sporniket/kicad-conversions--atari-ste-motherboard--c300780-001/gallery/06--pcb-raytrace-south-east.png

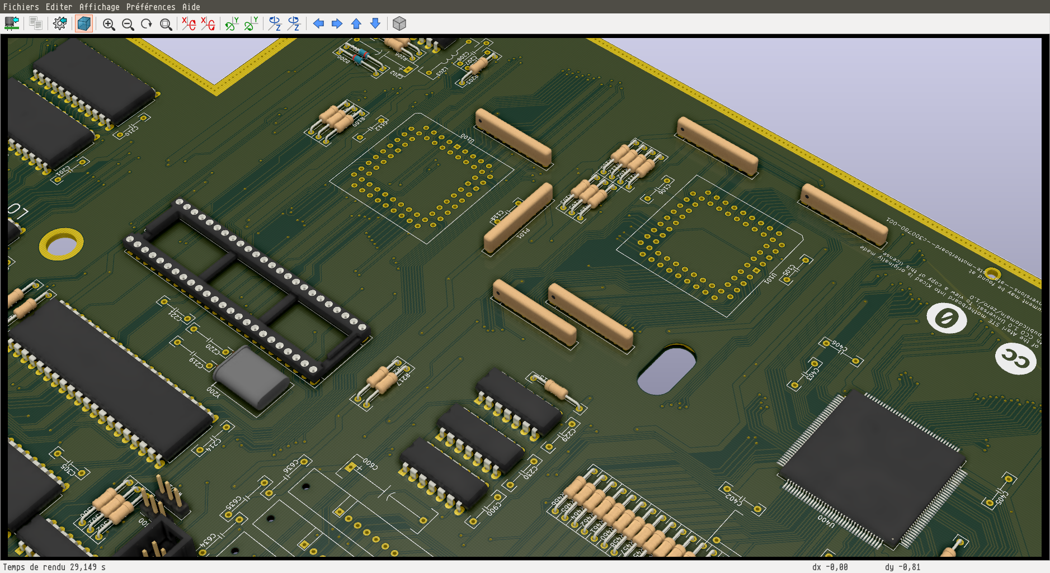
gallery/06--pcb-raytrace-south-east.png
