sporniket/kicad-conversions--atari-ste-motherboard--c300780-001/subsheet_100.kicad_sch

## KiCad design subsheet_100.kicad_sch (2025-09-03)

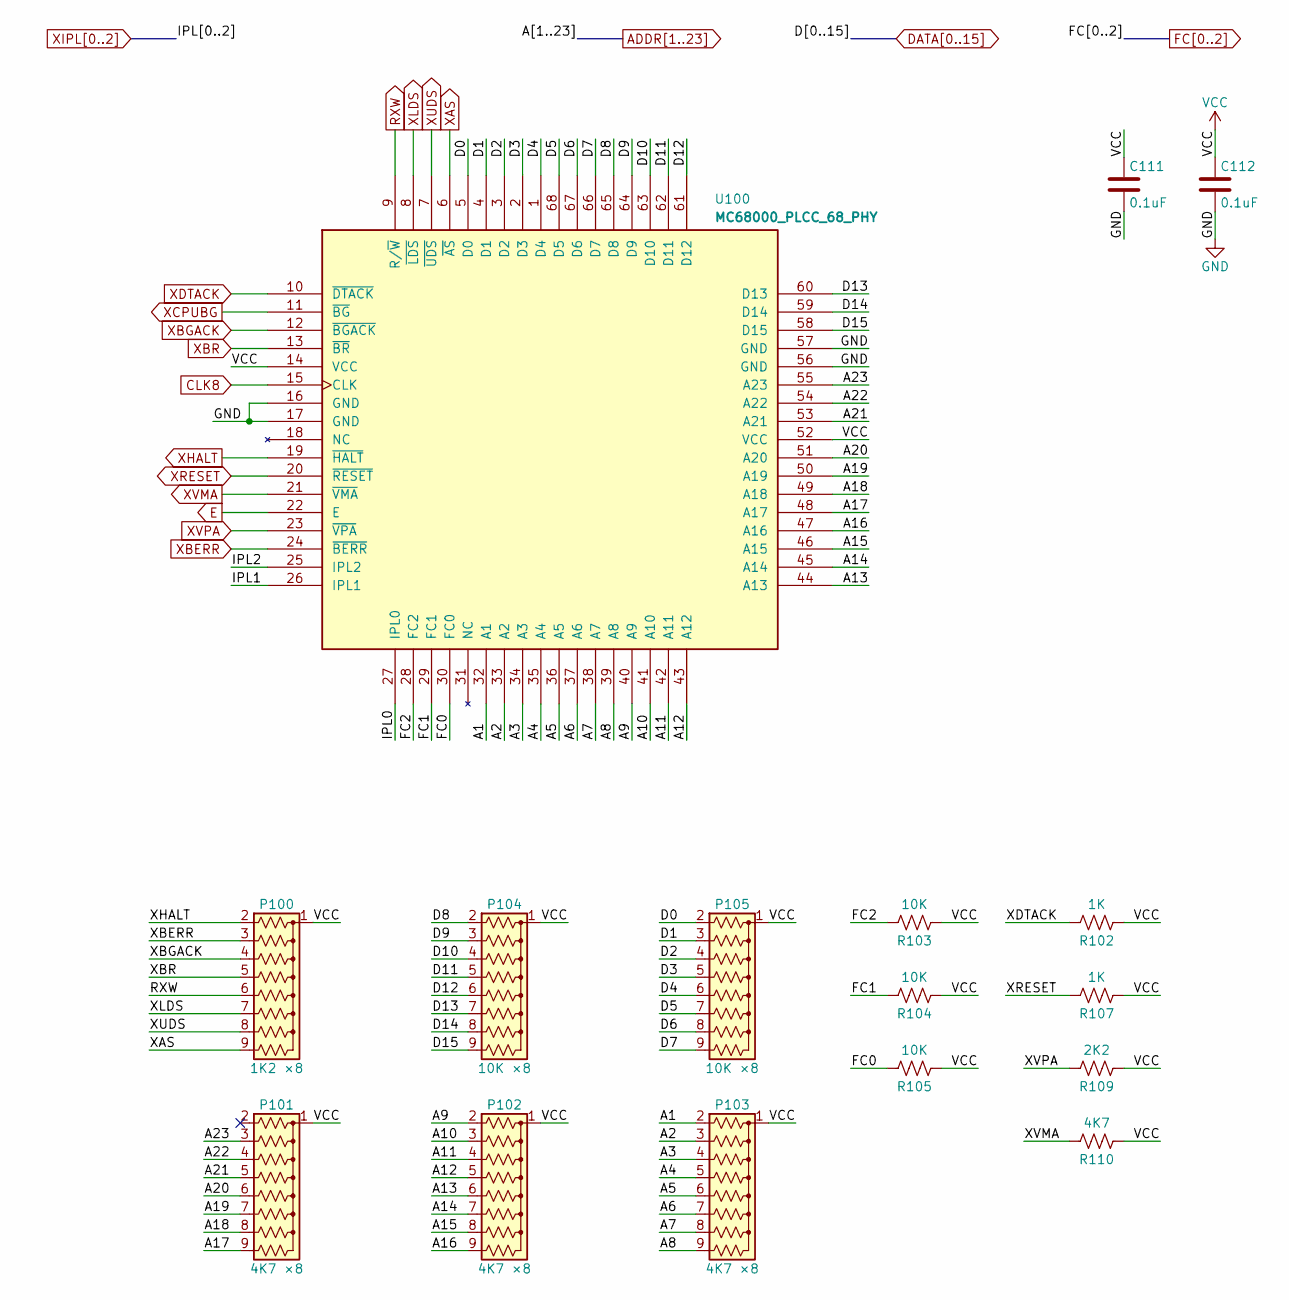
[picture p8: schematic subsheet_100.kicad_sch]

Parts:
C111, C112: 0.1uF; Passive_THT_capacitor_mlcc_W2.54mm_L7.62mm
P100: 1K2 ×8; R_Array_SIP9
P101, P102, P103: 4K7 ×8; R_Array_SIP9
P104, P105: 10K ×8; R_Array_SIP9
R102, R107: 1K; Passive_THT_resistor_W2.54mm_L12.70mm
R103, R104, R105: 10K; Passive_THT_resistor_W2.54mm_L12.70mm
R109: 2K2; Passive_THT_resistor_W2.54mm_L12.70mm
R110: 4K7; Passive_THT_resistor_W2.54mm_L12.70mm
U100: MC68000_PLCC_68_PHY; PLCC-68_THT-Socket

Connections:
A1: P103.2 (R1), U100.32 (A1)
A2: P103.3 (R2), U100.33 (A2)
A3: P103.4 (R3), U100.34 (A3)
A4: P103.5 (R4), U100.35 (A4)
A5: P103.6 (R5), U100.36 (A5)
A6: P103.7 (R6), U100.37 (A6)
A7: P103.8 (R7), U100.38 (A7)
A8: P103.9 (R8), U100.39 (A8)
A9: P102.2 (R1), U100.40 (A9)
A10: P102.3 (R2), U100.41 (A10)
A11: P102.4 (R3), U100.42 (A11)
A12: P102.5 (R4), U100.43 (A12)
A13: P102.6 (R5), U100.44 (A13)
A14: P102.7 (R6), U100.45 (A14)
A15: P102.8 (R7), U100.46 (A15)
A16: P102.9 (R8), U100.47 (A16)
A17: P101.9 (R8), U100.48 (A17)
A18: P101.8 (R7), U100.49 (A18)
A19: P101.7 (R6), U100.50 (A19)
A20: P101.6 (R5), U100.51 (A20)
A21: P101.5 (R4), U100.53 (A21)
A22: P101.4 (R3), U100.54 (A22)
A23: P101.3 (R2), U100.55 (A23)
CLK8: U100.15 (CLK)
D0: P105.2 (R1), U100.5 (D0)
D1: P105.3 (R2), U100.4 (D1)
D2: P105.4 (R3), U100.3 (D2)
D3: P105.5 (R4), U100.2 (D3)
D4: P105.6 (R5), U100.1 (D4)
D5: P105.7 (R6), U100.68 (D5)
D6: P105.8 (R7), U100.67 (D6)
D7: P105.9 (R8), U100.66 (D7)
D8: P104.2 (R1), U100.65 (D8)
D9: P104.3 (R2), U100.64 (D9)
D10: P104.4 (R3), U100.63 (D10)
D11: P104.5 (R4), U100.62 (D11)
D12: P104.6 (R5), U100.61 (D12)
D13: P104.7 (R6), U100.60 (D13)
D14: P104.8 (R7), U100.59 (D14)
D15: P104.9 (R8), U100.58 (D15)
E: U100.22 (E)
FC0: R105.2, U100.30 (FC0)
FC1: R104.2, U100.29 (FC1)
FC2: R103.2, U100.28 (FC2)
GND: C111.2, C112.2, U100.16 (GND), U100.17 (GND), U100.56 (GND), U100.57 (GND)
IPL0: U100.27 (IPL0)
IPL1: U100.26 (IPL1)
IPL2: U100.25 (IPL2)
RXW: P100.6 (R5), U100.9 (R/~W)
VCC: C111.1, C112.1, P100.1 (common), P101.1 (common), P102.1 (common), P103.1 (common), P104.1 (common), P105.1 (common), R102.1, R103.1, R104.1, R105.1, R107.1, R109.1, R110.1, U100.14 (VCC), U100.52 (VCC)
XAS: P100.9 (R8), U100.6 (~AS)
XBERR: P100.3 (R2), U100.24 (~BERR)
XBGACK: P100.4 (R3), U100.12 (~BGACK)
XBR: P100.5 (R4), U100.13 (~BR)
XCPUBG: U100.11 (~BG)
XDTACK: R102.2, U100.10 (~DTACK)
XHALT: P100.2 (R1), U100.19 (~HALT)
XLDS: P100.7 (R6), U100.8 (~LDS)
XRESET: R107.2, U100.20 (~RESET)
XUDS: P100.8 (R7), U100.7 (~UDS)
XVMA: R110.2, U100.21 (~VMA)
XVPA: R109.2, U100.23 (~VPA)
