sporniket/kicad-conversions--atari-ste-motherboard--c300780-001/subsheet_101.kicad_sch

## KiCad design subsheet_101.kicad_sch (2025-09-03)

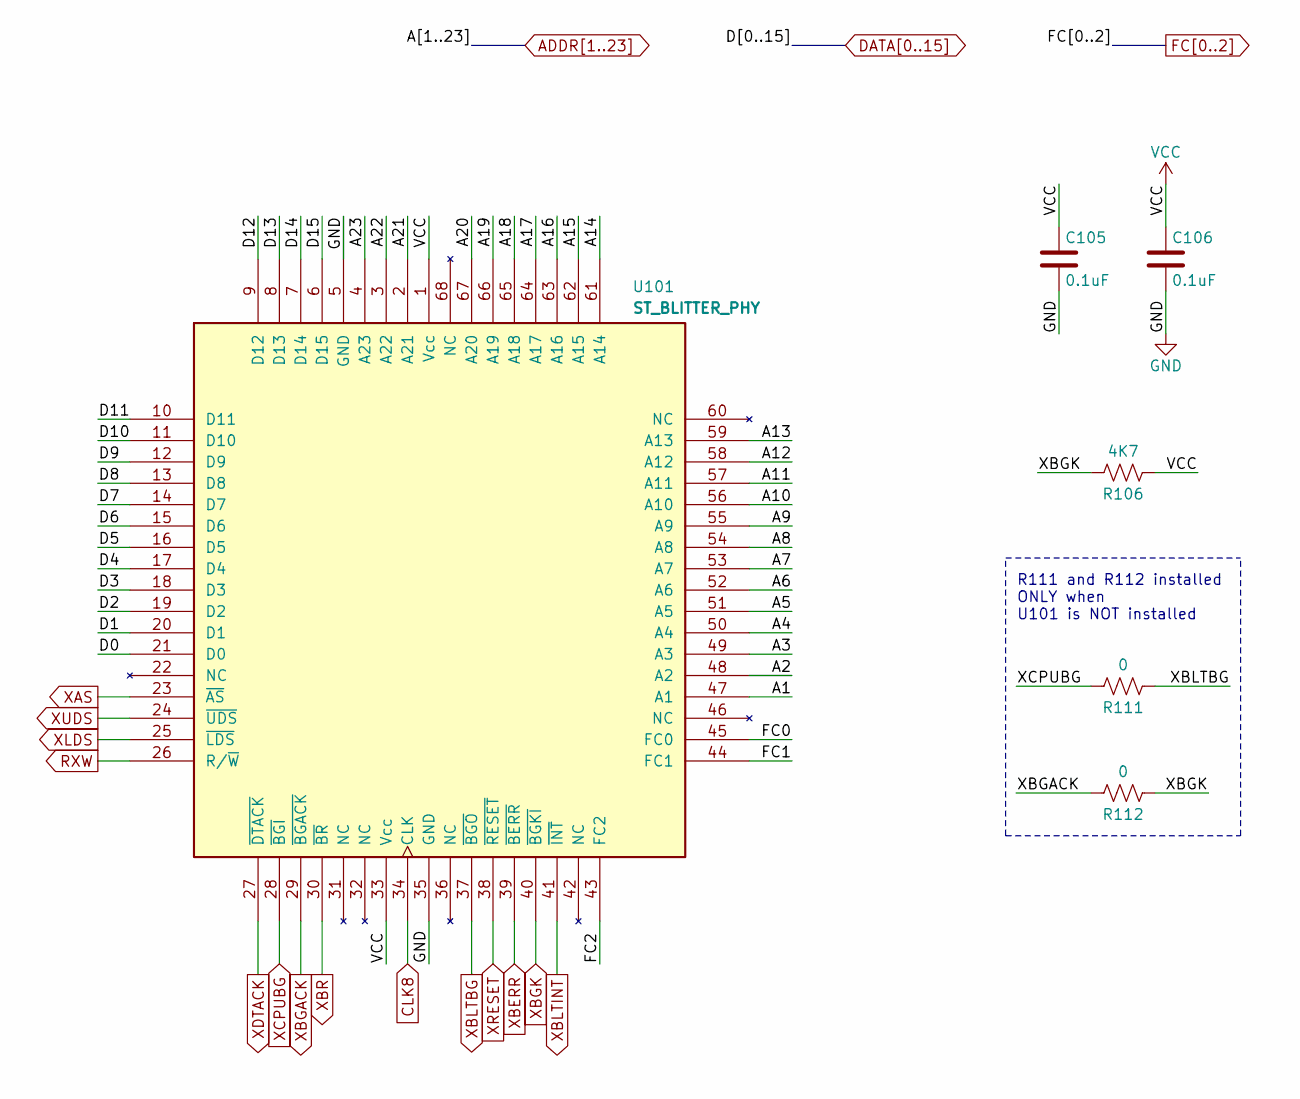
[picture p9: schematic subsheet_101.kicad_sch]

Parts:
C105, C106: 0.1uF; Passive_THT_capacitor_mlcc_W2.54mm_L7.62mm
R106: 4K7; Passive_THT_resistor_W2.54mm_L12.70mm
R111, R112: 0; Passive_THT_resistor_W2.54mm_L12.70mm
U101: ST_BLITTER_PHY; PLCC-68_THT-Socket

Connections:
A1: U101.47 (A1)
A2: U101.48 (A2)
A3: U101.49 (A3)
A4: U101.50 (A4)
A5: U101.51 (A5)
A6: U101.52 (A6)
A7: U101.53 (A7)
A8: U101.54 (A8)
A9: U101.55 (A9)
A10: U101.56 (A10)
A11: U101.57 (A11)
A12: U101.58 (A12)
A13: U101.59 (A13)
A14: U101.61 (A14)
A15: U101.62 (A15)
A16: U101.63 (A16)
A17: U101.64 (A17)
A18: U101.65 (A18)
A19: U101.66 (A19)
A20: U101.67 (A20)
A21: U101.2 (A21)
A22: U101.3 (A22)
A23: U101.4 (A23)
CLK8: U101.34 (CLK)
D0: U101.21 (D0)
D1: U101.20 (D1)
D2: U101.19 (D2)
D3: U101.18 (D3)
D4: U101.17 (D4)
D5: U101.16 (D5)
D6: U101.15 (D6)
D7: U101.14 (D7)
D8: U101.13 (D8)
D9: U101.12 (D9)
D10: U101.11 (D10)
D11: U101.10 (D11)
D12: U101.9 (D12)
D13: U101.8 (D13)
D14: U101.7 (D14)
D15: U101.6 (D15)
FC0: U101.45 (FC0)
FC1: U101.44 (FC1)
FC2: U101.43 (FC2)
GND: C105.2, C106.2, U101.5 (GND), U101.35 (GND)
RXW: U101.26 (R/~W)
VCC: C105.1, C106.1, R106.1, U101.1 (Vcc), U101.33 (Vcc)
XAS: U101.23 (~AS)
XBERR: U101.39 (~BERR)
XBGACK: R112.2, U101.29 (~BGACK)
XBGK: R106.2, R112.1, U101.40 (~BGKI)
XBLTBG: R111.1, U101.37 (~BGO)
XBLTINT: U101.41 (~INT)
XBR: U101.30 (~BR)
XCPUBG: R111.2, U101.28 (~BGI)
XDTACK: U101.27 (~DTACK)
XLDS: U101.25 (~LDS)
XRESET: U101.38 (~RESET)
XUDS: U101.24 (~UDS)

Notes on the sheet:
R111 and R112 installed ONLY when U101 is NOT installed
