sporniket/kicad-conversions--atari-ste-motherboard--c300780-001/subsheet_102.kicad_sch

## KiCad design subsheet_102.kicad_sch (2025-09-03)

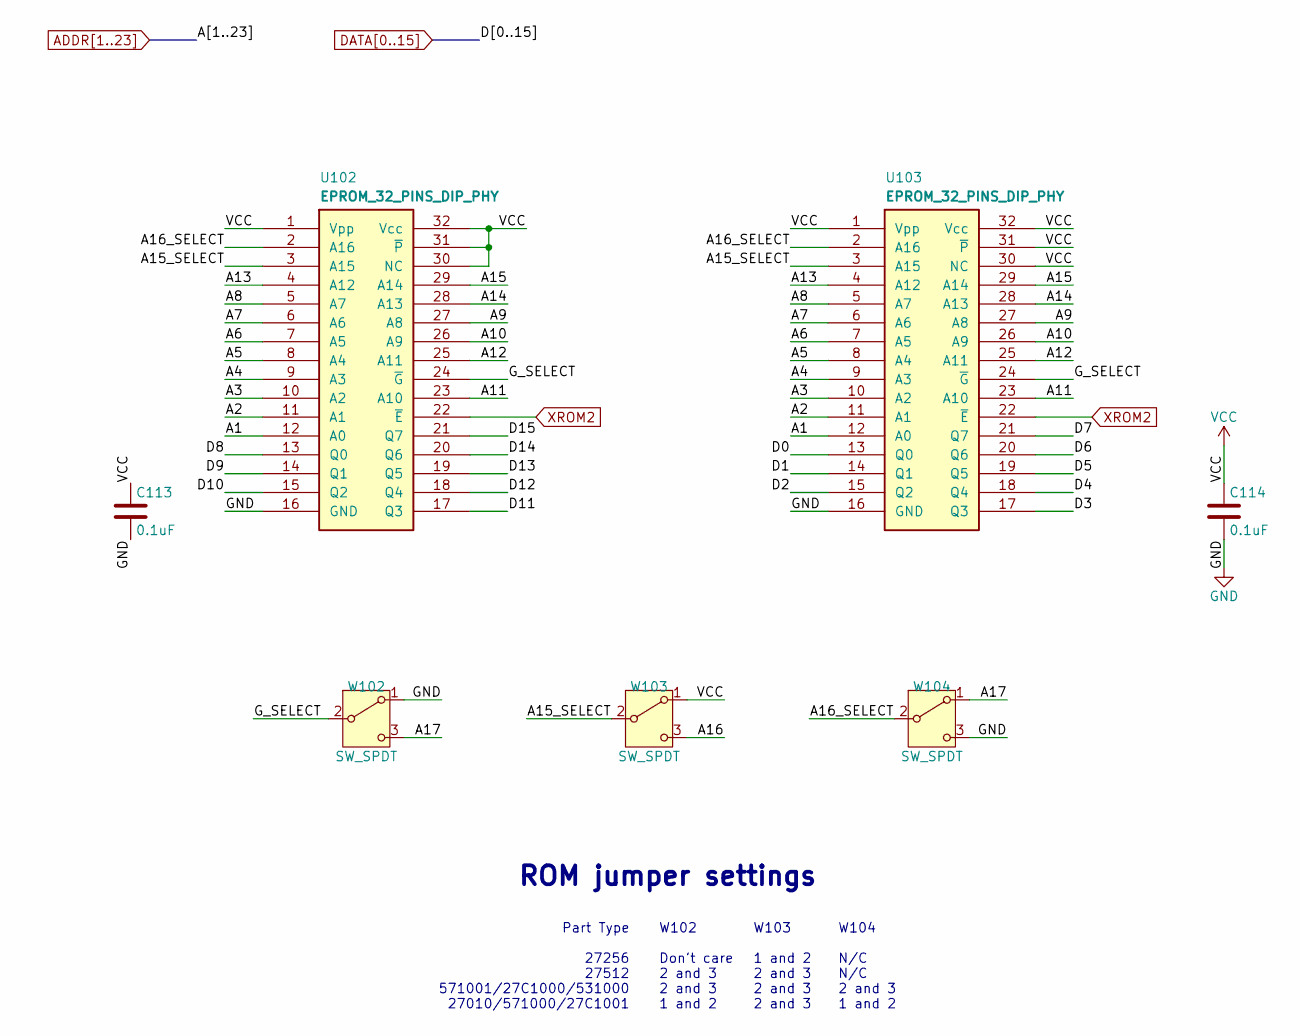
[picture p10: schematic subsheet_102.kicad_sch]

Parts:
C113, C114: 0.1uF; Passive_THT_capacitor_mlcc_W2.54mm_L7.62mm
U102, U103: EPROM_32_PINS_DIP_PHY; DIP-32_W15.24mm_LongPads
W102, W103, W104: SW_SPDT; PinHeader_1x03_P2.54mm_Vertical

Connections:
A1: U102.12 (A0), U103.12 (A0)
A2: U102.11 (A1), U103.11 (A1)
A3: U102.10 (A2), U103.10 (A2)
A4: U102.9 (A3), U103.9 (A3)
A5: U102.8 (A4), U103.8 (A4)
A6: U102.7 (A5), U103.7 (A5)
A7: U102.6 (A6), U103.6 (A6)
A8: U102.5 (A7), U103.5 (A7)
A9: U102.27 (A8), U103.27 (A8)
A10: U102.26 (A9), U103.26 (A9)
A11: U102.23 (A10), U103.23 (A10)
A12: U102.25 (A11), U103.25 (A11)
A13: U102.4 (A12), U103.4 (A12)
A14: U102.28 (A13), U103.28 (A13)
A15: U102.29 (A14), U103.29 (A14)
A15_SELECT: U102.3 (A15), U103.3 (A15), W103.2 (B)
A16: W103.3 (C)
A16_SELECT: U102.2 (A16), U103.2 (A16), W104.2 (B)
A17: W102.3 (C), W104.1 (A)
D0: U103.13 (Q0)
D1: U103.14 (Q1)
D2: U103.15 (Q2)
D3: U103.17 (Q3)
D4: U103.18 (Q4)
D5: U103.19 (Q5)
D6: U103.20 (Q6)
D7: U103.21 (Q7)
D8: U102.13 (Q0)
D9: U102.14 (Q1)
D10: U102.15 (Q2)
D11: U102.17 (Q3)
D12: U102.18 (Q4)
D13: U102.19 (Q5)
D14: U102.20 (Q6)
D15: U102.21 (Q7)
GND: C113.2, C114.2, U102.16 (GND), U103.16 (GND), W102.1 (A), W104.3 (C)
G_SELECT: U102.24 (~G), U103.24 (~G), W102.2 (B)
VCC: C113.1, C114.1, U102.1 (Vpp), U102.30 (NC), U102.31 (~P), U102.32 (Vcc), U103.1 (Vpp), U103.30 (NC), U103.31 (~P), U103.32 (Vcc), W103.1 (A)
XROM2: U102.22 (~E), U103.22 (~E)

Notes on the sheet:
W102 Don't care 2 and 3 2 and 3 1 and 2
Part Type 27256 27512 571001/27C1000/531000 27010/571000/27C1001
W104 N/C N/C 2 and 3 1 and 2
W103 1 and 2 2 and 3 2 and 3 2 and 3
ROM jumper settings
