sporniket/kicad-conversions--atari-ste-motherboard--c300780-001/subsheet_103.kicad_sch

## KiCad design subsheet_103.kicad_sch (2025-09-03)

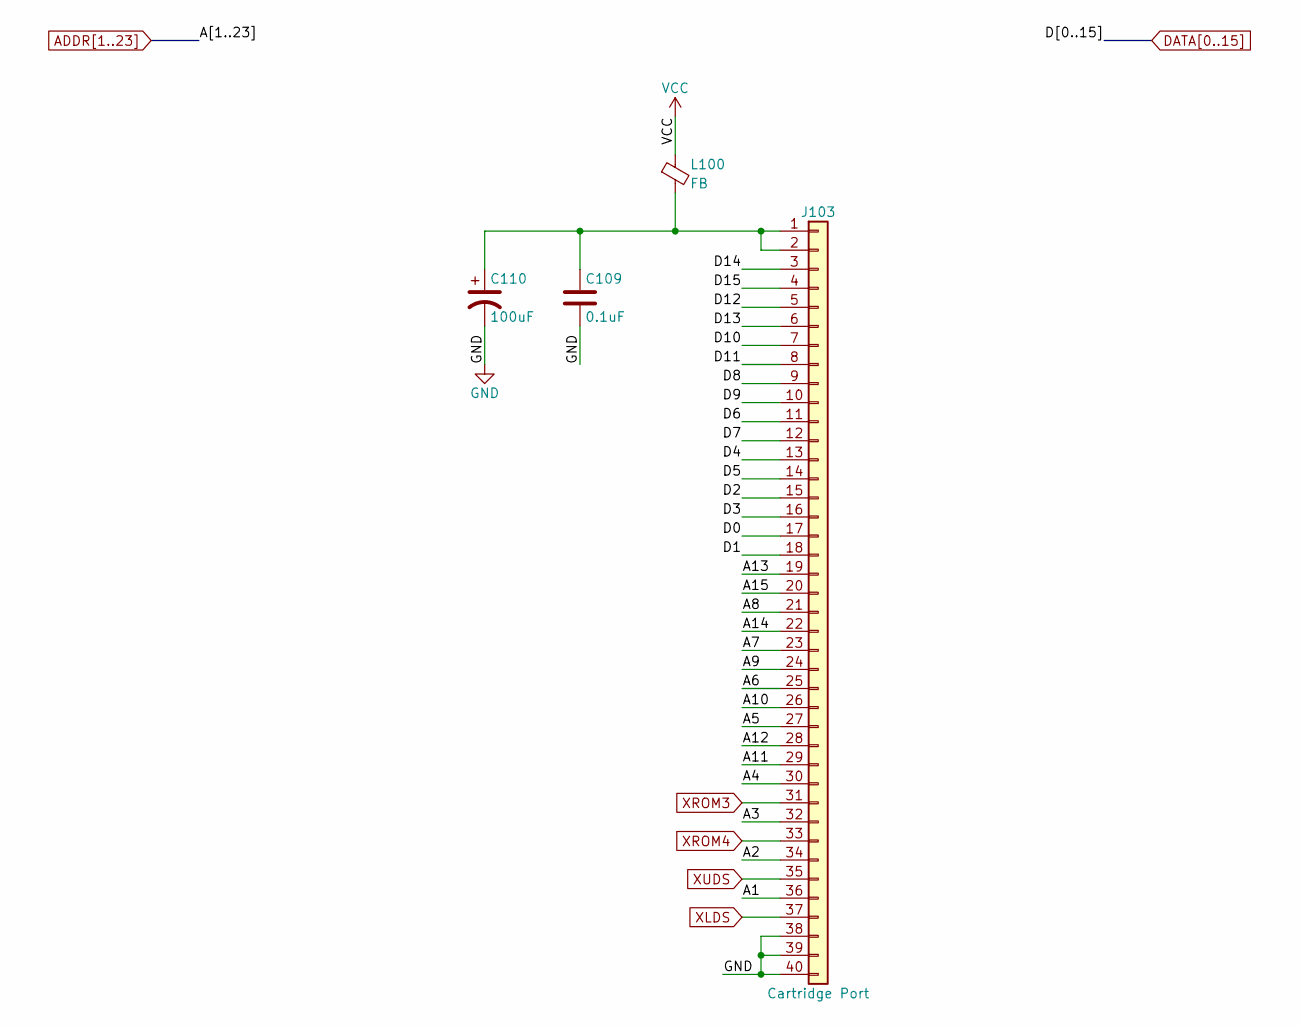
[picture p11: schematic subsheet_103.kicad_sch]

Parts:
C109: 0.1uF; Passive_THT_capacitor_mlcc_W2.54mm_L7.62mm
C110: 100uF; Passive_THT_capacitor_polarized_W6.35mm_L20.32mm
J103: Cartridge Port; socket-edge-pcb_40p_P2.01mm
L100: FB; Passive_THT_ferrite_bead_W3.81mm_L15.24mm

Connections:
A1: J103.36
A2: J103.34
A3: J103.32
A4: J103.30
A5: J103.27
A6: J103.25
A7: J103.23
A8: J103.21
A9: J103.24
A10: J103.26
A11: J103.29
A12: J103.28
A13: J103.19
A14: J103.22
A15: J103.20
D0: J103.17
D1: J103.18
D2: J103.15
D3: J103.16
D4: J103.13
D5: J103.14
D6: J103.11
D7: J103.12
D8: J103.9
D9: J103.10
D10: J103.7
D11: J103.8
D12: J103.5
D13: J103.6
D14: J103.3
D15: J103.4
GND: C109.2, C110.2, J103.38, J103.39, J103.40
unnamed: C109.1, C110.1, J103.1, J103.2, L100.2
VCC: L100.1
XLDS: J103.37
XROM3: J103.31
XROM4: J103.33
XUDS: J103.35
