sporniket/kicad-conversions--atari-ste-motherboard--c300780-001/subsheet_104.kicad_sch

## KiCad design subsheet_104.kicad_sch (2025-09-03)

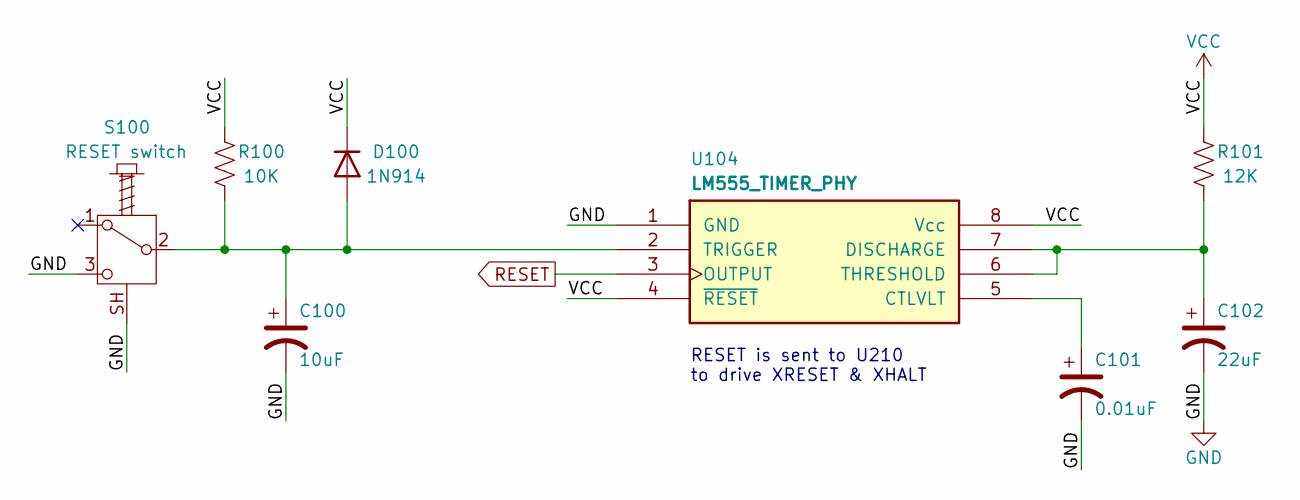
[picture p12: schematic subsheet_104.kicad_sch]

Parts:
C100: 10uF; Passive_THT_capacitor_polarized_W5.08mm_L17.78mm
C101: 0.01uF; Passive_THT_capacitor_W2.54mm_L10.16mm
C102: 22uF; Passive_THT_capacitor_polarized_W6.35mm_L20.32mm
D100: 1N914; Passive_THT_diode_W2.54mm_L12.70mm
R100: 10K; Passive_THT_resistor_W2.54mm_L12.70mm
R101: 12K; Passive_THT_resistor_W2.54mm_L12.70mm
S100: RESET switch; switch-spdt-momentary-action_Reset_pushbutton
U104: LM555_TIMER_PHY; DIP-8_W7.62mm_LongPads

Connections:
GND: C100.2, C101.2, C102.2, S100.3 (C), S100.SH (Shield), U104.1 (GND)
unnamed: C100.1, D100.2 (A), R100.2, S100.2 (B), U104.2 (TRIGGER)
unnamed: C101.1, U104.5 (CTLVLT)
unnamed: C102.1, R101.2, U104.6 (THRESHOLD), U104.7 (DISCHARGE)
RESET: U104.3 (OUTPUT)
VCC: D100.1 (K), R100.1, R101.1, U104.4 (~RESET), U104.8 (Vcc)

Notes on the sheet:
RESET is sent to U210 to drive XRESET & XHALT
