sporniket/kicad-conversions--atari-ste-motherboard--c300780-001/subsheet_105.kicad_sch

## KiCad design subsheet_105.kicad_sch (2025-09-03)

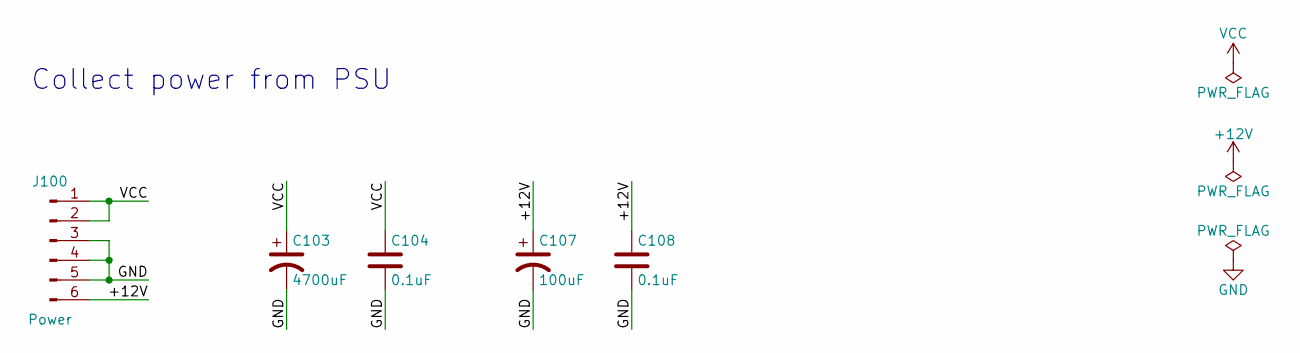
[picture p13: schematic subsheet_105.kicad_sch]

Parts:
C103: 4700uF; Passive_THT_capacitor_polarized_W16.51mm_L45.72mm
C104, C108: 0.1uF; Passive_THT_capacitor_mlcc_W2.54mm_L7.62mm
C107: 100uF; Passive_THT_capacitor_polarized_W6.35mm_L20.32mm
J100: Power; Molex_KK-254_AE-6410-06A_1x06_P2.54mm_Vertical

Connections:
+12V: C107.1, C108.1, J100.6
GND: C103.2, C104.2, C107.2, C108.2, J100.3, J100.4, J100.5
VCC: C103.1, C104.1, J100.1, J100.2

Notes on the sheet:
Collect power from PSU
