sporniket/kicad-conversions--atari-ste-motherboard--c300780-001/subsheet_106.kicad_sch

## KiCad design subsheet_106.kicad_sch (2025-09-03)

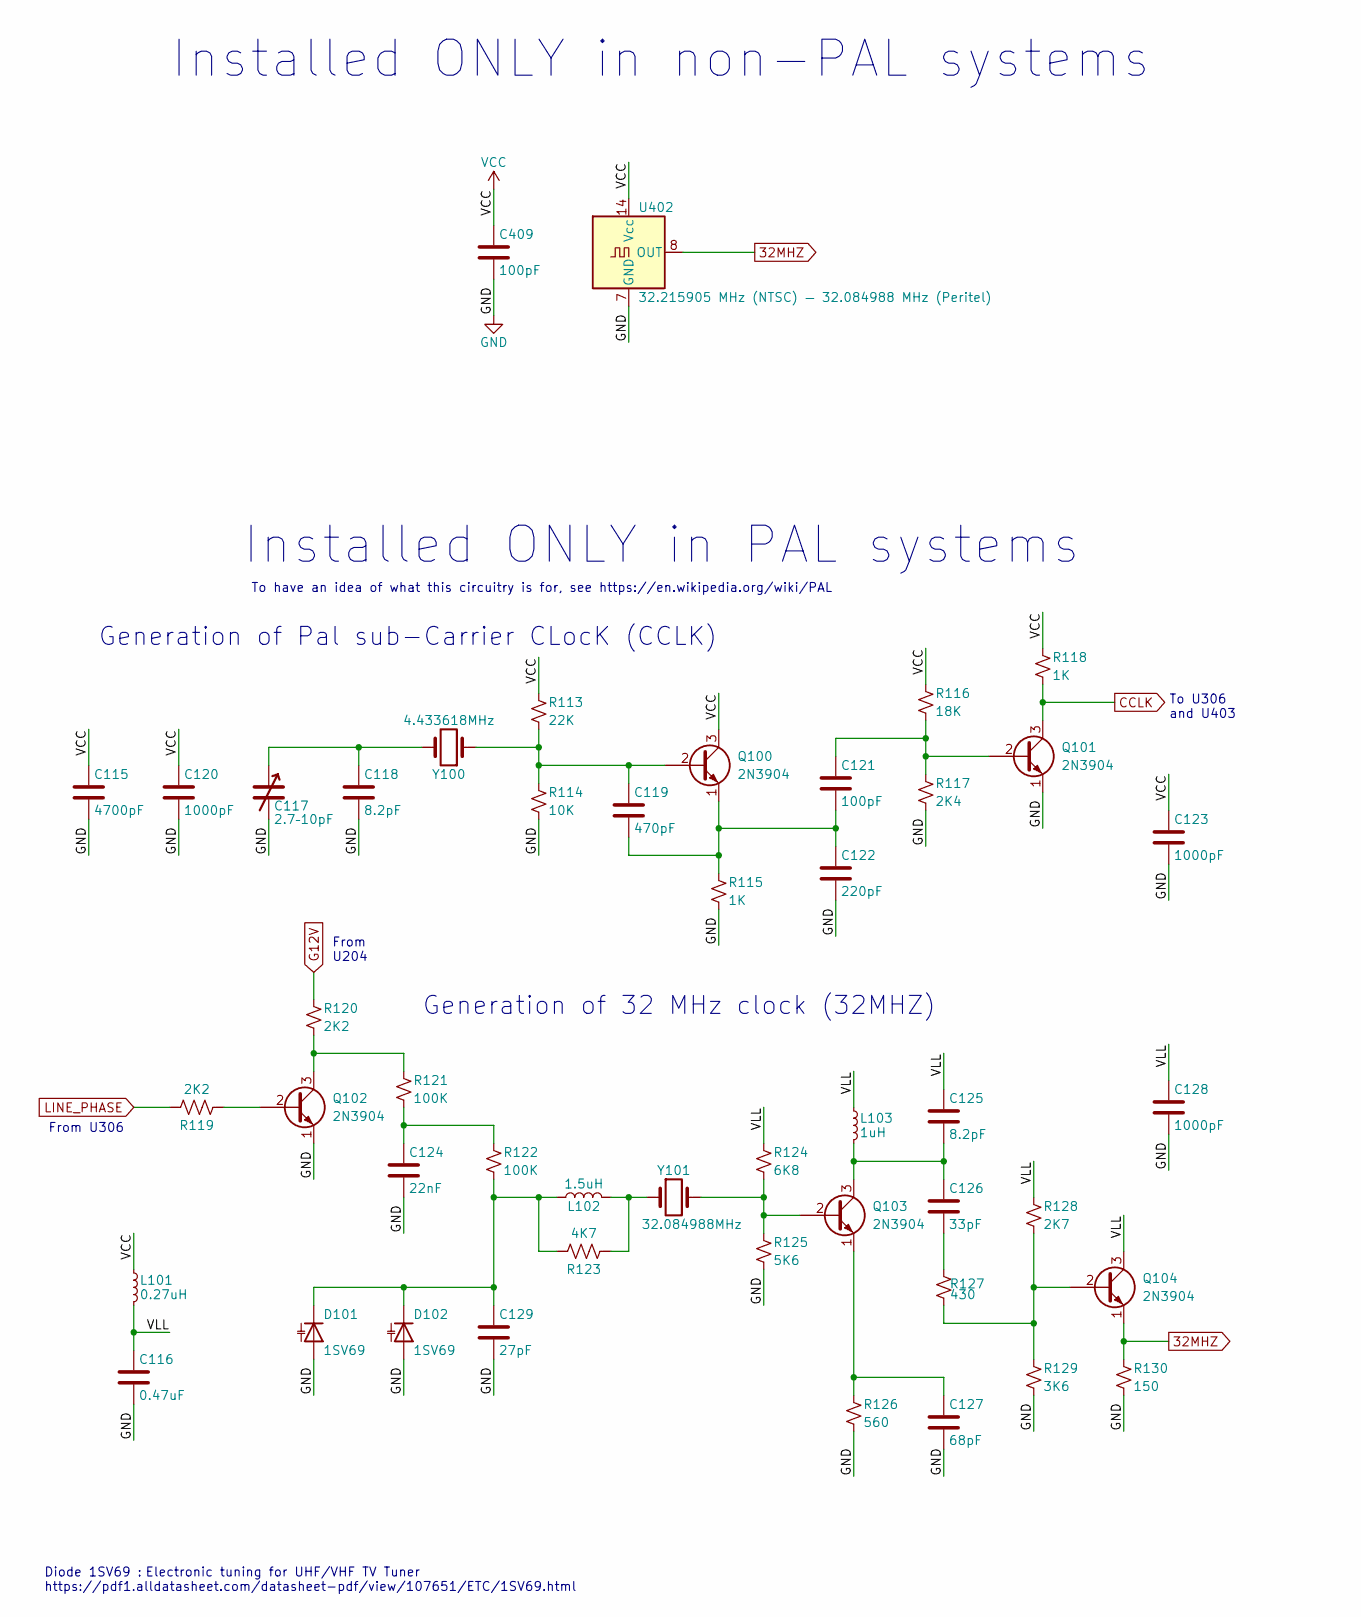
[picture p14: schematic subsheet_106.kicad_sch]

Parts:
C115: 4700pF; Passive_THT_capacitor_W2.54mm_L10.16mm
C116: 0.47uF; Passive_THT_capacitor_mlcc_W2.54mm_L10.16mm
C117: 2.7–10pF; Passive_THT_variable_capacitor_rad_D7.62mm_P5.08mm
C118: 8.2pF; Passive_THT_capacitor_W2.54mm_L12.70mm
C119: 470pF; Passive_THT_capacitor_W2.54mm_L12.70mm
C120: 1000pF; Passive_THT_capacitor_W2.54mm_L12.70mm
C121: 100pF; Passive_THT_capacitor_W2.54mm_L10.16mm
C122: 220pF; Passive_THT_capacitor_W2.54mm_L12.70mm
C123, C128: 1000pF; Passive_THT_capacitor_W2.54mm_L10.16mm
C124: 22nF; Passive_THT_capacitor_W2.54mm_L10.16mm
C125: 8.2pF; Passive_THT_capacitor_W2.54mm_L10.16mm
C126: 33pF; Passive_THT_capacitor_W2.54mm_L10.16mm
C127: 68pF; Passive_THT_capacitor_W2.54mm_L10.16mm
C129: 27pF; Passive_THT_capacitor_W2.54mm_L10.16mm
C409: 100pF; Passive_THT_capacitor_mlcc_W2.54mm_L7.62mm
D101, D102: 1SV69; Passive_THT_diode_W2.54mm_L12.70mm
L101: 0.27uH; Passive_THT_inductor_W5.08mm_L15.24mm
L102: 1.5uH; Passive_THT_inductor_W5.08mm_L15.24mm
L103: 1uH; Passive_THT_inductor_W5.08mm_L15.24mm
Q100, Q101, Q102, Q103, Q104: 2N3904; TO-92_Inline_Wide
R113: 22K; Passive_THT_resistor_W2.54mm_L12.70mm
R114: 10K; Passive_THT_resistor_W2.54mm_L12.70mm
R115, R118: 1K; Passive_THT_resistor_W2.54mm_L12.70mm
R116: 18K; Passive_THT_resistor_W2.54mm_L12.70mm
R117: 2K4; Passive_THT_resistor_W2.54mm_L12.70mm
R119, R120: 2K2; Passive_THT_resistor_W2.54mm_L12.70mm
R121, R122: 100K; Passive_THT_resistor_W2.54mm_L12.70mm
R123: 4K7; Passive_THT_resistor_W2.54mm_L12.70mm
R124: 6K8; Passive_THT_resistor_W2.54mm_L12.70mm
R125: 5K6; Passive_THT_resistor_W2.54mm_L12.70mm
R126: 560; Passive_THT_resistor_W2.54mm_L12.70mm
R127: 430; Passive_THT_resistor_W2.54mm_L12.70mm
R128: 2K7; Passive_THT_resistor_W2.54mm_L12.70mm
R129: 3K6; Passive_THT_resistor_W2.54mm_L12.70mm
R130: 150; Passive_THT_resistor_W2.54mm_L12.70mm
U402: 32.215905 MHz (NTSC) — 32.084988 MHz (Peritel); Oscillator_DIP-14
Y100: 4.433618MHz; Crystal_HC18-U_Horizontal
Y101: 32.084988MHz; Crystal_HC18-U_Horizontal

Connections:
32MHZ: Q104.1 (E), R130.1, U402.8 (OUT)
CCLK: Q101.3 (C), R118.2
G12V: R120.1
GND: C115.2, C116.2, C117.2, C118.2, C120.2, C122.2, C123.2, C124.2, C127.2, C128.2, C129.2, C409.2, D101.2 (A), D102.2 (A), Q101.1 (E), Q102.1 (E), R114.2, R115.2, R117.2, R125.2, R126.2, R129.2, R130.2, U402.7 (GND)
LINE_PHASE: R119.2
unnamed: C117.1, C118.1, Y100.2
unnamed: C119.1, Q100.2 (B), R113.2, R114.1, Y100.1
unnamed: C119.2, C121.2, C122.1, Q100.1 (E), R115.1
unnamed: C121.1, Q101.2 (B), R116.2, R117.1
unnamed: C124.1, R121.2, R122.1
unnamed: C125.2, C126.1, L103.2, Q103.3 (C)
unnamed: C126.2, R127.1
unnamed: C127.1, Q103.1 (E), R126.1
unnamed: C129.1, D101.1 (K), D102.1 (K), L102.1, R122.2, R123.2
unnamed: L102.2, R123.1, Y101.1
unnamed: Q102.2 (B), R119.1
unnamed: Q102.3 (C), R120.2, R121.1
unnamed: Q103.2 (B), R124.2, R125.1, Y101.2
unnamed: Q104.2 (B), R127.2, R128.2, R129.1
VCC: C115.1, C120.1, C123.1, C409.1, L101.1, Q100.3 (C), R113.1, R116.1, R118.1, U402.14 (Vcc)
VLL: C116.1, C125.1, C128.1, L101.2, L103.1, Q104.3 (C), R124.1, R128.1

Notes on the sheet:
Installed ONLY in non-PAL systems
From U204
Diode 1SV69 : Electronic tuning for UHF/VHF TV Tuner https://pdf1.alldatasheet.com/datasheet-pdf/view/107651/ETC/1SV69.html
Generation of Pal sub-Carrier CLocK (CCLK)
Generation of 32 MHz clock (32MHZ)
From U306
To U306 and U403
Installed ONLY in PAL systems
To have an idea of what this circuitry is for, see https://en.wikipedia.org/wiki/PAL
