sporniket/kicad-conversions--atari-ste-motherboard--c300780-001/subsheet_200.kicad_sch

## KiCad design subsheet_200.kicad_sch (2025-09-03)

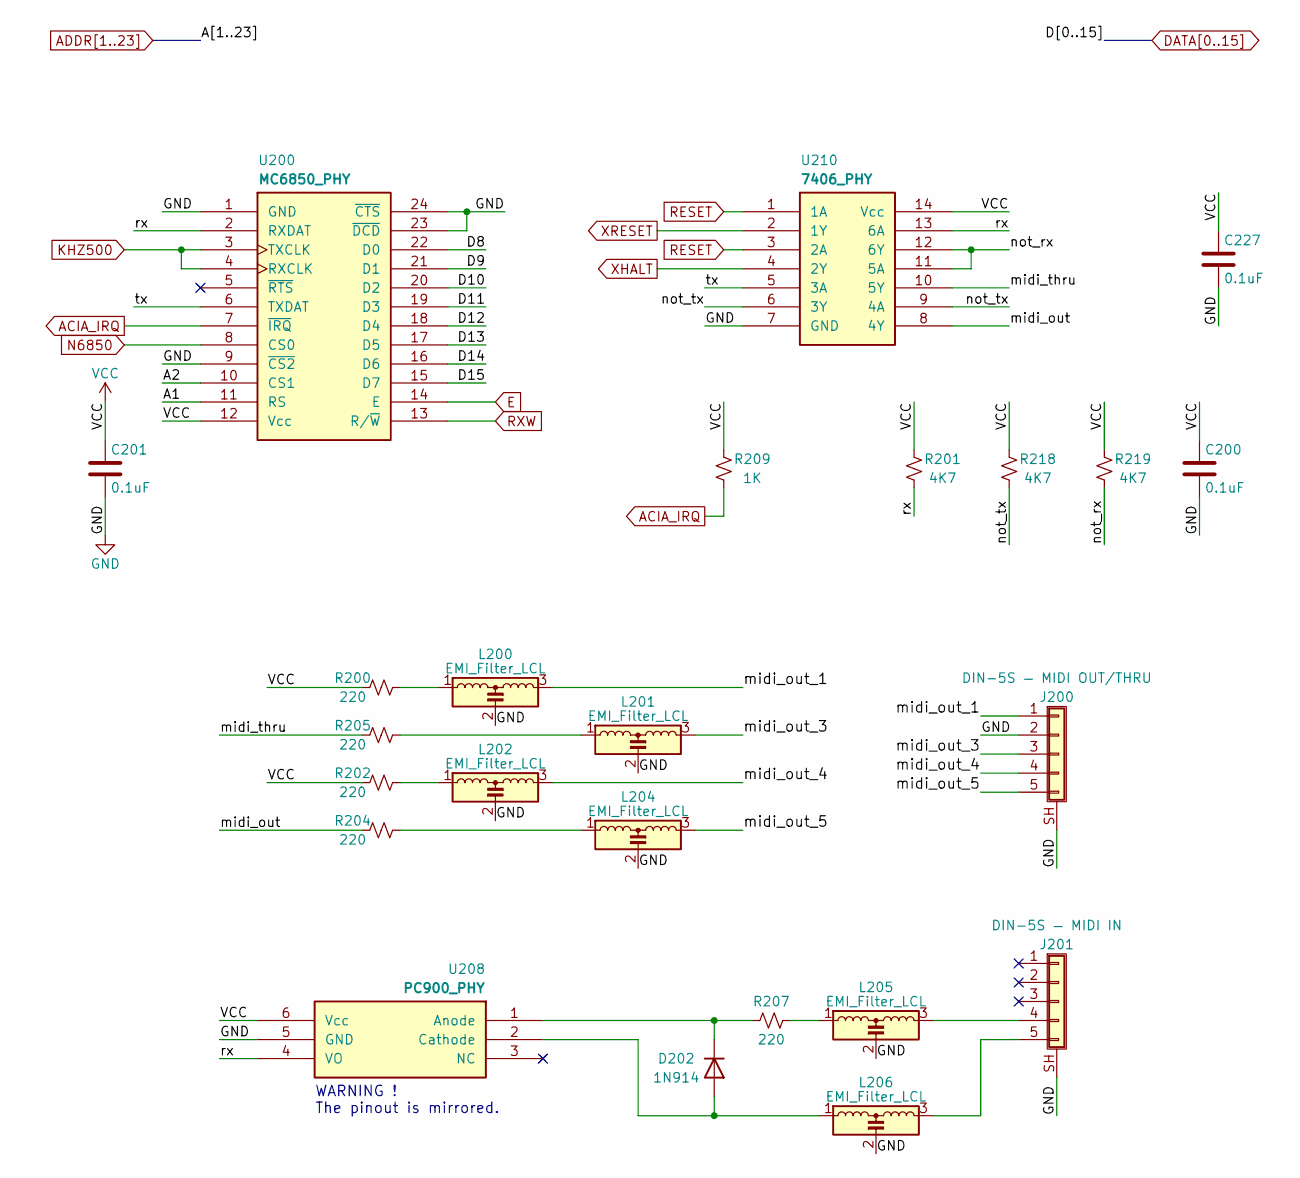
[picture p15: schematic subsheet_200.kicad_sch]

Parts:
C200, C201, C227: 0.1uF; Passive_THT_capacitor_mlcc_W2.54mm_L7.62mm
D202: 1N914; Passive_THT_diode_W2.54mm_L12.70mm
J200: DIN-5S — MIDI OUT/THRU; socket-din-5
J201: DIN-5S — MIDI IN; socket-din-5
L200, L201, L202, L204, L205, L206: EMI_Filter_LCL; Passive_THT_EMI_filter_W5.08mm_L7.62mm
R200, R202, R204, R205, R207: 220; Passive_THT_resistor_W2.54mm_L12.70mm
R201, R218, R219: 4K7; Passive_THT_resistor_W2.54mm_L12.70mm
R209: 1K; Passive_THT_resistor_W2.54mm_L12.70mm
U200: MC6850_PHY; DIP-24_W15.24mm_LongPads
U208: PC900_PHY; DIP-6_W7.62mm_LongPads
U210: 7406_PHY; DIP-14_W7.62mm_LongPads

Connections:
A1: U200.11 (RS)
A2: U200.10 (CS1)
ACIA_IRQ: R209.1, U200.7 (~IRQ)
D8: U200.22 (D0)
D9: U200.21 (D1)
D10: U200.20 (D2)
D11: U200.19 (D3)
D12: U200.18 (D4)
D13: U200.17 (D5)
D14: U200.16 (D6)
D15: U200.15 (D7)
E: U200.14 (E)
GND: C200.2, C201.2, C227.2, J200.2, J200.SH (Shield), J201.SH (Shield), L200.2, L201.2, L202.2, L204.2, L205.2, L206.2, U200.1 (GND), U200.9 (~CS2), U200.23 (~DCD), U200.24 (~CTS), U208.5 (GND), U210.7 (GND)
KHZ500: U200.3 (TXCLK), U200.4 (RXCLK)
N6850: U200.8 (CS0)
unnamed: D202.1 (K), R207.2, U208.1 (Anode)
unnamed: D202.2 (A), L206.1, U208.2 (Cathode)
unnamed: J201.4, L205.3
unnamed: J201.5, L206.3
unnamed: L200.1, R200.1
unnamed: L201.1, R205.1
unnamed: L202.1, R202.1
unnamed: L204.1, R204.1
unnamed: L205.1, R207.1
RESET: U210.1 (1A), U210.3 (2A)
RXW: U200.13 (R/~W)
VCC: C200.1, C201.1, C227.1, R200.2, R201.2, R202.2, R209.2, R218.2, R219.2, U200.12 (Vcc), U208.6 (Vcc), U210.14 (Vcc)
XHALT: U210.4 (2Y)
XRESET: U210.2 (1Y)
midi_out: R204.2, U210.8 (4Y)
midi_out_1: J200.1, L200.3
midi_out_3: J200.3, L201.3
midi_out_4: J200.4, L202.3
midi_out_5: J200.5, L204.3
midi_thru: R205.2, U210.10 (5Y)
not_rx: R219.1, U210.11 (5A), U210.12 (6Y)
not_tx: R218.1, U210.6 (3Y), U210.9 (4A)
rx: R201.1, U200.2 (RXDAT), U208.4 (VO), U210.13 (6A)
tx: U200.6 (TXDAT), U210.5 (3A)

Notes on the sheet:
WARNING ! The pinout is mirrored.
