sporniket/kicad-conversions--atari-ste-motherboard--c300780-001/subsheet_201.kicad_sch

## KiCad design subsheet_201.kicad_sch (2025-09-03)

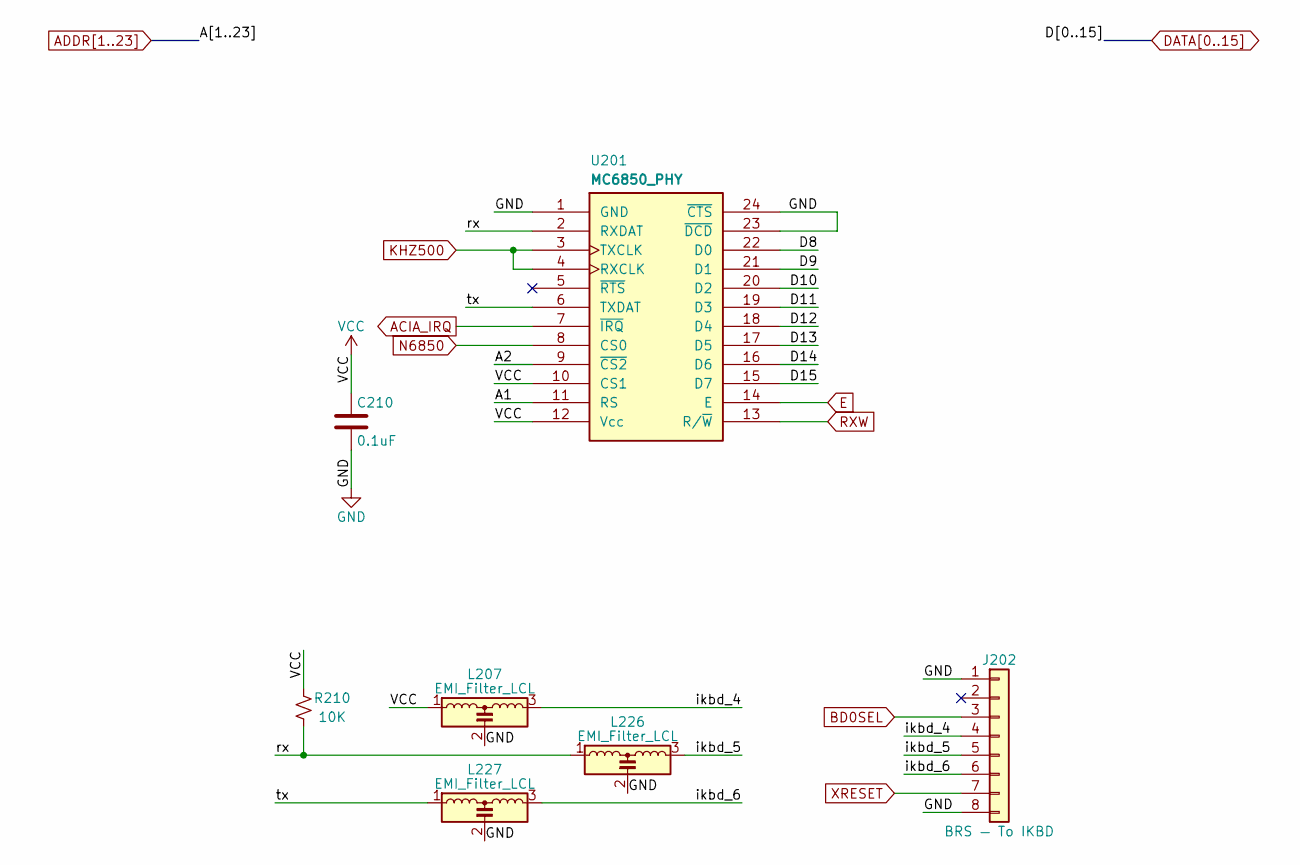
[picture p16: schematic subsheet_201.kicad_sch]

Parts:
C210: 0.1uF; Passive_THT_capacitor_mlcc_W2.54mm_L7.62mm
J202: BRS — To IKBD; PinHeader_1x08_P2.54mm_Vertical_Ikbd
L207, L226, L227: EMI_Filter_LCL; Passive_THT_EMI_filter_W5.08mm_L7.62mm
R210: 10K; Passive_THT_resistor_W2.54mm_L12.70mm
U201: MC6850_PHY; DIP-24_W15.24mm_LongPads

Connections:
A1: U201.11 (RS)
A2: U201.9 (~CS2)
ACIA_IRQ: U201.7 (~IRQ)
BD0SEL: J202.3
D8: U201.22 (D0)
D9: U201.21 (D1)
D10: U201.20 (D2)
D11: U201.19 (D3)
D12: U201.18 (D4)
D13: U201.17 (D5)
D14: U201.16 (D6)
D15: U201.15 (D7)
E: U201.14 (E)
GND: C210.2, J202.1, J202.8, L207.2, L226.2, L227.2, U201.1 (GND), U201.23 (~DCD), U201.24 (~CTS)
KHZ500: U201.3 (TXCLK), U201.4 (RXCLK)
N6850: U201.8 (CS0)
RXW: U201.13 (R/~W)
VCC: C210.1, L207.1, R210.2, U201.10 (CS1), U201.12 (Vcc)
XRESET: J202.7
ikbd_4: J202.4, L207.3
ikbd_5: J202.5, L226.3
ikbd_6: J202.6, L227.3
rx: L226.1, R210.1, U201.2 (RXDAT)
tx: L227.1, U201.6 (TXDAT)
