sporniket/kicad-conversions--atari-ste-motherboard--c300780-001/subsheet_202.kicad_sch

## KiCad design subsheet_202.kicad_sch (2025-09-03)

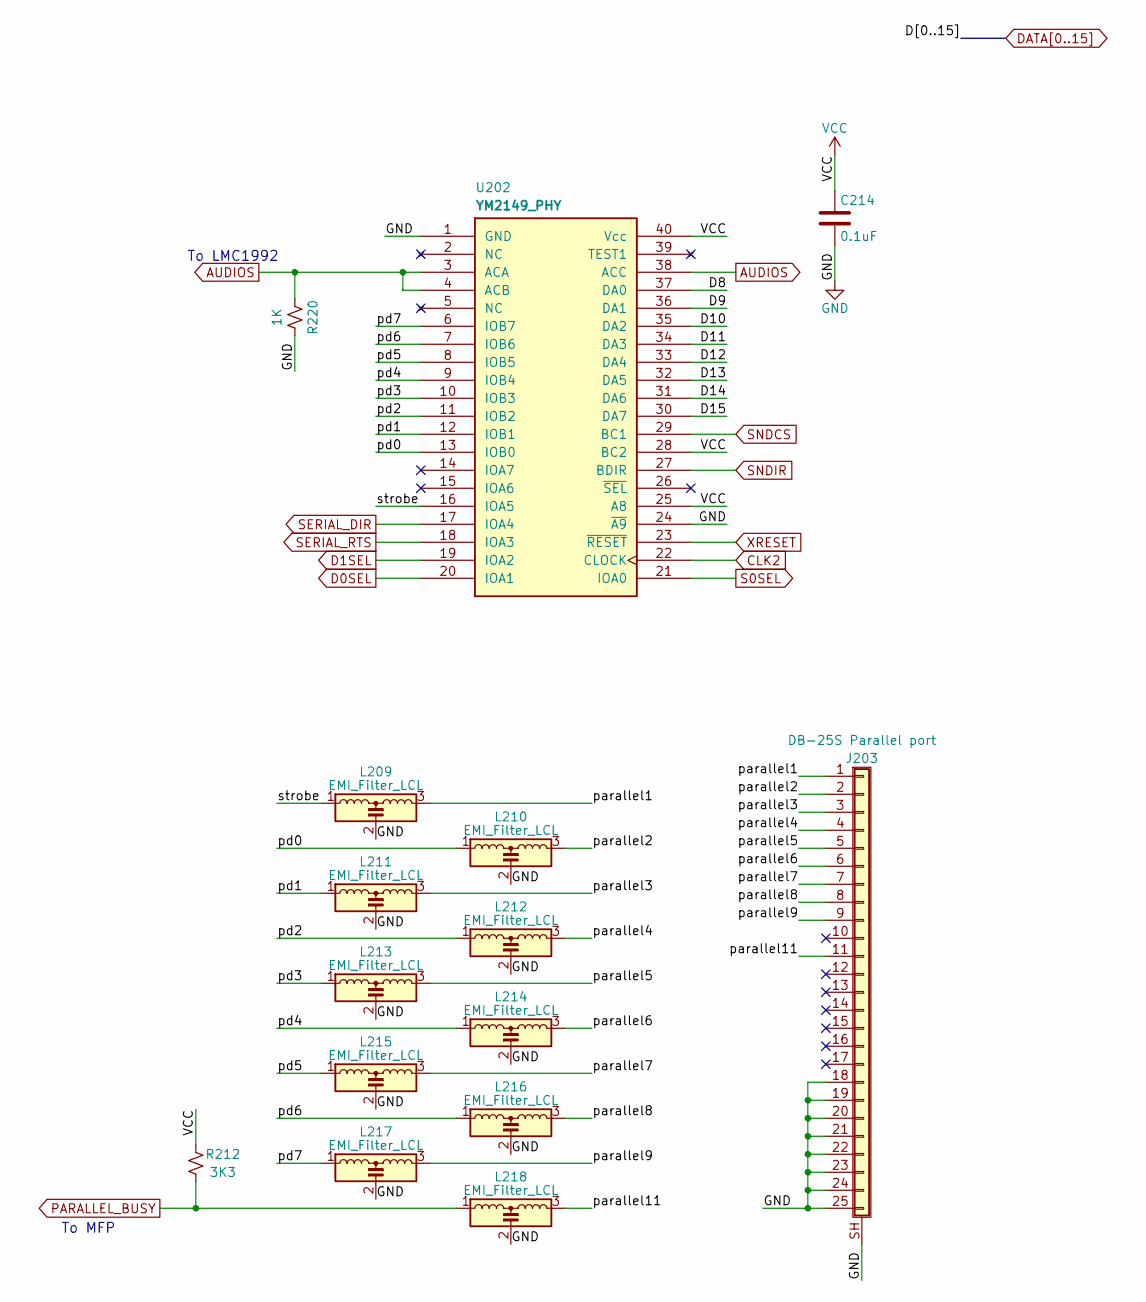
[picture p17: schematic subsheet_202.kicad_sch]

Parts:
C214: 0.1uF; Passive_THT_capacitor_mlcc_W2.54mm_L7.62mm
J203: DB-25S Parallel port; DSUB-25_Female_Horizontal_P2.77x2.84mm_EdgePinOffset7.70mm_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
L209, L210, L211, L212, L213, L214, L215, L216, L217, L218: EMI_Filter_LCL; Passive_THT_EMI_filter_W5.08mm_L7.62mm
R212: 3K3; Passive_THT_resistor_W2.54mm_L12.70mm
R220: 1K; Passive_THT_resistor_W2.54mm_L12.70mm
U202: YM2149_PHY; DIP-40_W15.24mm_LongPads

Connections:
AUDIOS: R220.2, U202.3 (ACA), U202.4 (ACB), U202.38 (ACC)
CLK2: U202.22 (CLOCK)
D0SEL: U202.20 (IOA1)
D1SEL: U202.19 (IOA2)
D8: U202.37 (DA0)
D9: U202.36 (DA1)
D10: U202.35 (DA2)
D11: U202.34 (DA3)
D12: U202.33 (DA4)
D13: U202.32 (DA5)
D14: U202.31 (DA6)
D15: U202.30 (DA7)
GND: C214.2, J203.18, J203.19, J203.20, J203.21, J203.22, J203.23, J203.24, J203.25, J203.SH (Shield), L209.2, L210.2, L211.2, L212.2, L213.2, L214.2, L215.2, L216.2, L217.2, L218.2, R220.1, U202.1 (GND), U202.24 (~A9)
PARALLEL_BUSY: L218.1, R212.2
S0SEL: U202.21 (IOA0)
SERIAL_DIR: U202.17 (IOA4)
SERIAL_RTS: U202.18 (IOA3)
SNDCS: U202.29 (BC1)
SNDIR: U202.27 (BDIR)
VCC: C214.1, R212.1, U202.25 (A8), U202.28 (BC2), U202.40 (Vcc)
XRESET: U202.23 (~RESET)
parallel1: J203.1, L209.3
parallel2: J203.2, L210.3
parallel3: J203.3, L211.3
parallel4: J203.4, L212.3
parallel5: J203.5, L213.3
parallel6: J203.6, L214.3
parallel7: J203.7, L215.3
parallel8: J203.8, L216.3
parallel9: J203.9, L217.3
parallel11: J203.11, L218.3
pd0: L210.1, U202.13 (IOB0)
pd1: L211.1, U202.12 (IOB1)
pd2: L212.1, U202.11 (IOB2)
pd3: L213.1, U202.10 (IOB3)
pd4: L214.1, U202.9 (IOB4)
pd5: L215.1, U202.8 (IOB5)
pd6: L216.1, U202.7 (IOB6)
pd7: L217.1, U202.6 (IOB7)
strobe: L209.1, U202.16 (IOA5)

Notes on the sheet:
To MFP
To LMC1992
