sporniket/kicad-conversions--atari-ste-motherboard--c300780-001/subsheet_203.kicad_sch

## KiCad design subsheet_203.kicad_sch (2025-09-03)

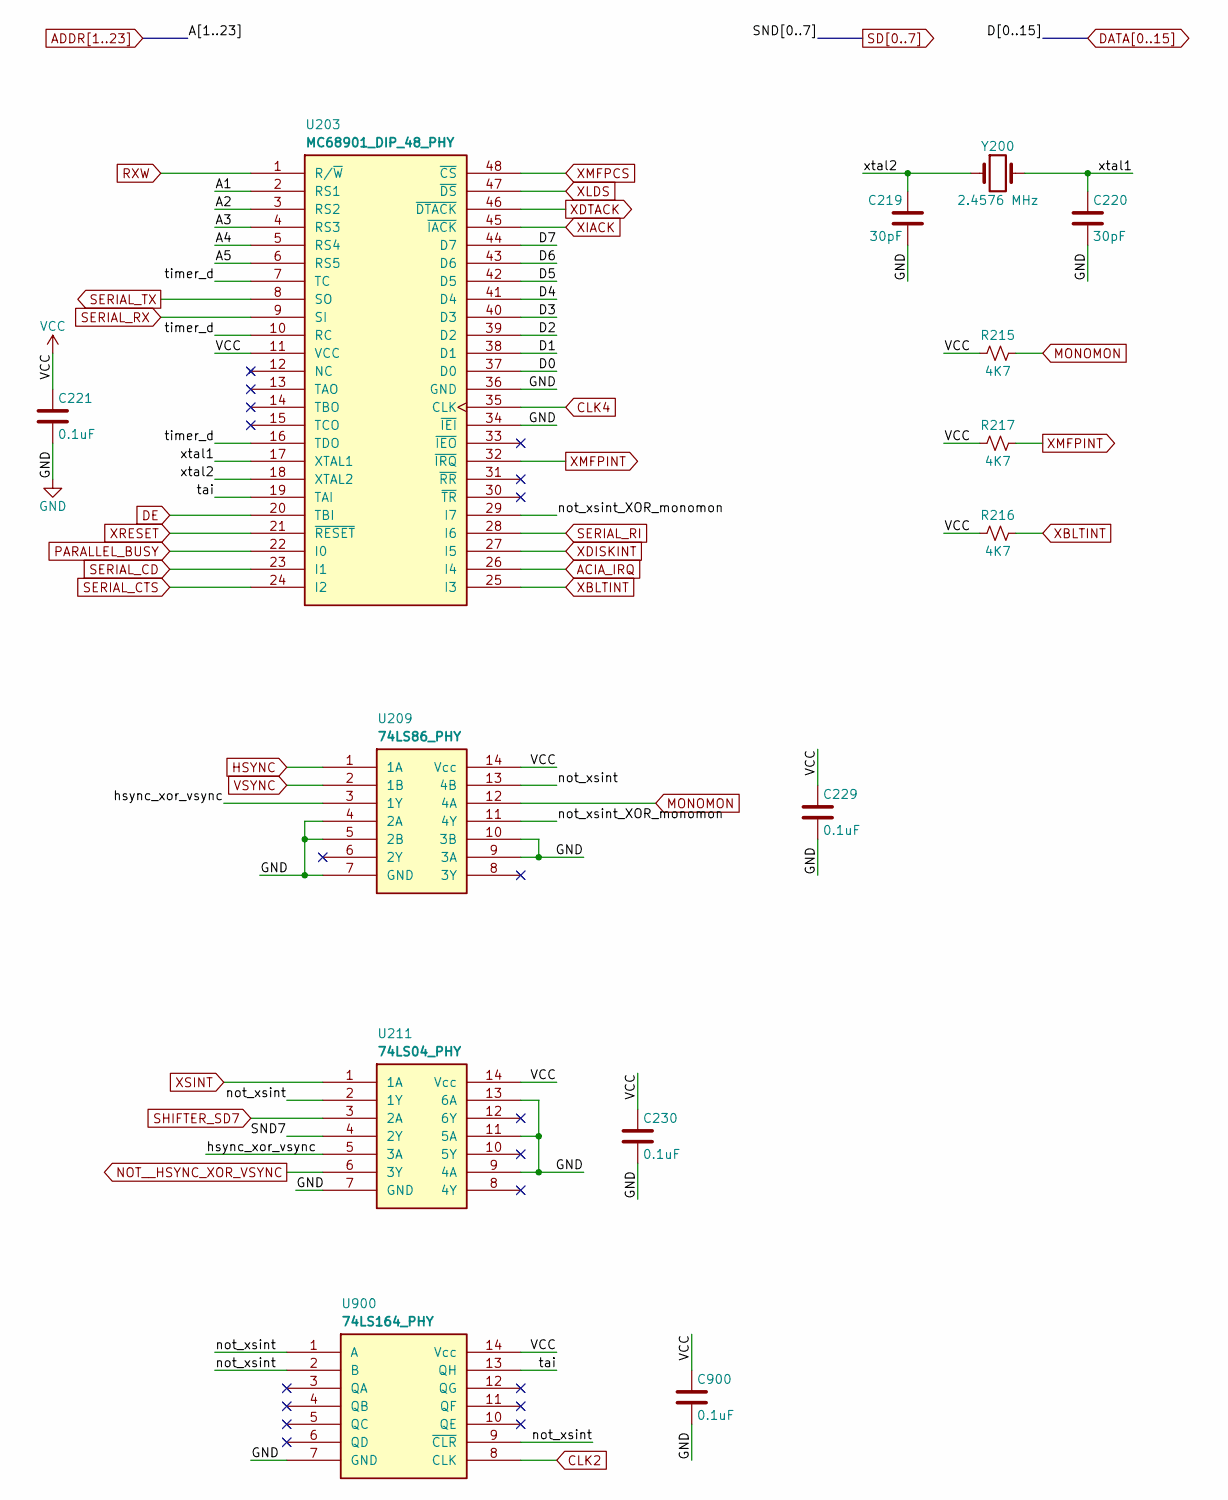
[picture p18: schematic subsheet_203.kicad_sch]

Parts:
C219, C220: 30pF; Passive_THT_capacitor_W2.54mm_L10.16mm
C221, C229, C230, C900: 0.1uF; Passive_THT_capacitor_mlcc_W2.54mm_L7.62mm
R215, R216, R217: 4K7; Passive_THT_resistor_W2.54mm_L12.70mm
U203: MC68901_DIP_48_PHY; DIP-48_W15.24mm_Socket_LongPads
U209: 74LS86_PHY; DIP-14_W7.62mm_LongPads
U211: 74LS04_PHY; DIP-14_W7.62mm_LongPads
U900: 74LS164_PHY; DIP-14_W7.62mm_LongPads
Y200: 2.4576 MHz; Crystal_HC18-U_Horizontal

Connections:
A1: U203.2 (RS1)
A2: U203.3 (RS2)
A3: U203.4 (RS3)
A4: U203.5 (RS4)
A5: U203.6 (RS5)
ACIA_IRQ: U203.26 (I4)
CLK2: U900.8 (CLK)
CLK4: U203.35 (CLK)
D0: U203.37 (D0)
D1: U203.38 (D1)
D2: U203.39 (D2)
D3: U203.40 (D3)
D4: U203.41 (D4)
D5: U203.42 (D5)
D6: U203.43 (D6)
D7: U203.44 (D7)
DE: U203.20 (TBI)
GND: C219.2, C220.2, C221.2, C229.2, C230.2, C900.2, U203.34 (~IEI), U203.36 (GND), U209.4 (2A), U209.5 (2B), U209.7 (GND), U209.9 (3A), U209.10 (3B), U211.7 (GND), U211.9 (4A), U211.11 (5A), U211.13 (6A), U900.7 (GND)
HSYNC: U209.1 (1A)
MONOMON: R215.1, U209.12 (4A)
NOT__HSYNC_XOR_VSYNC: U211.6 (3Y)
PARALLEL_BUSY: U203.22 (I0)
RXW: U203.1 (R/~W)
SERIAL_CD: U203.23 (I1)
SERIAL_CTS: U203.24 (I2)
SERIAL_RI: U203.28 (I6)
SERIAL_RX: U203.9 (SI)
SERIAL_TX: U203.8 (SO)
SHIFTER_SD7: U211.3 (2A)
SND7: U211.4 (2Y)
VCC: C221.1, C229.1, C230.1, C900.1, R215.2, R216.2, R217.2, U203.11 (VCC), U209.14 (Vcc), U211.14 (Vcc), U900.14 (Vcc)
VSYNC: U209.2 (1B)
XBLTINT: R216.1, U203.25 (I3)
XDISKINT: U203.27 (I5)
XDTACK: U203.46 (~DTACK)
XIACK: U203.45 (~IACK)
XLDS: U203.47 (~DS)
XMFPCS: U203.48 (~CS)
XMFPINT: R217.1, U203.32 (~IRQ)
XRESET: U203.21 (~RESET)
XSINT: U211.1 (1A)
hsync_xor_vsync: U209.3 (1Y), U211.5 (3A)
not_xsint: U209.13 (4B), U211.2 (1Y), U900.1 (A), U900.2 (B), U900.9 (~CLR)
not_xsint_XOR_monomon: U203.29 (I7), U209.11 (4Y)
tai: U203.19 (TAI), U900.13 (QH)
timer_d: U203.7 (TC), U203.10 (RC), U203.16 (TDO)
xtal1: C220.1, U203.17 (XTAL1), Y200.2
xtal2: C219.1, U203.18 (XTAL2), Y200.1
