sporniket/kicad-conversions--atari-ste-motherboard--c300780-001/subsheet_204.kicad_sch

## KiCad design subsheet_204.kicad_sch (2025-09-03)

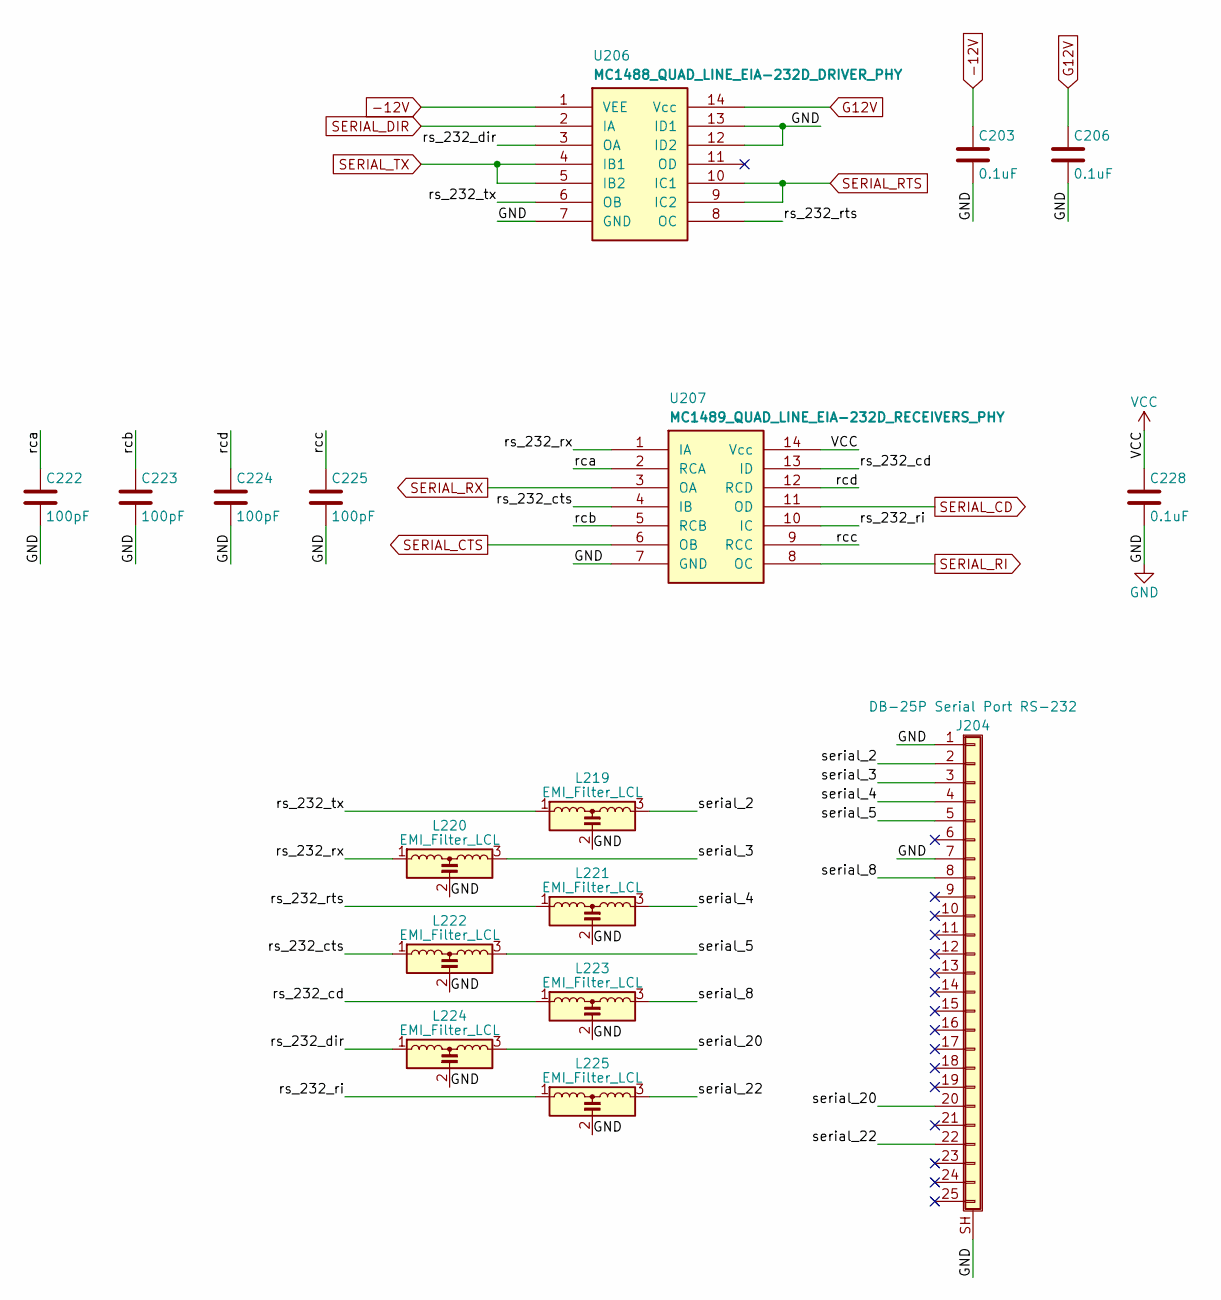
[picture p19: schematic subsheet_204.kicad_sch]

Parts:
C203, C206, C228: 0.1uF; Passive_THT_capacitor_mlcc_W2.54mm_L7.62mm
C222, C223, C224, C225: 100pF; Passive_THT_capacitor_W2.54mm_L10.16mm
J204: DB-25P Serial Port RS-232; DSUB-25_Male_Horizontal_P2.77x2.84mm_EdgePinOffset7.70mm_Ho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
L219, L220, L221, L222, L223, L224, L225: EMI_Filter_LCL; Passive_THT_EMI_filter_W5.08mm_L7.62mm
U206: MC1488_QUAD_LINE_EIA-232D_DRIVER_PHY; DIP-14_W7.62mm_LongPads
U207: MC1489_QUAD_LINE_EIA-232D_RECEIVERS_PHY; DIP-14_W7.62mm_LongPads

Connections:
-12V: C203.1, U206.1 (VEE)
G12V: C206.1, U206.14 (Vcc)
GND: C203.2, C206.2, C222.2, C223.2, C224.2, C225.2, C228.2, J204.1, J204.7, J204.SH (Shield), L219.2, L220.2, L221.2, L222.2, L223.2, L224.2, L225.2, U206.7 (GND), U206.12 (ID2), U206.13 (ID1), U207.7 (GND)
SERIAL_CD: U207.11 (OD)
SERIAL_CTS: U207.6 (OB)
SERIAL_DIR: U206.2 (IA)
SERIAL_RI: U207.8 (OC)
SERIAL_RTS: U206.9 (IC2), U206.10 (IC1)
SERIAL_RX: U207.3 (OA)
SERIAL_TX: U206.4 (IB1), U206.5 (IB2)
VCC: C228.1, U207.14 (Vcc)
rca: C222.1, U207.2 (RCA)
rcb: C223.1, U207.5 (RCB)
rcc: C225.1, U207.9 (RCC)
rcd: C224.1, U207.12 (RCD)
rs_232_cd: L223.1, U207.13 (ID)
rs_232_cts: L222.1, U207.4 (IB)
rs_232_dir: L224.1, U206.3 (OA)
rs_232_ri: L225.1, U207.10 (IC)
rs_232_rts: L221.1, U206.8 (OC)
rs_232_rx: L220.1, U207.1 (IA)
rs_232_tx: L219.1, U206.6 (OB)
serial_2: J204.2, L219.3
serial_3: J204.3, L220.3
serial_4: J204.4, L221.3
serial_5: J204.5, L222.3
serial_8: J204.8, L223.3
serial_20: J204.20, L224.3
serial_22: J204.22, L225.3
