sporniket/kicad-conversions--atari-ste-motherboard--c300780-001/subsheet_205.kicad_sch

## KiCad design subsheet_205.kicad_sch (2025-09-03)

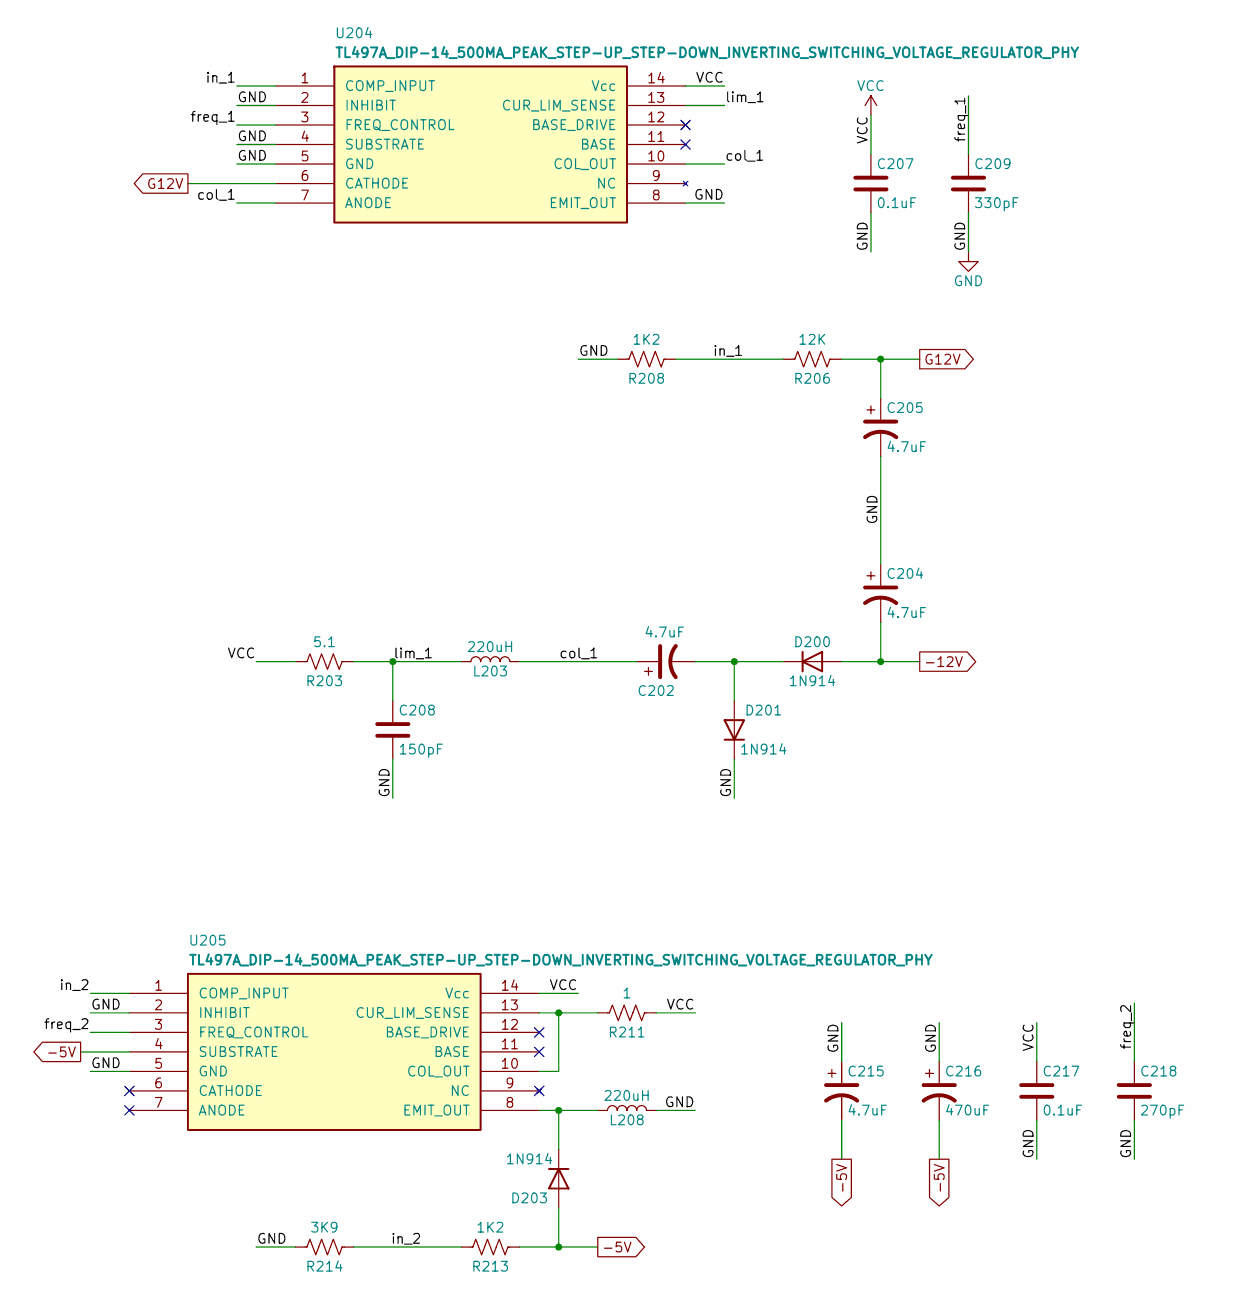
[picture p20: schematic subsheet_205.kicad_sch]

Parts:
C202, C204, C205, C215: 4.7uF; Passive_THT_capacitor_polarized_W5.08mm_L17.78mm
C207, C217: 0.1uF; Passive_THT_capacitor_mlcc_W2.54mm_L7.62mm
C208: 150pF; Passive_THT_capacitor_W2.54mm_L10.16mm
C209: 330pF; Passive_THT_capacitor_W2.54mm_L10.16mm
C216: 470uF; Passive_THT_capacitor_polarized_W10.16mm_L27.94mm
C218: 270pF; Passive_THT_capacitor_W2.54mm_L10.16mm
D200, D201, D203: 1N914; Passive_THT_diode_W2.54mm_L12.70mm
L203, L208: 220uH; Passive_THT_inductor_W5.08mm_L15.24mm
R203: 5.1; Passive_THT_resistor_W2.54mm_L12.70mm
R206: 12K; Passive_THT_resistor_W2.54mm_L12.70mm
R208, R213: 1K2; Passive_THT_resistor_W2.54mm_L12.70mm
R211: 1; Passive_THT_resistor_W2.54mm_L12.70mm
R214: 3K9; Passive_THT_resistor_W2.54mm_L12.70mm
U204, U205: TL497A_DIP-14_500MA_PEAK_STEP-UP_STEP-DOWN_INVERT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; DIP-14_W7.62mm_LongPads

Connections:
-5V: C215.2, C216.2, D203.2 (A), R213.1, U205.4 (SUBSTRATE)
-12V: C204.2, D200.2 (A)
G12V: C205.1, R206.1, U204.6 (CATHODE)
GND: C204.1, C205.2, C207.2, C208.2, C209.2, C215.1, C216.1, C217.2, C218.2, D201.1 (K), L208.2, R208.2, R214.2, U204.2 (INHIBIT), U204.4 (SUBSTRATE), U204.5 (GND), U204.8 (EMIT_OUT), U205.2 (INHIBIT), U205.5 (GND)
unnamed: C202.2, D200.1 (K), D201.2 (A)
unnamed: D203.1 (K), L208.1, U205.8 (EMIT_OUT)
unnamed: R211.2, U205.10 (COL_OUT), U205.13 (CUR_LIM_SENSE)
VCC: C207.1, C217.1, R203.2, R211.1, U204.14 (Vcc), U205.14 (Vcc)
col_1: C202.1, L203.2, U204.7 (ANODE), U204.10 (COL_OUT)
freq_1: C209.1, U204.3 (FREQ_CONTROL)
freq_2: C218.1, U205.3 (FREQ_CONTROL)
in_1: R206.2, R208.1, U204.1 (COMP_INPUT)
in_2: R213.2, R214.1, U205.1 (COMP_INPUT)
lim_1: C208.1, L203.1, R203.1, U204.13 (CUR_LIM_SENSE)
