sporniket/kicad-conversions--atari-ste-motherboard--c300780-001/subsheet_300.kicad_sch

## KiCad design subsheet_300.kicad_sch (2025-09-03)

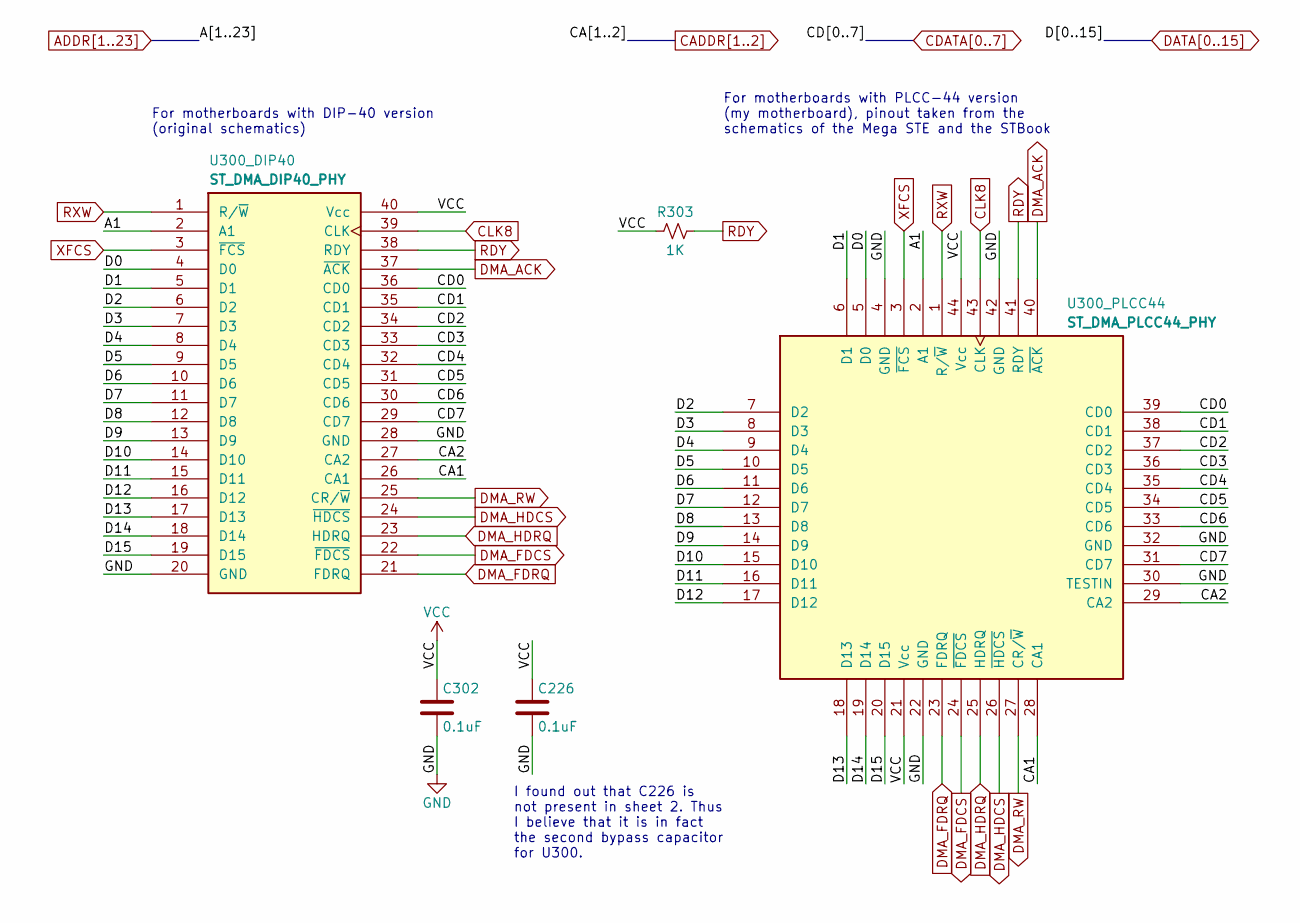
[picture p21: schematic subsheet_300.kicad_sch]

Parts:
C226, C302: 0.1uF; Passive_THT_capacitor_mlcc_W2.54mm_L7.62mm
R303: 1K; Passive_THT_resistor_W2.54mm_L12.70mm
U300_DIP40: ST_DMA_DIP40_PHY; DIP-40_W15.24mm_LongPads
U300_PLCC44: ST_DMA_PLCC44_PHY; PLCC-44_THT-Socket

Connections:
A1: U300_DIP40.2 (A1), U300_PLCC44.2 (A1)
CA1: U300_DIP40.26 (CA1), U300_PLCC44.28 (CA1)
CA2: U300_DIP40.27 (CA2), U300_PLCC44.29 (CA2)
CD0: U300_DIP40.36 (CD0), U300_PLCC44.39 (CD0)
CD1: U300_DIP40.35 (CD1), U300_PLCC44.38 (CD1)
CD2: U300_DIP40.34 (CD2), U300_PLCC44.37 (CD2)
CD3: U300_DIP40.33 (CD3), U300_PLCC44.36 (CD3)
CD4: U300_DIP40.32 (CD4), U300_PLCC44.35 (CD4)
CD5: U300_DIP40.31 (CD5), U300_PLCC44.34 (CD5)
CD6: U300_DIP40.30 (CD6), U300_PLCC44.33 (CD6)
CD7: U300_DIP40.29 (CD7), U300_PLCC44.31 (CD7)
CLK8: U300_DIP40.39 (CLK), U300_PLCC44.43 (CLK)
D0: U300_DIP40.4 (D0), U300_PLCC44.5 (D0)
D1: U300_DIP40.5 (D1), U300_PLCC44.6 (D1)
D2: U300_DIP40.6 (D2), U300_PLCC44.7 (D2)
D3: U300_DIP40.7 (D3), U300_PLCC44.8 (D3)
D4: U300_DIP40.8 (D4), U300_PLCC44.9 (D4)
D5: U300_DIP40.9 (D5), U300_PLCC44.10 (D5)
D6: U300_DIP40.10 (D6), U300_PLCC44.11 (D6)
D7: U300_DIP40.11 (D7), U300_PLCC44.12 (D7)
D8: U300_DIP40.12 (D8), U300_PLCC44.13 (D8)
D9: U300_DIP40.13 (D9), U300_PLCC44.14 (D9)
D10: U300_DIP40.14 (D10), U300_PLCC44.15 (D10)
D11: U300_DIP40.15 (D11), U300_PLCC44.16 (D11)
D12: U300_DIP40.16 (D12), U300_PLCC44.17 (D12)
D13: U300_DIP40.17 (D13), U300_PLCC44.18 (D13)
D14: U300_DIP40.18 (D14), U300_PLCC44.19 (D14)
D15: U300_DIP40.19 (D15), U300_PLCC44.20 (D15)
DMA_ACK: U300_DIP40.37 (~ACK), U300_PLCC44.40 (~ACK)
DMA_FDCS: U300_DIP40.22 (~FDCS), U300_PLCC44.24 (~FDCS)
DMA_FDRQ: U300_DIP40.21 (FDRQ), U300_PLCC44.23 (FDRQ)
DMA_HDCS: U300_DIP40.24 (~HDCS), U300_PLCC44.26 (~HDCS)
DMA_HDRQ: U300_DIP40.23 (HDRQ), U300_PLCC44.25 (HDRQ)
DMA_RW: U300_DIP40.25 (CR/~W), U300_PLCC44.27 (CR/~W)
GND: C226.2, C302.2, U300_DIP40.20 (GND), U300_DIP40.28 (GND), U300_PLCC44.4 (GND), U300_PLCC44.22 (GND), U300_PLCC44.30 (TESTIN), U300_PLCC44.32 (GND), U300_PLCC44.42 (GND)
RDY: R303.1, U300_DIP40.38 (RDY), U300_PLCC44.41 (RDY)
RXW: U300_DIP40.1 (R/~W), U300_PLCC44.1 (R/~W)
VCC: C226.1, C302.1, R303.2, U300_DIP40.40 (Vcc), U300_PLCC44.21 (Vcc), U300_PLCC44.44 (Vcc)
XFCS: U300_DIP40.3 (~FCS), U300_PLCC44.3 (~FCS)

Notes on the sheet:
For motherboards with DIP-40 version (original schematics)
I found out that C226 is not present in sheet 2. Thus I believe that it is in fact the second bypass capacitor for U300.
For motherboards with PLCC-44 version (my motherboard), pinout taken from the schematics of the Mega STE and the STBook
