sporniket/kicad-conversions--atari-ste-motherboard--c300780-001/subsheet_301.kicad_sch

## KiCad design subsheet_301.kicad_sch (2025-09-03)

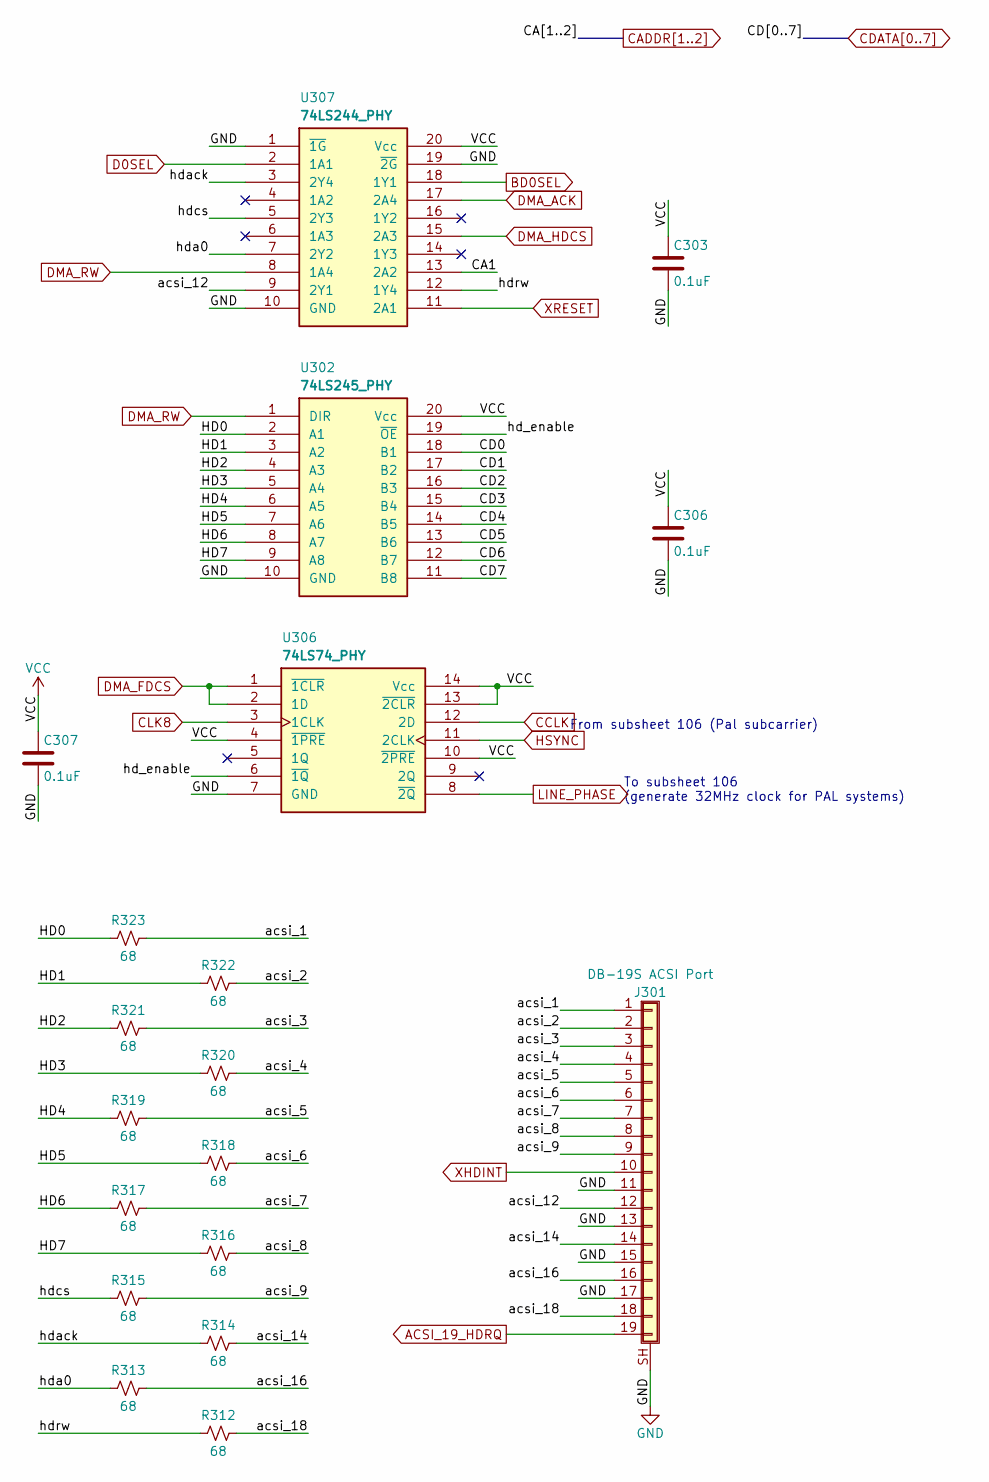
[picture p22: schematic subsheet_301.kicad_sch]

Parts:
C303, C306, C307: 0.1uF; Passive_THT_capacitor_mlcc_W2.54mm_L7.62mm
J301: DB-19S ACSI Port; DSUB-19_Female_Horizontal_P2.77x2.84mm_EdgePinOffset7.70mm_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
R312, R313, R314, R315, R316, R317, R318, R319, R320, R321, R322, R323: 68; Passive_THT_resistor_W2.54mm_L12.70mm
U302: 74LS245_PHY; DIP-20_W7.62mm_LongPads
U306: 74LS74_PHY; DIP-14_W7.62mm_LongPads
U307: 74LS244_PHY; DIP-20_W7.62mm_LongPads

Connections:
ACSI_19_HDRQ: J301.19
BD0SEL: U307.18 (1Y1)
CA1: U307.13 (2A2)
CCLK: U306.12 (2D)
CD0: U302.18 (B1)
CD1: U302.17 (B2)
CD2: U302.16 (B3)
CD3: U302.15 (B4)
CD4: U302.14 (B5)
CD5: U302.13 (B6)
CD6: U302.12 (B7)
CD7: U302.11 (B8)
CLK8: U306.3 (1CLK)
D0SEL: U307.2 (1A1)
DMA_ACK: U307.17 (2A4)
DMA_FDCS: U306.1 (~1CLR), U306.2 (1D)
DMA_HDCS: U307.15 (2A3)
DMA_RW: U302.1 (DIR), U307.8 (1A4)
GND: C303.2, C306.2, C307.2, J301.11, J301.13, J301.15, J301.17, J301.SH (Shield), U302.10 (GND), U306.7 (GND), U307.1 (~1G), U307.10 (GND), U307.19 (~2G)
HD0: R323.2, U302.2 (A1)
HD1: R322.2, U302.3 (A2)
HD2: R321.2, U302.4 (A3)
HD3: R320.2, U302.5 (A4)
HD4: R319.2, U302.6 (A5)
HD5: R318.2, U302.7 (A6)
HD6: R317.2, U302.8 (A7)
HD7: R316.2, U302.9 (A8)
HSYNC: U306.11 (2CLK)
LINE_PHASE: U306.8 (~2Q)
VCC: C303.1, C306.1, C307.1, U302.20 (Vcc), U306.4 (~1PRE), U306.10 (~2PRE), U306.13 (~2CLR), U306.14 (Vcc), U307.20 (Vcc)
XHDINT: J301.10
XRESET: U307.11 (2A1)
acsi_1: J301.1, R323.1
acsi_2: J301.2, R322.1
acsi_3: J301.3, R321.1
acsi_4: J301.4, R320.1
acsi_5: J301.5, R319.1
acsi_6: J301.6, R318.1
acsi_7: J301.7, R317.1
acsi_8: J301.8, R316.1
acsi_9: J301.9, R315.1
acsi_12: J301.12, U307.9 (2Y1)
acsi_14: J301.14, R314.1
acsi_16: J301.16, R313.1
acsi_18: J301.18, R312.1
hd_enable: U302.19 (~OE), U306.6 (~1Q)
hda0: R313.2, U307.7 (2Y2)
hdack: R314.2, U307.3 (2Y4)
hdcs: R315.2, U307.5 (2Y3)
hdrw: R312.2, U307.12 (1Y4)

Notes on the sheet:
To subsheet 106 (generate 32MHz clock for PAL systems)
From subsheet 106 (Pal subcarrier)
