sporniket/kicad-conversions--atari-ste-motherboard--c300780-001/subsheet_302.kicad_sch

## KiCad design subsheet_302.kicad_sch (2025-09-03)

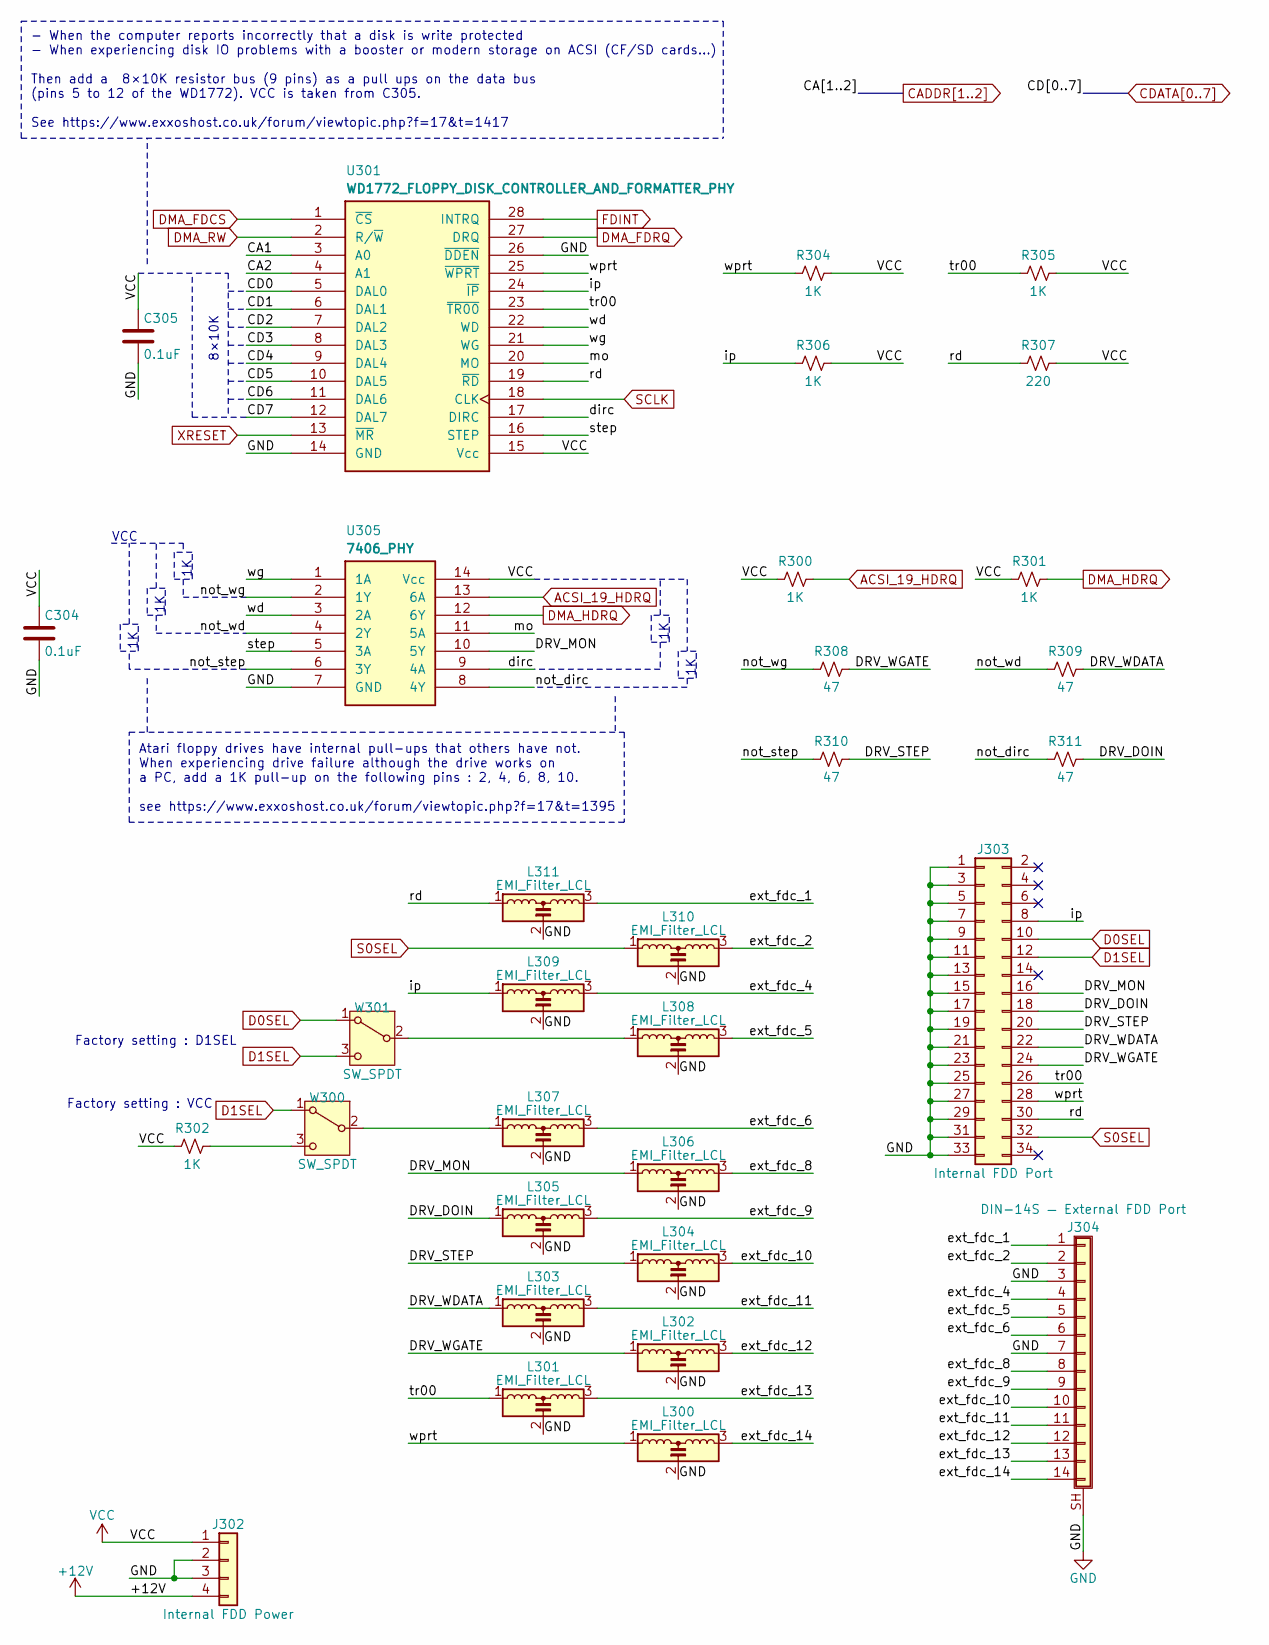
[picture p23: schematic subsheet_302.kicad_sch]

Parts:
C304, C305: 0.1uF; Passive_THT_capacitor_mlcc_W2.54mm_L7.62mm
J302: Internal FDD Power; Molex_KK-254_AE-6410-04A_1x04_P2.54mm_Vertical
J303: Internal FDD Port; IDC-Header_2x17_P2.54mm_Vertical
J304: DIN-14S — External FDD Port; socket-din-14
L300, L301, L302, L303, L304, L305, L306, L307, L308, L309, L310, L311: EMI_Filter_LCL; Passive_THT_EMI_filter_W5.08mm_L7.62mm
R300, R301, R302, R304, R305, R306: 1K; Passive_THT_resistor_W2.54mm_L12.70mm
R307: 220; Passive_THT_resistor_W2.54mm_L12.70mm
R308, R309, R310, R311: 47; Passive_THT_resistor_W2.54mm_L12.70mm
U301: WD1772_FLOPPY_DISK_CONTROLLER_AND_FORMATTER_PHY; DIP-28_W15.24mm_LongPads
U305: 7406_PHY; DIP-14_W7.62mm_LongPads
W300, W301: SW_SPDT; PinHeader_1x03_P2.54mm_Vertical

Connections:
+12V: J302.4
ACSI_19_HDRQ: R300.1, U305.13 (6A)
CA1: U301.3 (A0)
CA2: U301.4 (A1)
CD0: U301.5 (DAL0)
CD1: U301.6 (DAL1)
CD2: U301.7 (DAL2)
CD3: U301.8 (DAL3)
CD4: U301.9 (DAL4)
CD5: U301.10 (DAL5)
CD6: U301.11 (DAL6)
CD7: U301.12 (DAL7)
D0SEL: J303.10, W301.1 (A)
D1SEL: J303.12, W300.1 (A), W301.3 (C)
DMA_FDCS: U301.1 (~CS)
DMA_FDRQ: U301.27 (DRQ)
DMA_HDRQ: R301.1, U305.12 (6Y)
DMA_RW: U301.2 (R/~W)
DRV_DOIN: J303.18, L305.1, R311.1
DRV_MON: J303.16, L306.1, U305.10 (5Y)
DRV_STEP: J303.20, L304.1, R310.1
DRV_WDATA: J303.22, L303.1, R309.1
DRV_WGATE: J303.24, L302.1, R308.1
FDINT: U301.28 (INTRQ)
GND: C304.2, C305.2, J302.2, J302.3, J303.1, J303.3, J303.5, J303.7, J303.9, J303.11, J303.13, J303.15, J303.17, J303.19, J303.21, J303.23, J303.25, J303.27, J303.29, J303.31, J303.33, J304.3, J304.7, J304.SH (Shield), L300.2, L301.2, L302.2, L303.2, L304.2, L305.2, L306.2, L307.2, L308.2, L309.2, L310.2, L311.2, U301.14 (GND), U301.26 (~DDEN), U305.7 (GND)
unnamed: L307.1, W300.2 (B)
unnamed: L308.1, W301.2 (B)
unnamed: R302.1, W300.3 (C)
S0SEL: J303.32, L310.1
SCLK: U301.18 (CLK)
VCC: C304.1, C305.1, J302.1, R300.2, R301.2, R302.2, R304.1, R305.1, R306.1, R307.1, U301.15 (Vcc), U305.14 (Vcc)
XRESET: U301.13 (~MR)
dirc: U301.17 (DIRC), U305.9 (4A)
ext_fdc_1: J304.1, L311.3
ext_fdc_2: J304.2, L310.3
ext_fdc_4: J304.4, L309.3
ext_fdc_5: J304.5, L308.3
ext_fdc_6: J304.6, L307.3
ext_fdc_8: J304.8, L306.3
ext_fdc_9: J304.9, L305.3
ext_fdc_10: J304.10, L304.3
ext_fdc_11: J304.11, L303.3
ext_fdc_12: J304.12, L302.3
ext_fdc_13: J304.13, L301.3
ext_fdc_14: J304.14, L300.3
ip: J303.8, L309.1, R306.2, U301.24 (~IP)
mo: U301.20 (MO), U305.11 (5A)
not_dirc: R311.2, U305.8 (4Y)
not_step: R310.2, U305.6 (3Y)
not_wd: R309.2, U305.4 (2Y)
not_wg: R308.2, U305.2 (1Y)
rd: J303.30, L311.1, R307.2, U301.19 (~RD)
step: U301.16 (STEP), U305.5 (3A)
tr00: J303.26, L301.1, R305.2, U301.23 (~TR00)
wd: U301.22 (WD), U305.3 (2A)
wg: U301.21 (WG), U305.1 (1A)
wprt: J303.28, L300.1, R304.2, U301.25 (~WPRT)

Notes on the sheet:
VCC
Factory setting : D1SEL
- When the computer reports incorrectly that a disk is write protected - When experiencing disk IO problems with a booster or modern storage on ACSI (CF/SD cards...) Then add a 8×10K resistor bus (9 pins) as a pull ups on the data bus (pins 5 to 12 of the WD1772). VCC is taken from C305. See https: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
8×10K
Factory setting : VCC
Atari floppy drives have internal pull-ups that others have not. When experiencing drive failure although the drive works on a PC, add a 1K pull-up on the following pins : 2, 4, 6, 8, 10. see https://www.exxoshost.co.uk/forum/viewtopic.php?f=17&t=1395
