sporniket/kicad-conversions--atari-ste-motherboard--c300780-001/subsheet_303.kicad_sch

## KiCad design subsheet_303.kicad_sch (2025-09-03)

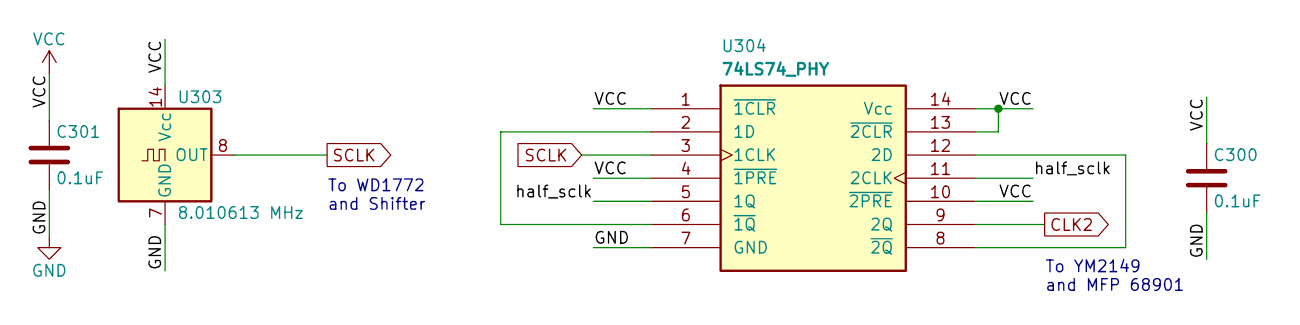
[picture p24: schematic subsheet_303.kicad_sch]

Parts:
C300, C301: 0.1uF; Passive_THT_capacitor_mlcc_W2.54mm_L7.62mm
U303: 8.010613 MHz; Oscillator_DIP-14
U304: 74LS74_PHY; DIP-14_W7.62mm_LongPads

Connections:
CLK2: U304.9 (2Q)
GND: C300.2, C301.2, U303.7 (GND), U304.7 (GND)
unnamed: U304.2 (1D), U304.6 (~1Q)
unnamed: U304.8 (~2Q), U304.12 (2D)
SCLK: U303.8 (OUT), U304.3 (1CLK)
VCC: C300.1, C301.1, U303.14 (Vcc), U304.1 (~1CLR), U304.4 (~1PRE), U304.10 (~2PRE), U304.13 (~2CLR), U304.14 (Vcc)
half_sclk: U304.5 (1Q), U304.11 (2CLK)

Notes on the sheet:
To WD1772 and Shifter
To YM2149 and MFP 68901
