sporniket/kicad-conversions--atari-ste-motherboard--c300780-001/subsheet_400.kicad_sch

## KiCad design subsheet_400.kicad_sch (2025-09-03)

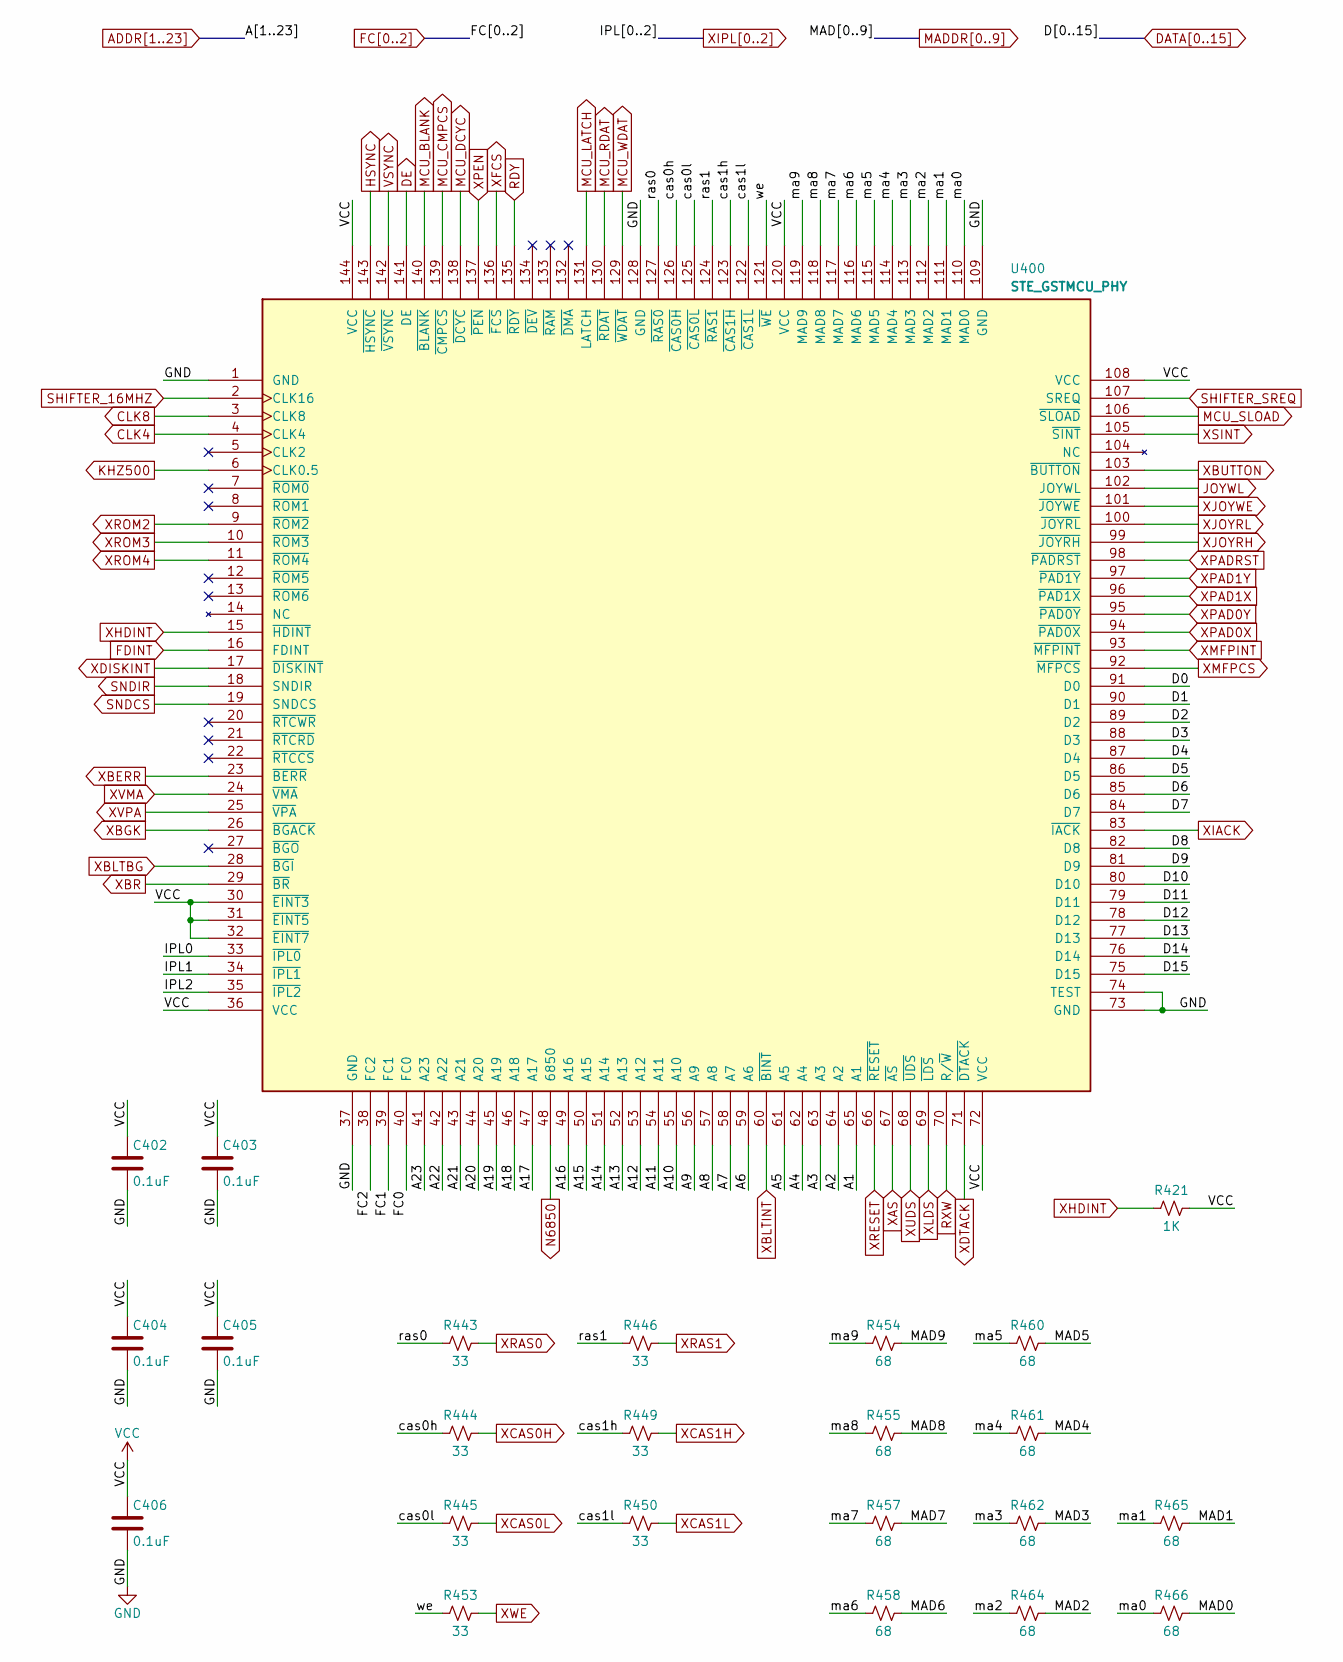
[picture p25: schematic subsheet_400.kicad_sch]

Parts:
C402, C403, C404, C405, C406: 0.1uF; Passive_THT_capacitor_mlcc_W2.54mm_L7.62mm
R421: 1K; Passive_THT_resistor_W2.54mm_L12.70mm
R443, R444, R445, R446, R449, R450, R453: 33; Passive_THT_resistor_W2.54mm_L12.70mm
R454, R455, R457, R458, R460, R461, R462, R464, R465, R466: 68; Passive_THT_resistor_W2.54mm_L12.70mm
U400: STE_GSTMCU_PHY; PQFP-144_28x28mm_P0.65mm

Connections:
A1: U400.65 (A1)
A2: U400.64 (A2)
A3: U400.63 (A3)
A4: U400.62 (A4)
A5: U400.61 (A5)
A6: U400.59 (A6)
A7: U400.58 (A7)
A8: U400.57 (A8)
A9: U400.56 (A9)
A10: U400.55 (A10)
A11: U400.54 (A11)
A12: U400.53 (A12)
A13: U400.52 (A13)
A14: U400.51 (A14)
A15: U400.50 (A15)
A16: U400.49 (A16)
A17: U400.47 (A17)
A18: U400.46 (A18)
A19: U400.45 (A19)
A20: U400.44 (A20)
A21: U400.43 (A21)
A22: U400.42 (A22)
A23: U400.41 (A23)
CLK4: U400.4 (CLK4)
CLK8: U400.3 (CLK8)
D0: U400.91 (D0)
D1: U400.90 (D1)
D2: U400.89 (D2)
D3: U400.88 (D3)
D4: U400.87 (D4)
D5: U400.86 (D5)
D6: U400.85 (D6)
D7: U400.84 (D7)
D8: U400.82 (D8)
D9: U400.81 (D9)
D10: U400.80 (D10)
D11: U400.79 (D11)
D12: U400.78 (D12)
D13: U400.77 (D13)
D14: U400.76 (D14)
D15: U400.75 (D15)
DE: U400.141 (DE)
FC0: U400.40 (FC0)
FC1: U400.39 (FC1)
FC2: U400.38 (FC2)
FDINT: U400.16 (FDINT)
GND: C402.2, C403.2, C404.2, C405.2, C406.2, U400.1 (GND), U400.37 (GND), U400.73 (GND), U400.74 (TEST), U400.109 (GND), U400.128 (GND)
HSYNC: U400.143 (~HSYNC)
IPL0: U400.33 (~IPL0)
IPL1: U400.34 (~IPL1)
IPL2: U400.35 (~IPL2)
JOYWL: U400.102 (JOYWL)
KHZ500: U400.6 (CLK0.5)
MAD0: R466.1
MAD1: R465.1
MAD2: R464.1
MAD3: R462.1
MAD4: R461.1
MAD5: R460.1
MAD6: R458.1
MAD7: R457.1
MAD8: R455.1
MAD9: R454.1
MCU_BLANK: U400.140 (~BLANK)
MCU_CMPCS: U400.139 (~CMPCS)
MCU_DCYC: U400.138 (~DCYC)
MCU_LATCH: U400.131 (LATCH)
MCU_RDAT: U400.130 (~RDAT)
MCU_SLOAD: U400.106 (~SLOAD)
MCU_WDAT: U400.129 (~WDAT)
N6850: U400.48 (6850)
RDY: U400.135 (~RDY)
RXW: U400.70 (R/~W)
SHIFTER_16MHZ: U400.2 (CLK16)
SHIFTER_SREQ: U400.107 (SREQ)
SNDCS: U400.19 (SNDCS)
SNDIR: U400.18 (SNDIR)
VCC: C402.1, C403.1, C404.1, C405.1, C406.1, R421.1, U400.30 (~EINT3), U400.31 (~EINT5), U400.32 (~EINT7), U400.36 (VCC), U400.72 (VCC), U400.108 (VCC), U400.120 (VCC), U400.144 (VCC)
VSYNC: U400.142 (~VSYNC)
XAS: U400.67 (~AS)
XBERR: U400.23 (~BERR)
XBGK: U400.26 (~BGACK)
XBLTBG: U400.28 (~BGI)
XBLTINT: U400.60 (~BINT)
XBR: U400.29 (~BR)
XBUTTON: U400.103 (~BUTTON)
XCAS0H: R444.1
XCAS0L: R445.1
XCAS1H: R449.1
XCAS1L: R450.1
XDISKINT: U400.17 (~DISKINT)
XDTACK: U400.71 (~DTACK)
XFCS: U400.136 (~FCS)
XHDINT: R421.2, U400.15 (~HDINT)
XIACK: U400.83 (~IACK)
XJOYRH: U400.99 (~JOYRH)
XJOYRL: U400.100 (~JOYRL)
XJOYWE: U400.101 (~JOYWE)
XLDS: U400.69 (~LDS)
XMFPCS: U400.92 (~MFPCS)
XMFPINT: U400.93 (~MFPINT)
XPAD0X: U400.94 (~PAD0X)
XPAD0Y: U400.95 (~PAD0Y)
XPAD1X: U400.96 (~PAD1X)
XPAD1Y: U400.97 (~PAD1Y)
XPADRST: U400.98 (~PADRST)
XPEN: U400.137 (~PEN)
XRAS0: R443.1
XRAS1: R446.1
XRESET: U400.66 (~RESET)
XROM2: U400.9 (~ROM2)
XROM3: U400.10 (~ROM3)
XROM4: U400.11 (~ROM4)
XSINT: U400.105 (~SINT)
XUDS: U400.68 (~UDS)
XVMA: U400.24 (~VMA)
XVPA: U400.25 (~VPA)
XWE: R453.1
cas0h: R444.2, U400.126 (~CAS0H)
cas0l: R445.2, U400.125 (~CAS0L)
cas1h: R449.2, U400.123 (~CAS1H)
cas1l: R450.2, U400.122 (~CAS1L)
ma0: R466.2, U400.110 (MAD0)
ma1: R465.2, U400.111 (MAD1)
ma2: R464.2, U400.112 (MAD2)
ma3: R462.2, U400.113 (MAD3)
ma4: R461.2, U400.114 (MAD4)
ma5: R460.2, U400.115 (MAD5)
ma6: R458.2, U400.116 (MAD6)
ma7: R457.2, U400.117 (MAD7)
ma8: R455.2, U400.118 (MAD8)
ma9: R454.2, U400.119 (MAD9)
ras0: R443.2, U400.127 (~RAS0)
ras1: R446.2, U400.124 (~RAS1)
we: R453.2, U400.121 (~WE)
