sporniket/kicad-conversions--atari-ste-motherboard--c300780-001/subsheet_401.kicad_sch

## KiCad design subsheet_401.kicad_sch (2025-09-03)

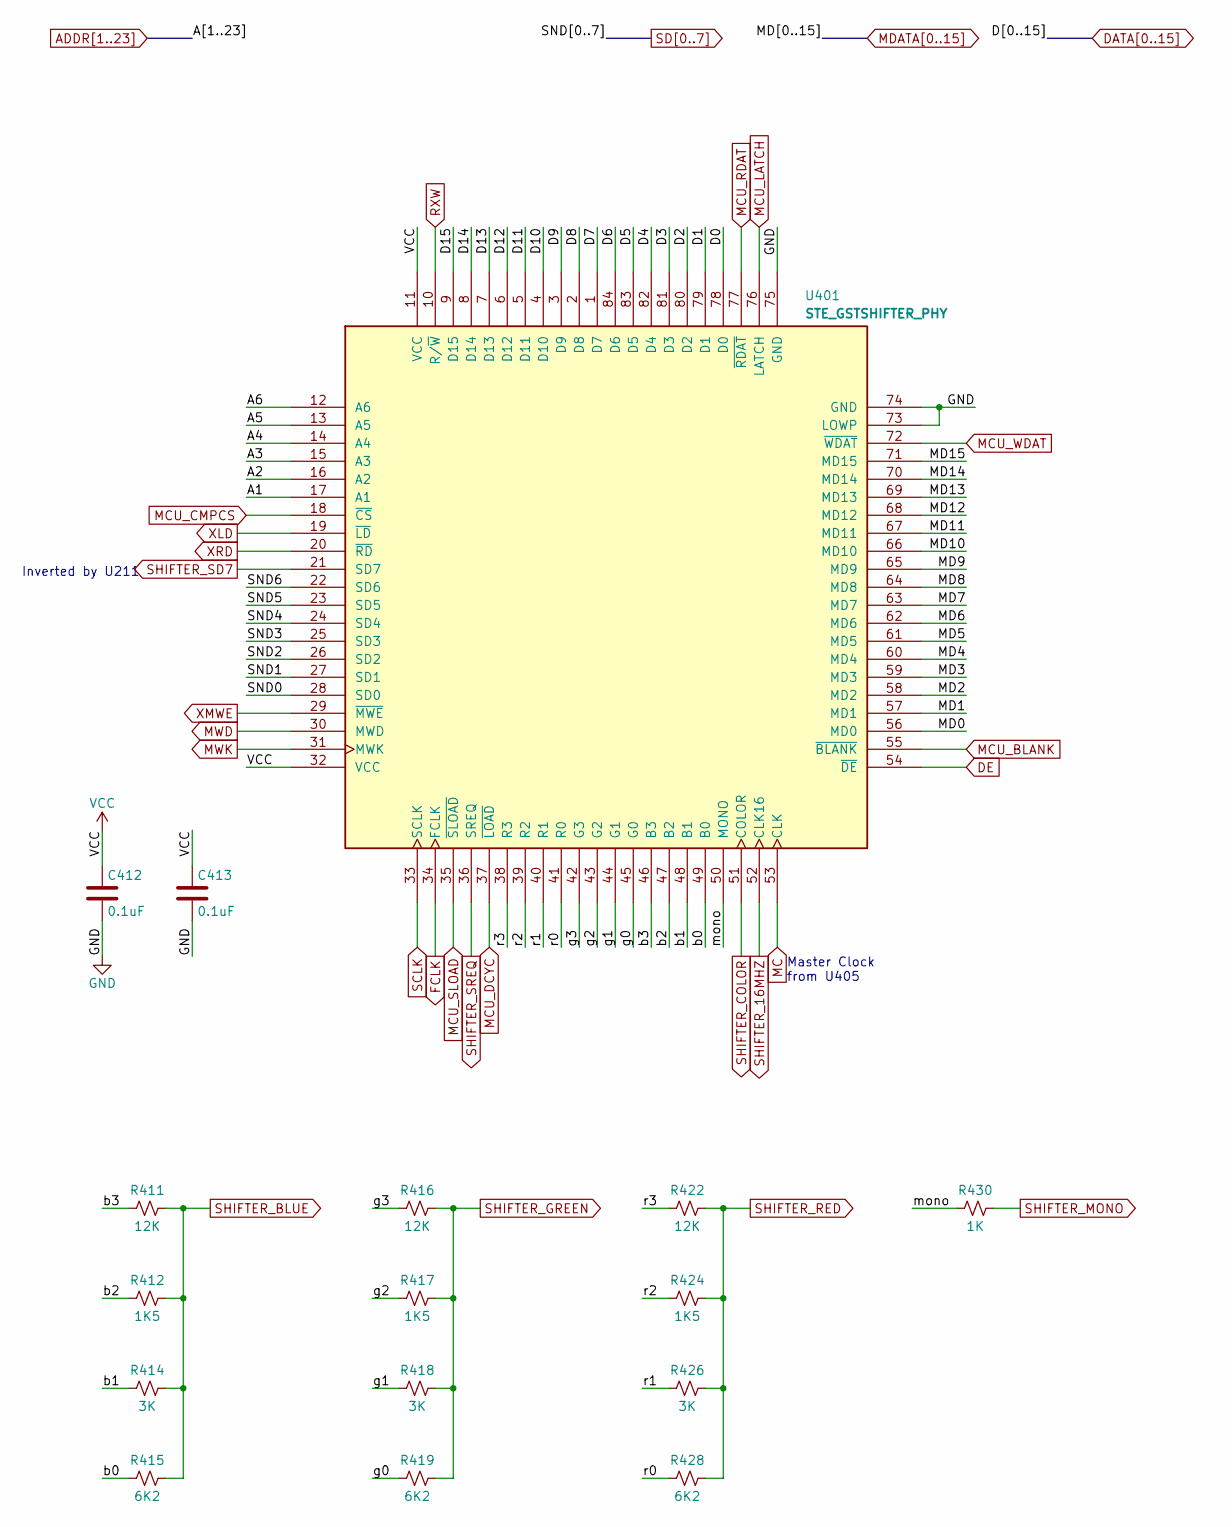
[picture p26: schematic subsheet_401.kicad_sch]

Parts:
C412, C413: 0.1uF; Passive_THT_capacitor_mlcc_W2.54mm_L7.62mm
R411, R416, R422: 12K; Passive_THT_resistor_W2.54mm_L12.70mm
R412, R417, R424: 1K5; Passive_THT_resistor_W2.54mm_L12.70mm
R414, R418, R426: 3K; Passive_THT_resistor_W2.54mm_L12.70mm
R415, R419, R428: 6K2; Passive_THT_resistor_W2.54mm_L12.70mm
R430: 1K; Passive_THT_resistor_W2.54mm_L12.70mm
U401: STE_GSTSHIFTER_PHY; PLCC-84_THT-Socket

Connections:
A1: U401.17 (A1)
A2: U401.16 (A2)
A3: U401.15 (A3)
A4: U401.14 (A4)
A5: U401.13 (A5)
A6: U401.12 (A6)
D0: U401.78 (D0)
D1: U401.79 (D1)
D2: U401.80 (D2)
D3: U401.81 (D3)
D4: U401.82 (D4)
D5: U401.83 (D5)
D6: U401.84 (D6)
D7: U401.1 (D7)
D8: U401.2 (D8)
D9: U401.3 (D9)
D10: U401.4 (D10)
D11: U401.5 (D11)
D12: U401.6 (D12)
D13: U401.7 (D13)
D14: U401.8 (D14)
D15: U401.9 (D15)
DE: U401.54 (~DE)
FCLK: U401.34 (FCLK)
GND: C412.2, C413.2, U401.73 (LOWP), U401.74 (GND), U401.75 (GND)
MC: U401.53 (CLK)
MCU_BLANK: U401.55 (~BLANK)
MCU_CMPCS: U401.18 (~CS)
MCU_DCYC: U401.37 (~LOAD)
MCU_LATCH: U401.76 (LATCH)
MCU_RDAT: U401.77 (~RDAT)
MCU_SLOAD: U401.35 (~SLOAD)
MCU_WDAT: U401.72 (~WDAT)
MD0: U401.56 (MD0)
MD1: U401.57 (MD1)
MD2: U401.58 (MD2)
MD3: U401.59 (MD3)
MD4: U401.60 (MD4)
MD5: U401.61 (MD5)
MD6: U401.62 (MD6)
MD7: U401.63 (MD7)
MD8: U401.64 (MD8)
MD9: U401.65 (MD9)
MD10: U401.66 (MD10)
MD11: U401.67 (MD11)
MD12: U401.68 (MD12)
MD13: U401.69 (MD13)
MD14: U401.70 (MD14)
MD15: U401.71 (MD15)
MWD: U401.30 (MWD)
MWK: U401.31 (MWK)
RXW: U401.10 (R/~W)
SCLK: U401.33 (SCLK)
SHIFTER_16MHZ: U401.52 (CLK16)
SHIFTER_BLUE: R411.1, R412.1, R414.1, R415.1
SHIFTER_COLOR: U401.51 (COLOR)
SHIFTER_GREEN: R416.1, R417.1, R418.1, R419.1
SHIFTER_MONO: R430.1
SHIFTER_RED: R422.1, R424.1, R426.1, R428.1
SHIFTER_SD7: U401.21 (SD7)
SHIFTER_SREQ: U401.36 (SREQ)
SND0: U401.28 (SD0)
SND1: U401.27 (SD1)
SND2: U401.26 (SD2)
SND3: U401.25 (SD3)
SND4: U401.24 (SD4)
SND5: U401.23 (SD5)
SND6: U401.22 (SD6)
VCC: C412.1, C413.1, U401.11 (VCC), U401.32 (VCC)
XLD: U401.19 (~LD)
XMWE: U401.29 (~MWE)
XRD: U401.20 (~RD)
b0: R415.2, U401.49 (B0)
b1: R414.2, U401.48 (B1)
b2: R412.2, U401.47 (B2)
b3: R411.2, U401.46 (B3)
g0: R419.2, U401.45 (G0)
g1: R418.2, U401.44 (G1)
g2: R417.2, U401.43 (G2)
g3: R416.2, U401.42 (G3)
mono: R430.2, U401.50 (MONO)
r0: R428.2, U401.41 (R0)
r1: R426.2, U401.40 (R1)
r2: R424.2, U401.39 (R2)
r3: R422.2, U401.38 (R3)

Notes on the sheet:
Master Clock from U405
Inverted by U211
