sporniket/kicad-conversions--atari-ste-motherboard--c300780-001/subsheet_402.kicad_sch

## KiCad design subsheet_402.kicad_sch (2025-09-03)

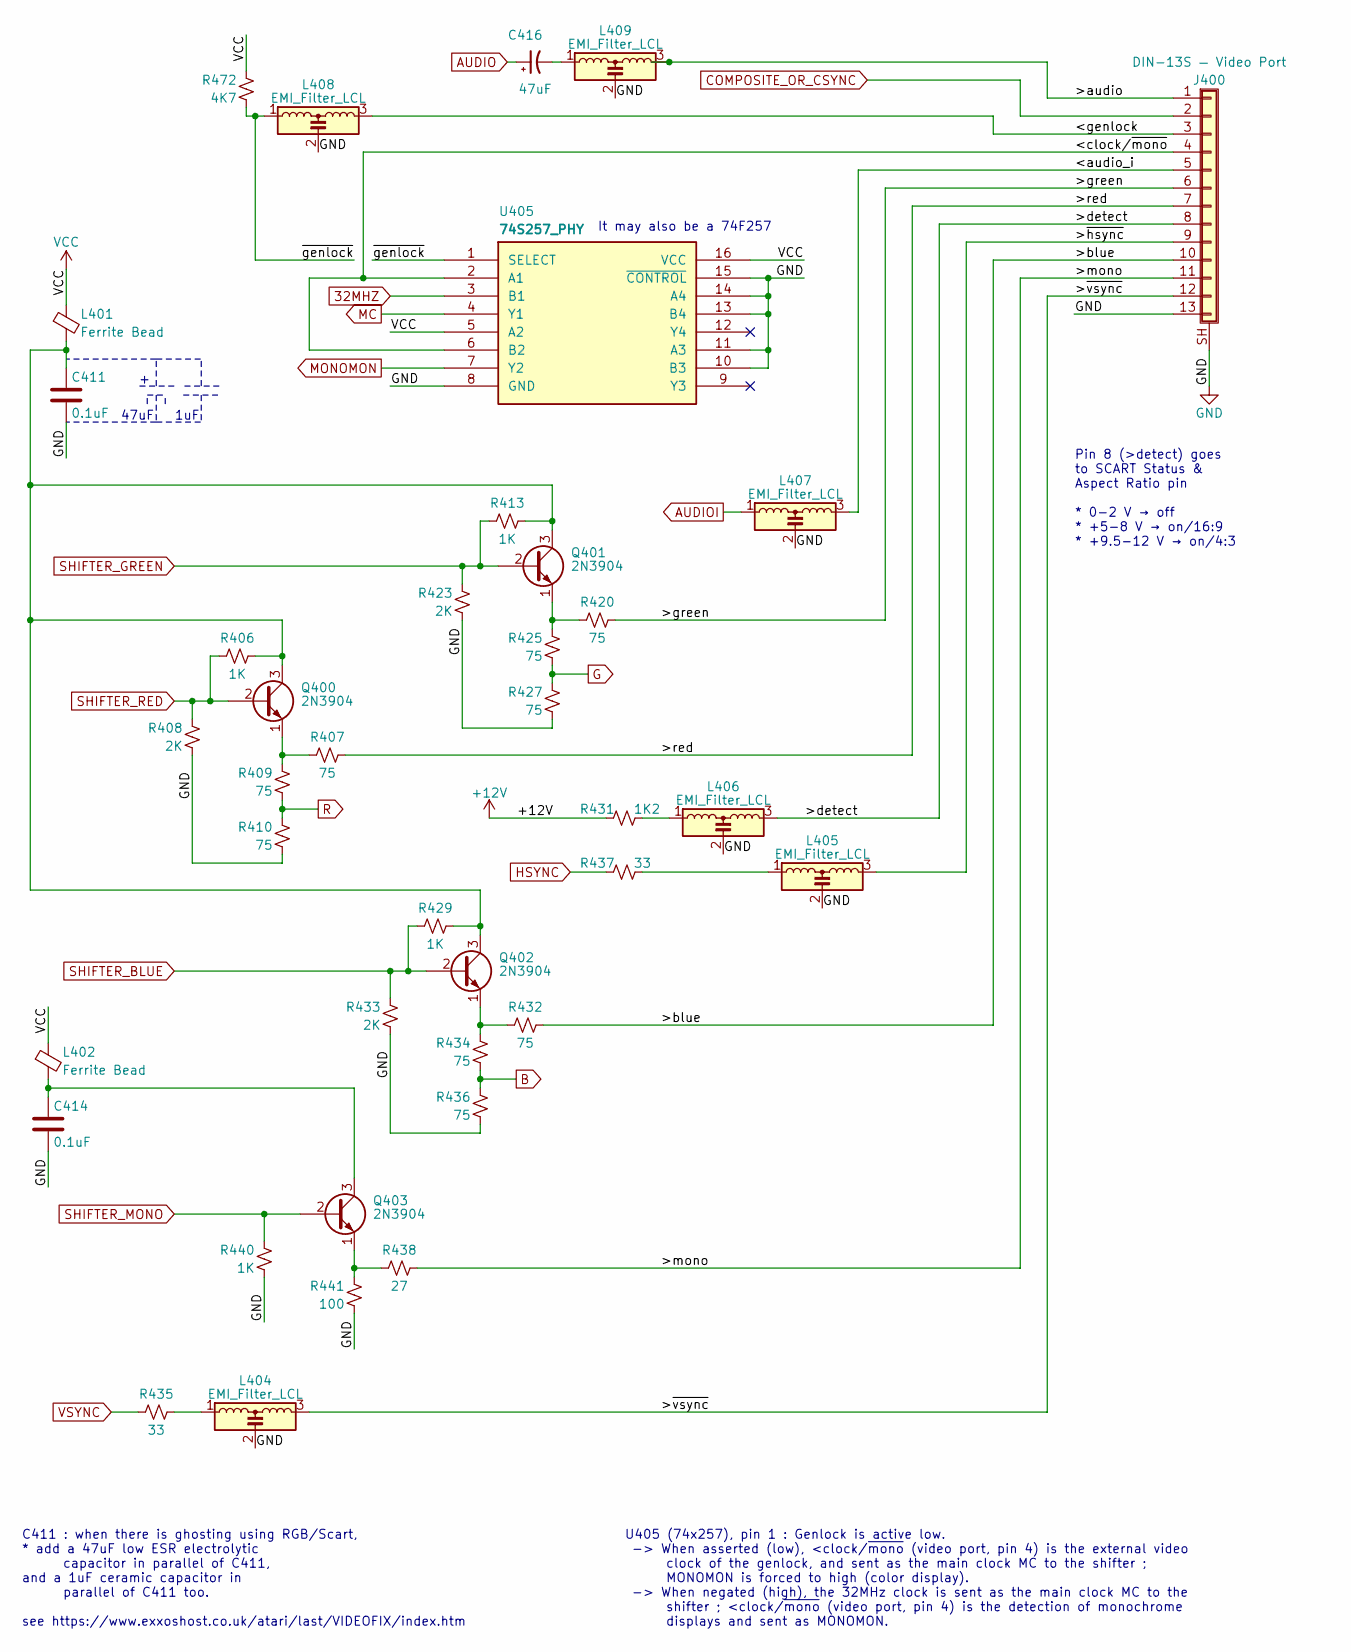
[picture p27: schematic subsheet_402.kicad_sch]

Parts:
C411: 0.1uF; Passive_THT_capacitor_mlcc_W2.54mm_L10.16mm
C414: 0.1uF; Passive_THT_capacitor_mlcc_W2.54mm_L7.62mm
C416: 47uF; Passive_THT_capacitor_polarized_rad_D5.08mm_P2.54mm_H12.70mm
J400: DIN-13S — Video Port; socket-din-13
L401, L402: Ferrite Bead; Passive_THT_ferrite_bead_W3.81mm_L15.24mm
L404, L405, L406, L407, L408, L409: EMI_Filter_LCL; Passive_THT_EMI_filter_W5.08mm_L7.62mm
Q400, Q401, Q402, Q403: 2N3904; TO-92_Inline_Wide
R406, R413, R429, R440: 1K; Passive_THT_resistor_W2.54mm_L12.70mm
R407, R409, R410, R420, R425, R427, R432, R434, R436: 75; Passive_THT_resistor_W2.54mm_L12.70mm
R408, R423, R433: 2K; Passive_THT_resistor_W2.54mm_L12.70mm
R431: 1K2; Passive_THT_resistor_W2.54mm_L12.70mm
R435, R437: 33; Passive_THT_resistor_W2.54mm_L12.70mm
R438: 27; Passive_THT_resistor_W2.54mm_L12.70mm
R441: 100; Passive_THT_resistor_W2.54mm_L12.70mm
R472: 4K7; Passive_THT_resistor_W2.54mm_L12.70mm
U405: 74S257_PHY; DIP-16_W7.62mm_LongPads

Connections:
32MHZ: U405.3 (B1)
+12V: R431.2
<audio_i: J400.5, L407.3
<clock/~mono: J400.4, U405.2 (A1), U405.6 (B2)
<genlock: J400.3, L408.3
>audio: J400.1, L409.3
>blue: J400.10, R432.1
>detect: J400.8, L406.3
>green: J400.6, R420.1
>mono: J400.11, R438.1
>red: J400.7, R407.1
>~hsync: J400.9, L405.3
>~vsync: J400.12, L404.3
AUDIO: C416.1
AUDIOI: L407.1
B: R434.2, R436.1
COMPOSITE_OR_CSYNC: J400.2
G: R425.2, R427.1
GND: C411.2, C414.2, J400.13, J400.SH (Shield), L404.2, L405.2, L406.2, L407.2, L408.2, L409.2, R408.2, R410.2, R423.2, R427.2, R433.2, R436.2, R440.2, R441.2, U405.8 (GND), U405.10 (B3), U405.11 (A3), U405.13 (B4), U405.14 (A4), U405.15 (~CONTROL)
HSYNC: R437.2
MC: U405.4 (Y1)
MONOMON: U405.7 (Y2)
unnamed: C411.1, L401.2, Q400.3 (C), Q401.3 (C), Q402.3 (C), R406.1, R413.1, R429.1
unnamed: C414.1, L402.2, Q403.3 (C)
unnamed: C416.2, L409.1
unnamed: L404.1, R435.1
unnamed: L405.1, R437.1
unnamed: L406.1, R431.1
unnamed: Q400.1 (E), R407.2, R409.1
unnamed: Q401.1 (E), R420.2, R425.1
unnamed: Q402.1 (E), R432.2, R434.1
unnamed: Q403.1 (E), R438.2, R441.1
R: R409.2, R410.1
SHIFTER_BLUE: Q402.2 (B), R429.2, R433.1
SHIFTER_GREEN: Q401.2 (B), R413.2, R423.1
SHIFTER_MONO: Q403.2 (B), R440.1
SHIFTER_RED: Q400.2 (B), R406.2, R408.1
VCC: L401.1, L402.1, R472.1, U405.5 (A2), U405.16 (VCC)
VSYNC: R435.2
~genlock: L408.1, R472.2, U405.1 (SELECT)

Notes on the sheet:
It may also be a 74F257
C411 : when there is ghosting using RGB/Scart, * add a 47uF low ESR electrolytic capacitor in parallel of C411, and a 1uF ceramic capacitor in parallel of C411 too. see https://www.exxoshost.co.uk/atari/last/VIDEOFIX/index.htm
U405 (74x257), pin 1 : Genlock is active low. -> When asserted (low), <clock/~{mono} (video port, pin 4) is the external video clock of the genlock, and sent as the main clock MC to the shifter ; MONOMON is forced to high (color display). -> When negated (high), the 32MHz clock is sent as the main 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
Pin 8 (>detect) goes to SCART Status & Aspect Ratio pin * 0-2 V → off * +5-8 V → on/16:9 * +9.5-12 V → on/4:3
1uF
47uF
