sporniket/kicad-conversions--atari-ste-motherboard--c300780-001/subsheet_403.kicad_sch

## KiCad design subsheet_403.kicad_sch (2025-09-03)

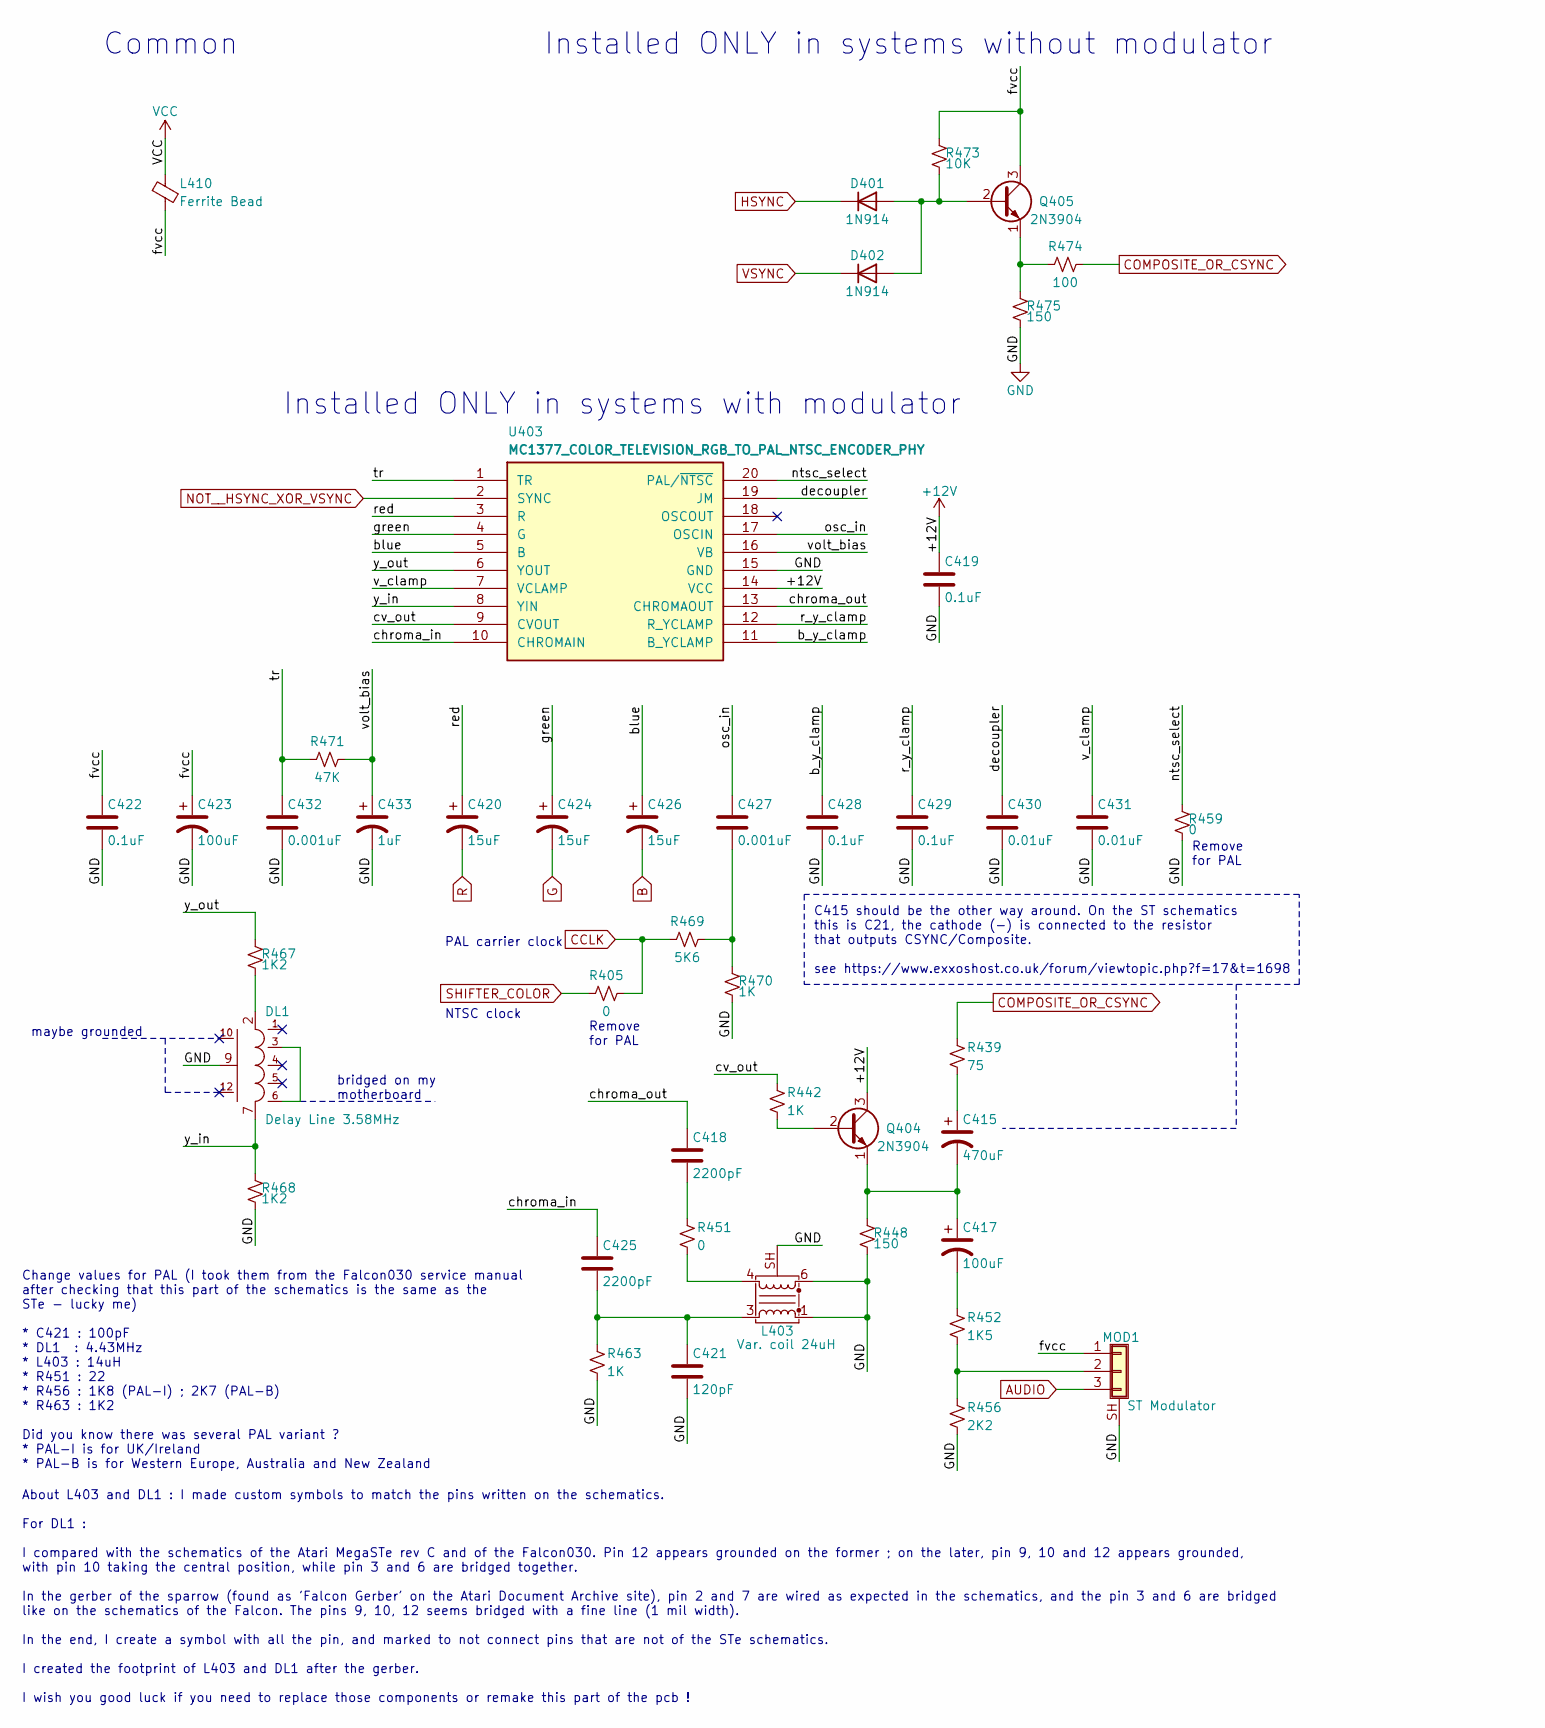
[picture p28: schematic subsheet_403.kicad_sch]

Parts:
C415: 470uF; Passive_THT_capacitor_polarized_rad_D10.16mm_P5.08mm_H22.86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
C417, C423: 100uF; Passive_THT_capacitor_polarized_rad_D5.08mm_P2.54mm_H12.70mm
C418: 2200pF; Passive_THT_capacitor_W2.54mm_L10.16mm
C419, C422, C428, C429: 0.1uF; Passive_THT_capacitor_mlcc_W2.54mm_L7.62mm
C420, C424, C426: 15uF; CP_Radial_Tantal_D4.5mm_P2.50mm
C421: 120pF; Passive_THT_capacitor_W2.54mm_L10.16mm
C425: 2200pF; Passive_THT_capacitor_polarized_rad_D5.08mm_P2.54mm_H12.70mm
C427: 0.001uF; Passive_THT_capacitor_W2.54mm_L10.16mm
C430, C431: 0.01uF; Passive_THT_capacitor_W2.54mm_L10.16mm
C432: 0.001uF; Passive_THT_capacitor_ceramic_radial_W2.54mm_L10.16mm
C433: 1uF; Passive_THT_capacitor_polarized_rad_D5.08mm_P2.54mm_H12.70mm
D401, D402: 1N914; Passive_THT_diode_W2.54mm_L12.70mm
DL1: Delay Line 3.58MHz; Atari_ST_THT_Delay_Line
L403: Var. coil 24uH; Passive_THT_variable_Coil_Shielded_7x7mm_5_of_6pins
L410: Ferrite Bead; Passive_THT_ferrite_bead_W3.81mm_L15.24mm
MOD1: ST Modulator; PinHeader_1x03_P2.54mm_Vertical
Q404, Q405: 2N3904; TO-92_Inline_Wide
R405, R451, R459: 0; Passive_THT_resistor_W2.54mm_L12.70mm
R439: 75; Passive_THT_resistor_W2.54mm_L12.70mm
R442, R463, R470: 1K; Passive_THT_resistor_W2.54mm_L12.70mm
R448, R475: 150; Passive_THT_resistor_W2.54mm_L12.70mm
R452: 1K5; Passive_THT_resistor_W2.54mm_L12.70mm
R456: 2K2; Passive_THT_resistor_W2.54mm_L12.70mm
R467, R468: 1K2; Passive_THT_resistor_W2.54mm_L12.70mm
R469: 5K6; Passive_THT_resistor_W2.54mm_L12.70mm
R471: 47K; Passive_THT_resistor_W2.54mm_L12.70mm
R473: 10K; Passive_THT_resistor_W2.54mm_L12.70mm
R474: 100; Passive_THT_resistor_W2.54mm_L12.70mm
U403: MC1377_COLOR_TELEVISION_RGB_TO_PAL_NTSC_ENCODER_P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; DIP-20_W7.62mm_LongPads

Connections:
+12V: C419.1, Q404.3 (C), U403.14 (VCC)
AUDIO: MOD1.3
B: C426.2
CCLK: R405.1, R469.2
COMPOSITE_OR_CSYNC: R439.1, R474.1
G: C424.2
GND: C419.2, C421.2, C422.2, C423.2, C428.2, C429.2, C430.2, C431.2, C432.2, C433.2, DL1.9 (COMMUN), L403.1, L403.6, L403.SH (Shield), MOD1.SH (Shield), R448.2, R456.2, R459.2, R463.2, R468.2, R470.2, R475.2, U403.15 (GND)
HSYNC: D401.1 (K)
NOT__HSYNC_XOR_VSYNC: U403.2 (SYNC)
unnamed: C415.1, R439.2
unnamed: C415.2, C417.1, Q404.1 (E), R448.1
unnamed: C417.2, R452.1
unnamed: C418.2, R451.1
unnamed: C421.1, C425.2, L403.3, R463.1
unnamed: C427.2, R469.1, R470.1
unnamed: D401.2 (A), D402.2 (A), Q405.2 (B), R473.2
unnamed: DL1.2, R467.2
unnamed: DL1.3, DL1.6
unnamed: L403.4, R451.2
unnamed: MOD1.2, R452.2, R456.1
unnamed: Q404.2 (B), R442.2
unnamed: Q405.1 (E), R474.2, R475.1
R: C420.2
SHIFTER_COLOR: R405.2
VCC: L410.1
VSYNC: D402.1 (K)
b_y_clamp: C428.1, U403.11 (B_YCLAMP)
blue: C426.1, U403.5 (B)
chroma_in: C425.1, U403.10 (CHROMAIN)
chroma_out: C418.1, U403.13 (CHROMAOUT)
cv_out: R442.1, U403.9 (CVOUT)
decoupler: C430.1, U403.19 (JM)
fvcc: C422.1, C423.1, L410.2, MOD1.1, Q405.3 (C), R473.1
green: C424.1, U403.4 (G)
ntsc_select: R459.1, U403.20 (PAL/~NTSC)
osc_in: C427.1, U403.17 (OSCIN)
r_y_clamp: C429.1, U403.12 (R_YCLAMP)
red: C420.1, U403.3 (R)
tr: C432.1, R471.2, U403.1 (TR)
v_clamp: C431.1, U403.7 (VCLAMP)
volt_bias: C433.1, R471.1, U403.16 (VB)
y_in: DL1.7, R468.1, U403.8 (YIN)
y_out: R467.1, U403.6 (YOUT)

Notes on the sheet:
Remove for PAL
Common
PAL carrier clock
Installed ONLY in systems without modulator
maybe grounded
About L403 and DL1 : I made custom symbols to match the pins written on the schematics. For DL1 : I compared with the schematics of the Atari MegaSTe rev C and of the Falcon030. Pin 12 appears grounded on the former ; on the later, pin 9, 10 and 12 appears grounded, with pin 10 taking the central p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
C415 should be the other way around. On the ST schematics this is C21, the cathode (-) is connected to the resistor that outputs CSYNC/Composite. see https://www.exxoshost.co.uk/forum/viewtopic.php?f=17&t=1698
Change values for PAL (I took them from the Falcon030 service manual after checking that this part of the schematics is the same as the STe - lucky me) * C421 : 100pF * DL1 : 4.43MHz * L403 : 14uH * R451 : 22 * R456 : 1K8 (PAL-I) ; 2K7 (PAL-B) * R463 : 1K2 Did you know there was several PAL variant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
NTSC clock
Installed ONLY in systems with modulator
bridged on my motherboard
