sporniket/kicad-conversions--atari-ste-motherboard--c300780-001/subsheet_500.kicad_sch

## KiCad design subsheet_500.kicad_sch (2025-09-03)

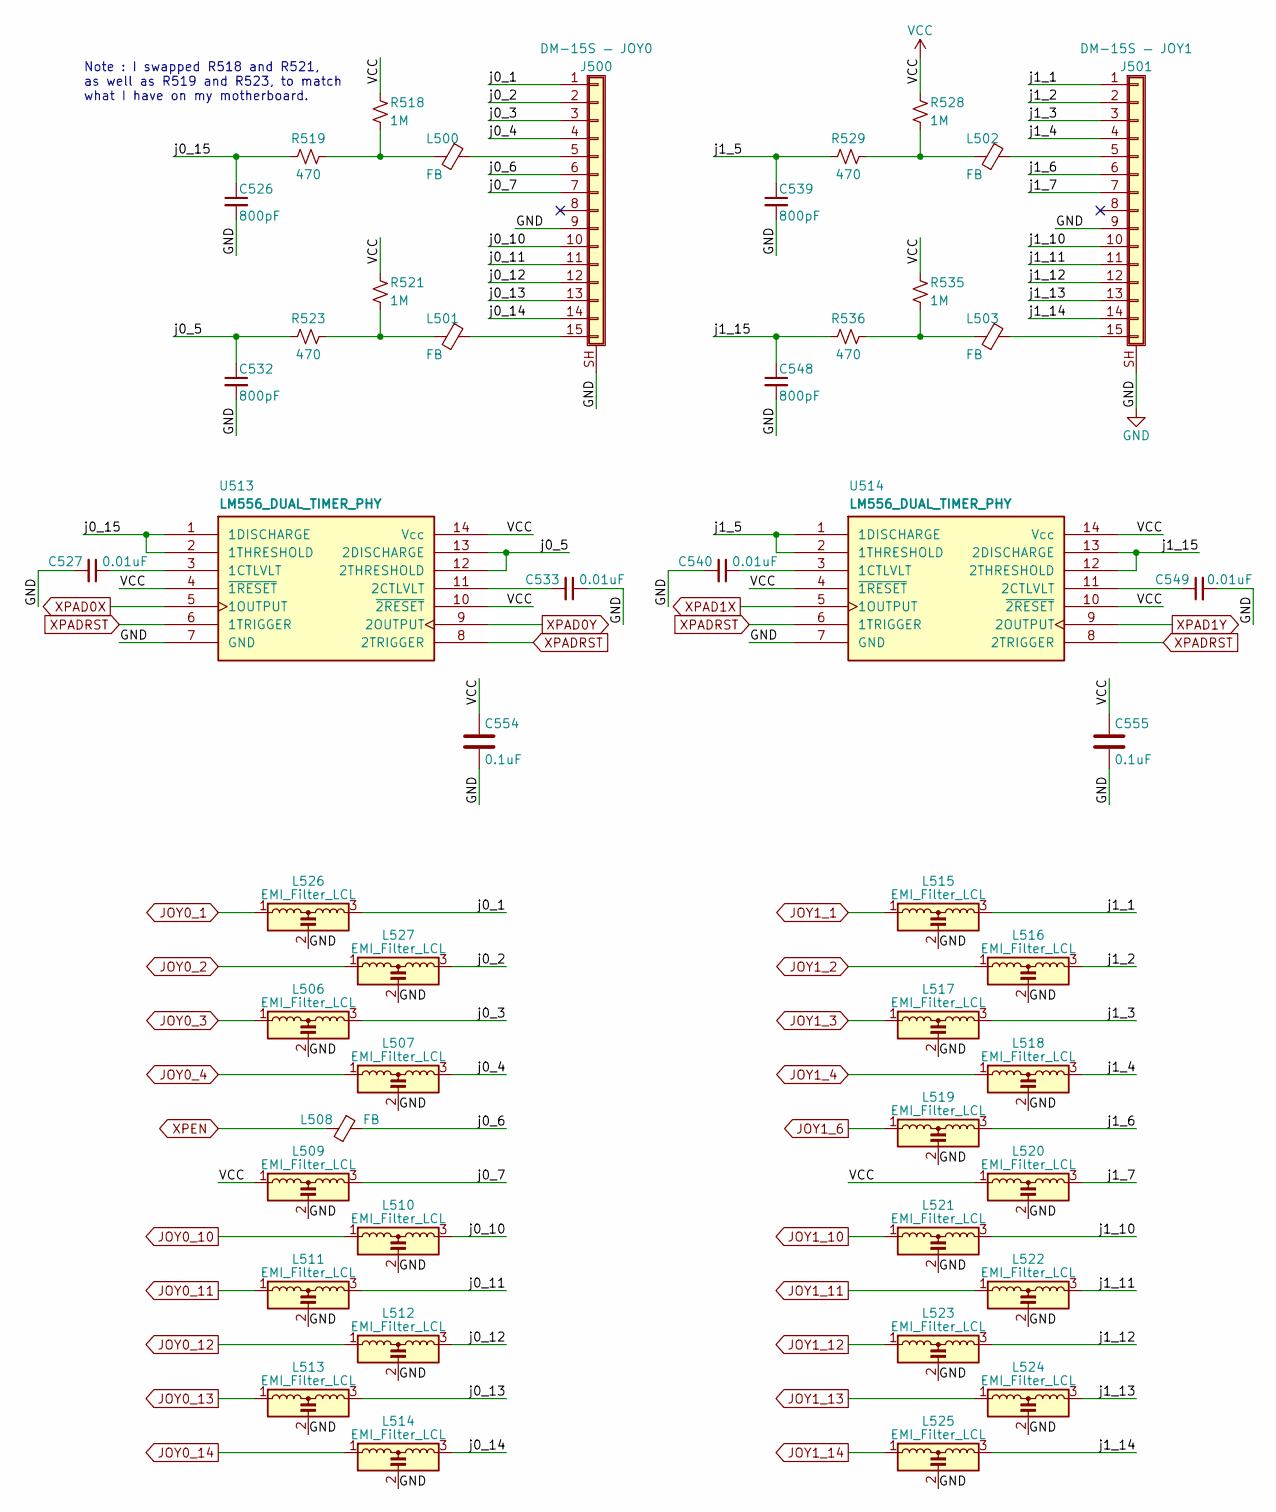
[picture p29: schematic subsheet_500.kicad_sch]

Parts:
C526, C532, C539, C548: 800pF; Passive_THT_capacitor_ceramic_radial_W5.08mm_L6.35mm_X11.43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
C527, C533, C540, C549: 0.01uF; Passive_THT_capacitor_W2.54mm_L10.16mm
C554, C555: 0.1uF; Passive_THT_capacitor_mlcc_W2.54mm_L7.62mm
J500: DM-15S — JOY0; DSUB-15-HD_Female_Horizontal_P2.29x1.98mm_EdgePinOffset8.35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
J501: DM-15S — JOY1; DSUB-15-HD_Female_Horizontal_P2.29x1.98mm_EdgePinOffset8.35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
L500, L501, L502, L503, L508: FB; Passive_THT_ferrite_bead_W3.81mm_L15.24mm
L506, L507, L509, L510, L511, L512, L513, L514, L515, L516, L517, L518, L519, L520, L521, L522, L523, L524, L525, L526, L527: EMI_Filter_LCL; Passive_THT_EMI_filter_W5.08mm_L7.62mm
R518, R521, R528, R535: 1M; Passive_THT_resistor_W2.54mm_L12.70mm
R519, R523, R529, R536: 470; Passive_THT_resistor_W2.54mm_L12.70mm
U513, U514: LM556_DUAL_TIMER_PHY; DIP-14_W7.62mm_LongPads

Connections:
GND: C526.2, C527.2, C532.2, C533.1, C539.2, C540.2, C548.2, C549.2, C554.2, C555.2, J500.9, J500.SH (Shield), J501.9, J501.SH (Shield), L506.2, L507.2, L509.2, L510.2, L511.2, L512.2, L513.2, L514.2, L515.2, L516.2, L517.2, L518.2, L519.2, L520.2, L521.2, L522.2, L523.2, L524.2, L525.2, L526.2, L527.2, U513.7 (GND), U514.7 (GND)
JOY0_1: L526.1
JOY0_2: L527.1
JOY0_3: L506.1
JOY0_4: L507.1
JOY0_10: L510.1
JOY0_11: L511.1
JOY0_12: L512.1
JOY0_13: L513.1
JOY0_14: L514.1
JOY1_1: L515.1
JOY1_2: L516.1
JOY1_3: L517.1
JOY1_4: L518.1
JOY1_6: L519.1
JOY1_10: L521.1
JOY1_11: L522.1
JOY1_12: L523.1
JOY1_13: L524.1
JOY1_14: L525.1
unnamed: C527.1, U513.3 (1CTLVLT)
unnamed: C533.2, U513.11 (2CTLVLT)
unnamed: C540.1, U514.3 (1CTLVLT)
unnamed: C549.1, U514.11 (2CTLVLT)
unnamed: J500.5, L500.1
unnamed: J500.15, L501.1
unnamed: J501.5, L502.1
unnamed: J501.15, L503.1
unnamed: L500.2, R518.2, R519.1
unnamed: L501.2, R521.2, R523.1
unnamed: L502.2, R528.2, R529.1
unnamed: L503.2, R535.2, R536.1
VCC: C554.1, C555.1, L509.1, L520.1, R518.1, R521.1, R528.1, R535.1, U513.4 (~1RESET), U513.10 (~2RESET), U513.14 (Vcc), U514.4 (~1RESET), U514.10 (~2RESET), U514.14 (Vcc)
XPAD0X: U513.5 (1OUTPUT)
XPAD0Y: U513.9 (2OUTPUT)
XPAD1X: U514.5 (1OUTPUT)
XPAD1Y: U514.9 (2OUTPUT)
XPADRST: U513.6 (1TRIGGER), U513.8 (2TRIGGER), U514.6 (1TRIGGER), U514.8 (2TRIGGER)
XPEN: L508.2
j0_1: J500.1, L526.3
j0_2: J500.2, L527.3
j0_3: J500.3, L506.3
j0_4: J500.4, L507.3
j0_5: C532.1, R523.2, U513.12 (2THRESHOLD), U513.13 (2DISCHARGE)
j0_6: J500.6, L508.1
j0_7: J500.7, L509.3
j0_10: J500.10, L510.3
j0_11: J500.11, L511.3
j0_12: J500.12, L512.3
j0_13: J500.13, L513.3
j0_14: J500.14, L514.3
j0_15: C526.1, R519.2, U513.1 (1DISCHARGE), U513.2 (1THRESHOLD)
j1_1: J501.1, L515.3
j1_2: J501.2, L516.3
j1_3: J501.3, L517.3
j1_4: J501.4, L518.3
j1_5: C539.1, R529.2, U514.1 (1DISCHARGE), U514.2 (1THRESHOLD)
j1_6: J501.6, L519.3
j1_7: J501.7, L520.3
j1_10: J501.10, L521.3
j1_11: J501.11, L522.3
j1_12: J501.12, L523.3
j1_13: J501.13, L524.3
j1_14: J501.14, L525.3
j1_15: C548.1, R536.2, U514.12 (2THRESHOLD), U514.13 (2DISCHARGE)

Notes on the sheet:
Note : I swapped R518 and R521, as well as R519 and R523, to match what I have on my motherboard.
