sporniket/kicad-conversions--atari-ste-motherboard--c300780-001/subsheet_501.kicad_sch

## KiCad design subsheet_501.kicad_sch (2025-09-03)

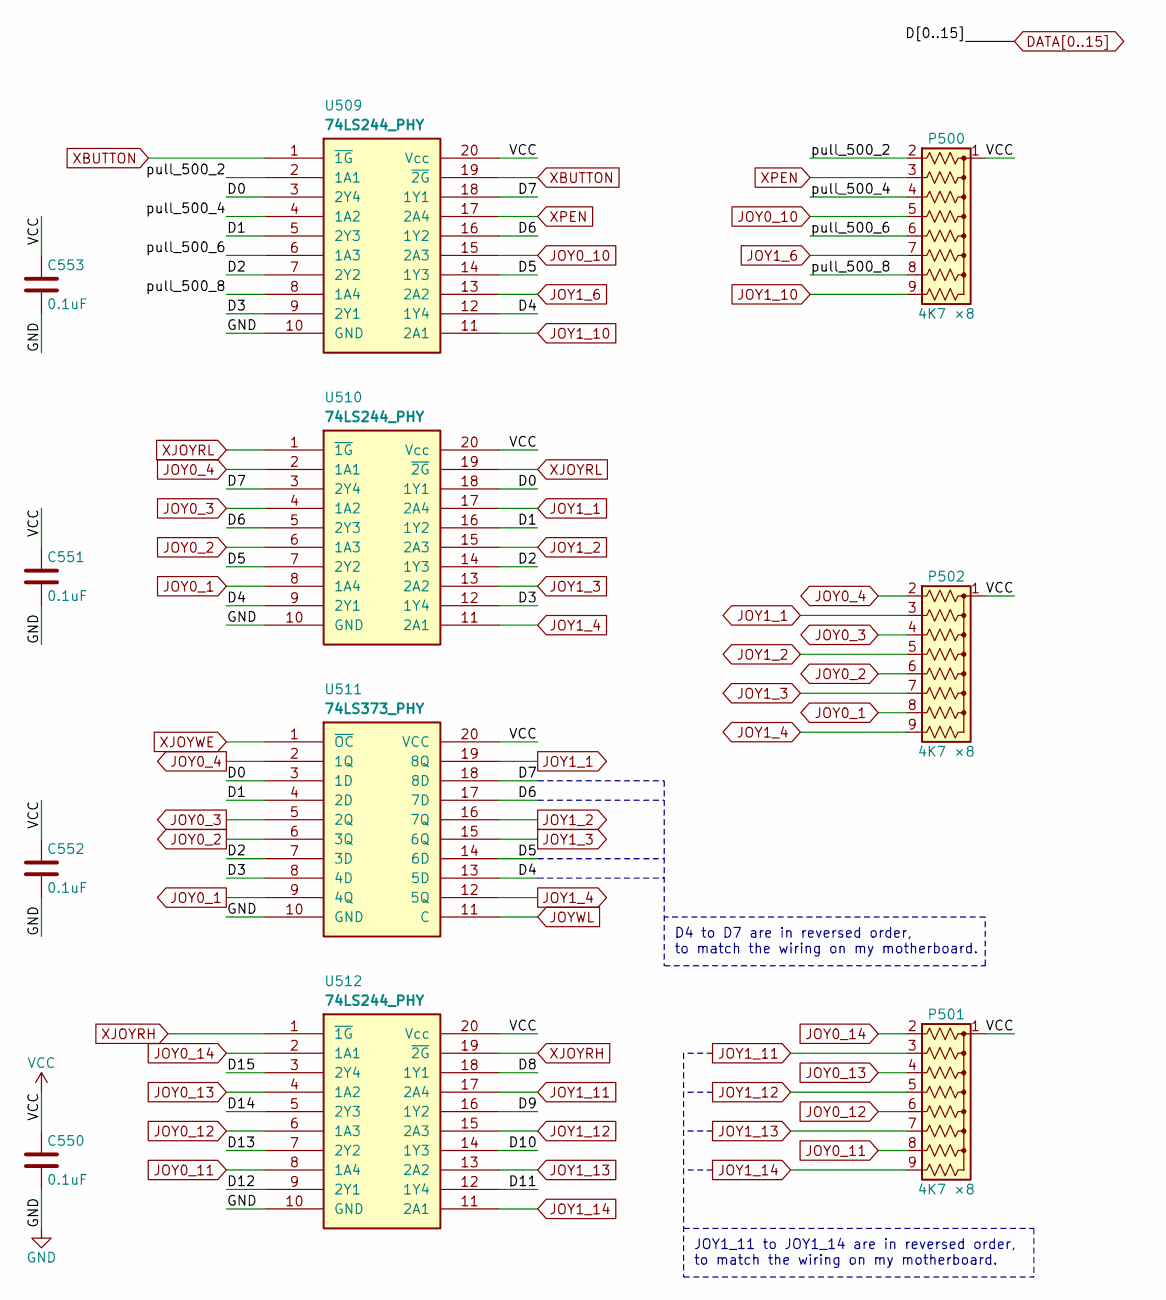
[picture p30: schematic subsheet_501.kicad_sch]

Parts:
C550, C551, C552, C553: 0.1uF; Passive_THT_capacitor_mlcc_W2.54mm_L7.62mm
P500, P501, P502: 4K7 ×8; R_Array_SIP9
U509, U510, U512: 74LS244_PHY; DIP-20_W7.62mm_LongPads
U511: 74LS373_PHY; DIP-20_W7.62mm_LongPads

Connections:
D0: U509.3 (2Y4), U510.18 (1Y1), U511.3 (1D)
D1: U509.5 (2Y3), U510.16 (1Y2), U511.4 (2D)
D2: U509.7 (2Y2), U510.14 (1Y3), U511.7 (3D)
D3: U509.9 (2Y1), U510.12 (1Y4), U511.8 (4D)
D4: U509.12 (1Y4), U510.9 (2Y1), U511.13 (5D)
D5: U509.14 (1Y3), U510.7 (2Y2), U511.14 (6D)
D6: U509.16 (1Y2), U510.5 (2Y3), U511.17 (7D)
D7: U509.18 (1Y1), U510.3 (2Y4), U511.18 (8D)
D8: U512.18 (1Y1)
D9: U512.16 (1Y2)
D10: U512.14 (1Y3)
D11: U512.12 (1Y4)
D12: U512.9 (2Y1)
D13: U512.7 (2Y2)
D14: U512.5 (2Y3)
D15: U512.3 (2Y4)
GND: C550.2, C551.2, C552.2, C553.2, U509.10 (GND), U510.10 (GND), U511.10 (GND), U512.10 (GND)
JOY0_1: P502.8 (R7), U510.8 (1A4), U511.9 (4Q)
JOY0_2: P502.6 (R5), U510.6 (1A3), U511.6 (3Q)
JOY0_3: P502.4 (R3), U510.4 (1A2), U511.5 (2Q)
JOY0_4: P502.2 (R1), U510.2 (1A1), U511.2 (1Q)
JOY0_10: P500.5 (R4), U509.15 (2A3)
JOY0_11: P501.8 (R7), U512.8 (1A4)
JOY0_12: P501.6 (R5), U512.6 (1A3)
JOY0_13: P501.4 (R3), U512.4 (1A2)
JOY0_14: P501.2 (R1), U512.2 (1A1)
JOY1_1: P502.3 (R2), U510.17 (2A4), U511.19 (8Q)
JOY1_2: P502.5 (R4), U510.15 (2A3), U511.16 (7Q)
JOY1_3: P502.7 (R6), U510.13 (2A2), U511.15 (6Q)
JOY1_4: P502.9 (R8), U510.11 (2A1), U511.12 (5Q)
JOY1_6: P500.7 (R6), U509.13 (2A2)
JOY1_10: P500.9 (R8), U509.11 (2A1)
JOY1_11: P501.3 (R2), U512.17 (2A4)
JOY1_12: P501.5 (R4), U512.15 (2A3)
JOY1_13: P501.7 (R6), U512.13 (2A2)
JOY1_14: P501.9 (R8), U512.11 (2A1)
JOYWL: U511.11 (C)
VCC: C550.1, C551.1, C552.1, C553.1, P500.1 (common), P501.1 (common), P502.1 (common), U509.20 (Vcc), U510.20 (Vcc), U511.20 (VCC), U512.20 (Vcc)
XBUTTON: U509.1 (~1G), U509.19 (~2G)
XJOYRH: U512.1 (~1G), U512.19 (~2G)
XJOYRL: U510.1 (~1G), U510.19 (~2G)
XJOYWE: U511.1 (~OC)
XPEN: P500.3 (R2), U509.17 (2A4)
pull_500_2: P500.2 (R1), U509.2 (1A1)
pull_500_4: P500.4 (R3), U509.4 (1A2)
pull_500_6: P500.6 (R5), U509.6 (1A3)
pull_500_8: P500.8 (R7), U509.8 (1A4)

Notes on the sheet:
JOY1_11 to JOY1_14 are in reversed order, to match the wiring on my motherboard.
D4 to D7 are in reversed order, to match the wiring on my motherboard.
