sporniket/kicad-conversions--atari-ste-motherboard--c300780-001/subsheet_502.kicad_sch

## KiCad design subsheet_502.kicad_sch (2025-09-03)

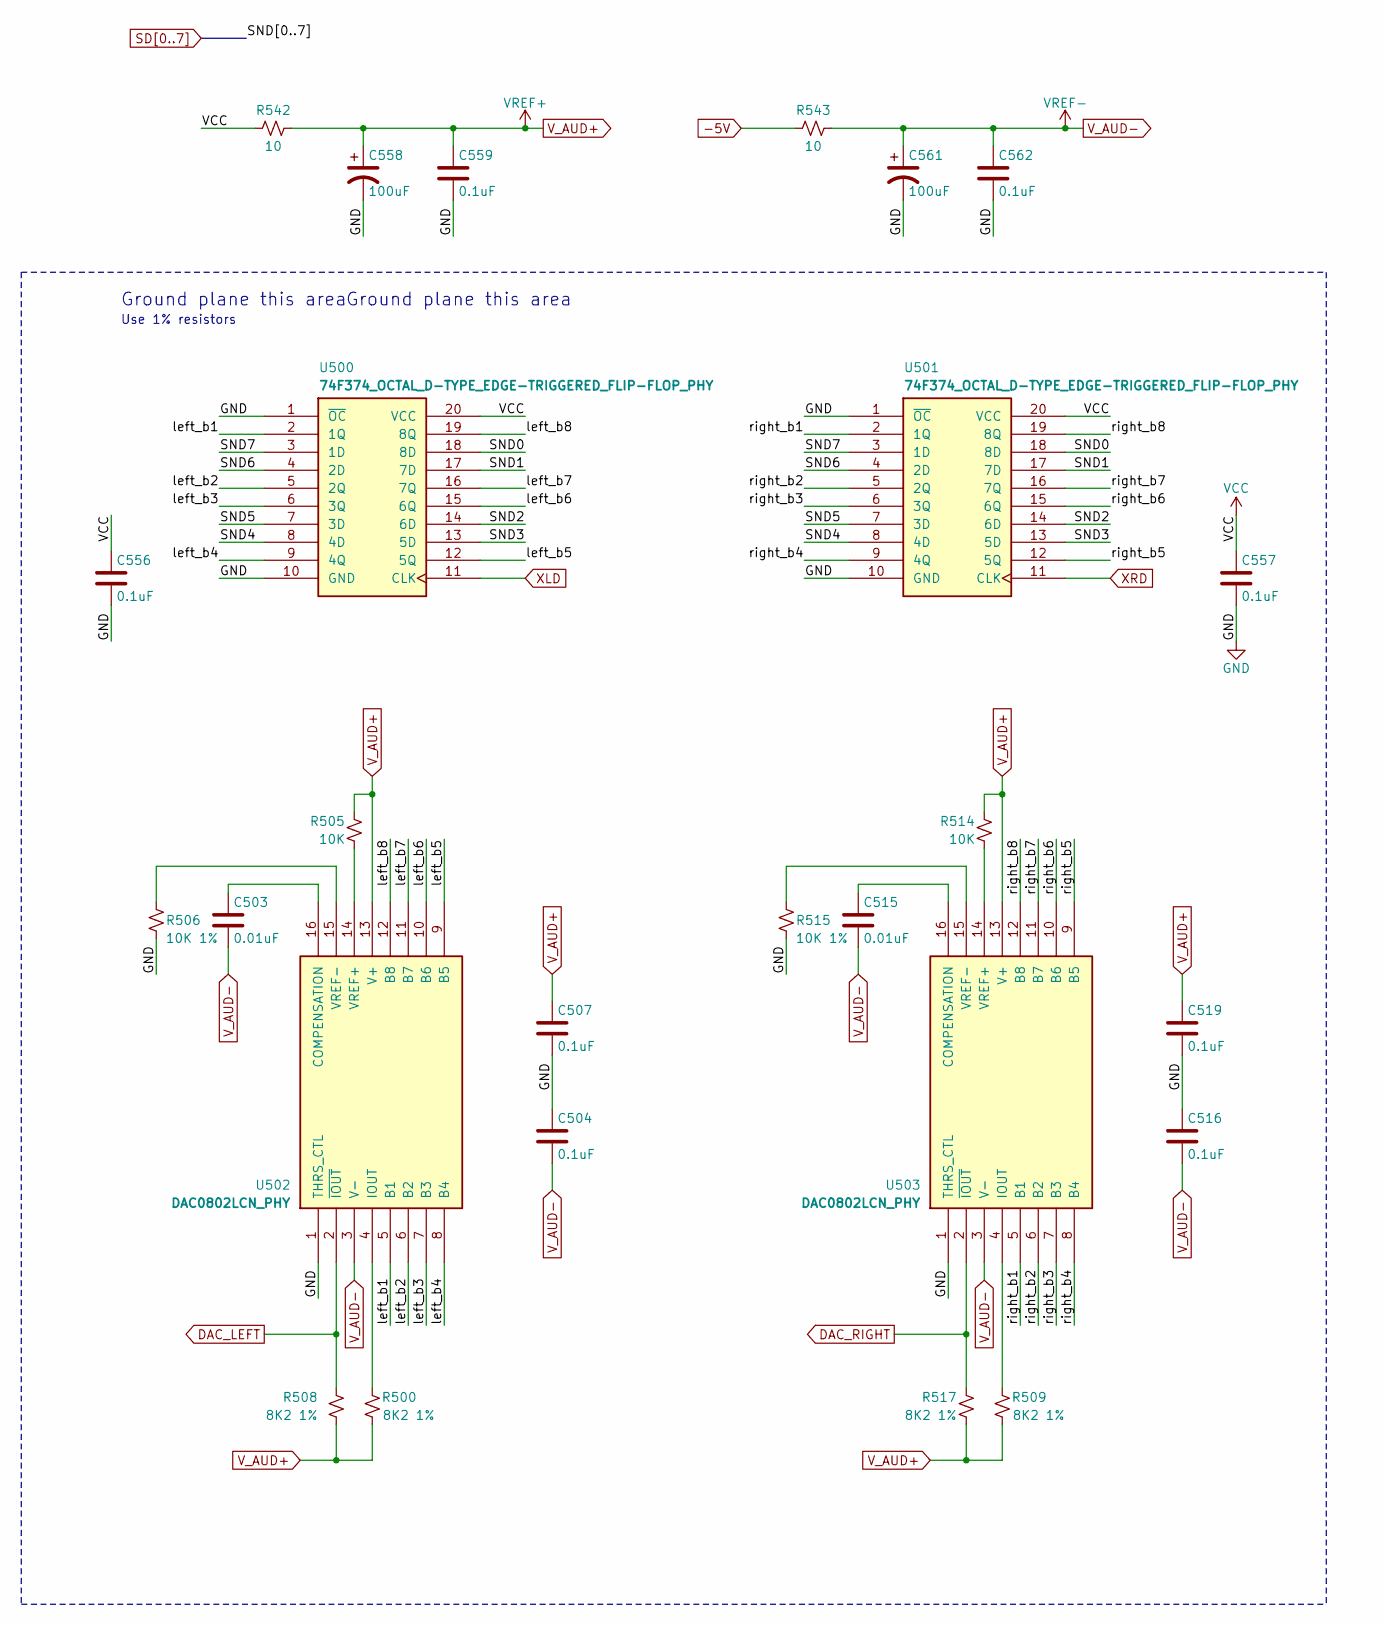
[picture p31: schematic subsheet_502.kicad_sch]

Parts:
C503, C515: 0.01uF; Passive_THT_capacitor_W2.54mm_L10.16mm
C504, C507, C516, C519, C556, C557, C559, C562: 0.1uF; Passive_THT_capacitor_mlcc_W2.54mm_L7.62mm
C558, C561: 100uF; Passive_THT_capacitor_polarized_W6.35mm_L20.32mm
R500, R508, R509, R517: 8K2 1%; Passive_THT_resistor_W2.54mm_L12.70mm
R505, R514: 10K; Passive_THT_resistor_W2.54mm_L12.70mm
R506, R515: 10K 1%; Passive_THT_resistor_W2.54mm_L12.70mm
R542, R543: 10; Passive_THT_resistor_W2.54mm_L12.70mm
U500, U501: 74F374_OCTAL_D-TYPE_EDGE-TRIGGERED_FLIP-FLOP_PHY; DIP-20_W7.62mm_LongPads
U502, U503: DAC0802LCN_PHY; DIP-16_W7.62mm_LongPads

Connections:
-5V: R543.2
DAC_LEFT: R508.2, U502.2 (~IOUT)
DAC_RIGHT: R517.2, U503.2 (~IOUT)
GND: C504.1, C507.2, C516.1, C519.2, C556.2, C557.2, C558.2, C559.2, C561.2, C562.2, R506.2, R515.2, U500.1 (~OC), U500.10 (GND), U501.1 (~OC), U501.10 (GND), U502.1 (THRS_CTL), U503.1 (THRS_CTL)
unnamed: C503.1, U502.16 (COMPENSATION)
unnamed: C515.1, U503.16 (COMPENSATION)
unnamed: R500.2, U502.4 (IOUT)
unnamed: R505.2, U502.14 (VREF+)
unnamed: R506.1, U502.15 (VREF-)
unnamed: R509.2, U503.4 (IOUT)
unnamed: R514.2, U503.14 (VREF+)
unnamed: R515.1, U503.15 (VREF-)
SND0: U500.18 (8D), U501.18 (8D)
SND1: U500.17 (7D), U501.17 (7D)
SND2: U500.14 (6D), U501.14 (6D)
SND3: U500.13 (5D), U501.13 (5D)
SND4: U500.8 (4D), U501.8 (4D)
SND5: U500.7 (3D), U501.7 (3D)
SND6: U500.4 (2D), U501.4 (2D)
SND7: U500.3 (1D), U501.3 (1D)
VCC: C556.1, C557.1, R542.2, U500.20 (VCC), U501.20 (VCC)
V_AUD+: C507.1, C519.1, C558.1, C559.1, R500.1, R505.1, R508.1, R509.1, R514.1, R517.1, R542.1, U502.13 (V+), U503.13 (V+)
V_AUD-: C503.2, C504.2, C515.2, C516.2, C561.1, C562.1, R543.1, U502.3 (V-), U503.3 (V-)
XLD: U500.11 (CLK)
XRD: U501.11 (CLK)
left_b1: U500.2 (1Q), U502.5 (B1)
left_b2: U500.5 (2Q), U502.6 (B2)
left_b3: U500.6 (3Q), U502.7 (B3)
left_b4: U500.9 (4Q), U502.8 (B4)
left_b5: U500.12 (5Q), U502.9 (B5)
left_b6: U500.15 (6Q), U502.10 (B6)
left_b7: U500.16 (7Q), U502.11 (B7)
left_b8: U500.19 (8Q), U502.12 (B8)
right_b1: U501.2 (1Q), U503.5 (B1)
right_b2: U501.5 (2Q), U503.6 (B2)
right_b3: U501.6 (3Q), U503.7 (B3)
right_b4: U501.9 (4Q), U503.8 (B4)
right_b5: U501.12 (5Q), U503.9 (B5)
right_b6: U501.15 (6Q), U503.10 (B6)
right_b7: U501.16 (7Q), U503.11 (B7)
right_b8: U501.19 (8Q), U503.12 (B8)

Notes on the sheet:
Ground plane this area
Use 1% resistors
