sporniket/kicad-conversions--atari-ste-motherboard--c300780-001/subsheet_503.kicad_sch

## KiCad design subsheet_503.kicad_sch (2025-09-03)

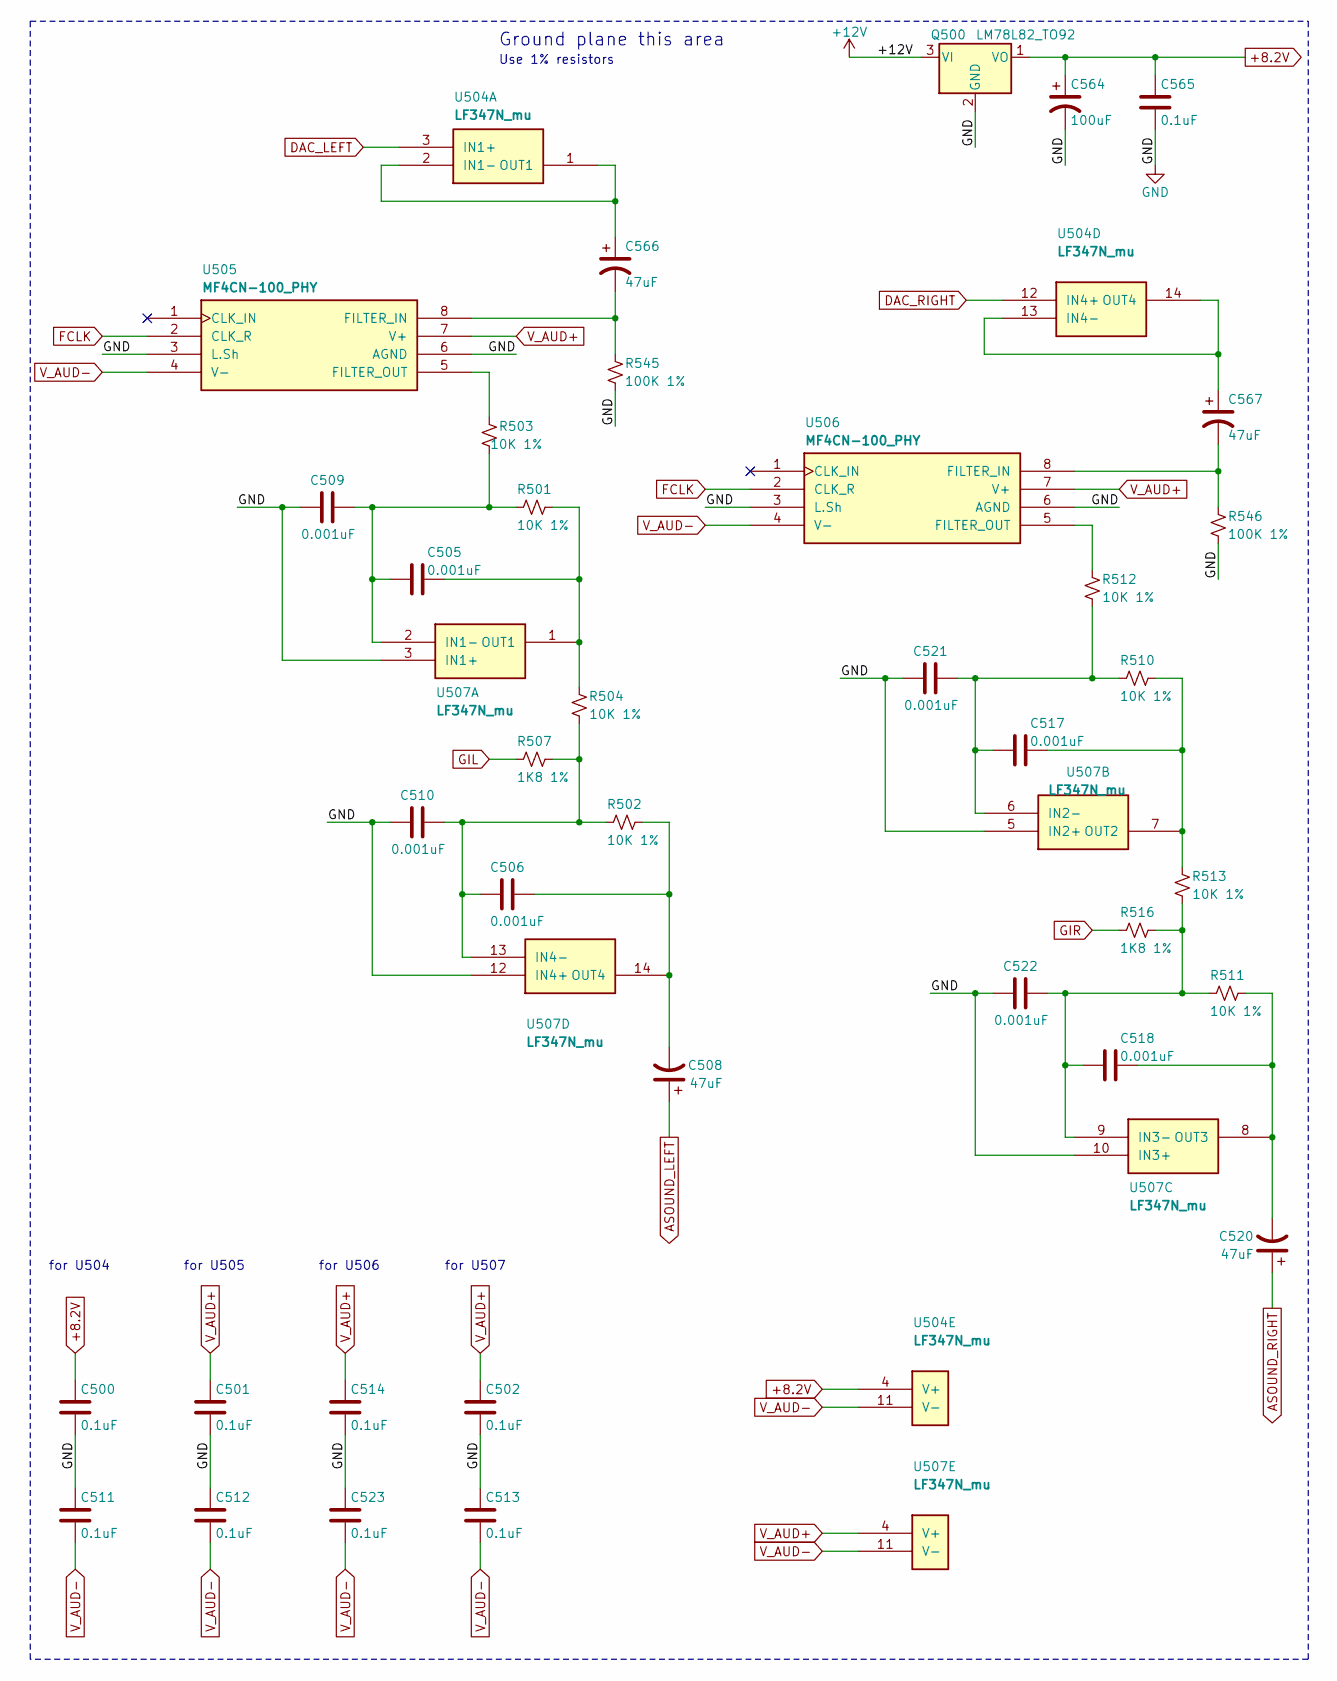
[picture p32: schematic subsheet_503.kicad_sch]

Parts:
C500, C501, C502, C511, C512, C513, C514, C523, C565: 0.1uF; Passive_THT_capacitor_mlcc_W2.54mm_L7.62mm
C505, C506, C509, C510, C517, C518, C521, C522: 0.001uF; Passive_THT_capacitor_W2.54mm_L10.16mm
C508, C520: 47uF; Passive_THT_capacitor_polarized_W6.35mm_L20.32mm
C564: 100uF; Passive_THT_capacitor_polarized_W6.35mm_L20.32mm
C566, C567: 47uF; Passive_THT_capacitor_polarized_rad_D5.08mm_P2.54mm_H12.70mm
Q500: LM78L82_TO92; TO-92_Inline_Wide
R501, R502, R503, R504, R510, R511, R512, R513: 10K 1%; Passive_THT_resistor_W2.54mm_L12.70mm
R507, R516: 1K8 1%; Passive_THT_resistor_W2.54mm_L12.70mm
R545, R546: 100K 1%; Passive_THT_resistor_W2.54mm_L12.70mm
U504, U507: LF347N_mu; DIP-14_W7.62mm_LongPads
U505, U506: MF4CN-100_PHY; DIP-8_W7.62mm_LongPads

Connections:
+8.2V: C500.1, C564.1, C565.1, Q500.1 (VO), U504.4 (V+)
+12V: Q500.3 (VI)
ASOUND_LEFT: C508.1
ASOUND_RIGHT: C520.1
DAC_LEFT: U504.3 (IN1+)
DAC_RIGHT: U504.12 (IN4+)
FCLK: U505.2 (CLK_R), U506.2 (CLK_R)
GIL: R507.2
GIR: R516.2
GND: C500.2, C501.2, C502.2, C509.2, C510.2, C511.1, C512.1, C513.1, C514.2, C521.2, C522.2, C523.1, C564.2, C565.2, Q500.2 (GND), R545.2, R546.2, U505.3 (L.Sh), U505.6 (AGND), U506.3 (L.Sh), U506.6 (AGND), U507.3 (IN1+), U507.5 (IN2+), U507.10 (IN3+), U507.12 (IN4+)
unnamed: C505.1, R501.1, R504.2, U507.1 (OUT1)
unnamed: C505.2, C509.1, R501.2, R503.1, U507.2 (IN1-)
unnamed: C506.1, C508.2, R502.1, U507.14 (OUT4)
unnamed: C506.2, C510.1, R502.2, R504.1, R507.1, U507.13 (IN4-)
unnamed: C517.1, R510.1, R513.2, U507.7 (OUT2)
unnamed: C517.2, C521.1, R510.2, R512.1, U507.6 (IN2-)
unnamed: C518.1, C520.2, R511.1, U507.8 (OUT3)
unnamed: C518.2, C522.1, R511.2, R513.1, R516.1, U507.9 (IN3-)
unnamed: C566.1, U504.1 (OUT1), U504.2 (IN1-)
unnamed: C566.2, R545.1, U505.8 (FILTER_IN)
unnamed: C567.1, U504.13 (IN4-), U504.14 (OUT4)
unnamed: C567.2, R546.1, U506.8 (FILTER_IN)
unnamed: R503.2, U505.5 (FILTER_OUT)
unnamed: R512.2, U506.5 (FILTER_OUT)
V_AUD+: C501.1, C502.1, C514.1, U505.7 (V+), U506.7 (V+), U507.4 (V+)
V_AUD-: C511.2, C512.2, C513.2, C523.2, U504.11 (V-), U505.4 (V-), U506.4 (V-), U507.11 (V-)

Notes on the sheet:
for U504
for U505
for U506
Ground plane this area
Use 1% resistors
for U507
