sporniket/kicad-conversions--atari-ste-motherboard--c300780-001/subsheet_504.kicad_sch

## KiCad design subsheet_504.kicad_sch (2025-09-03)

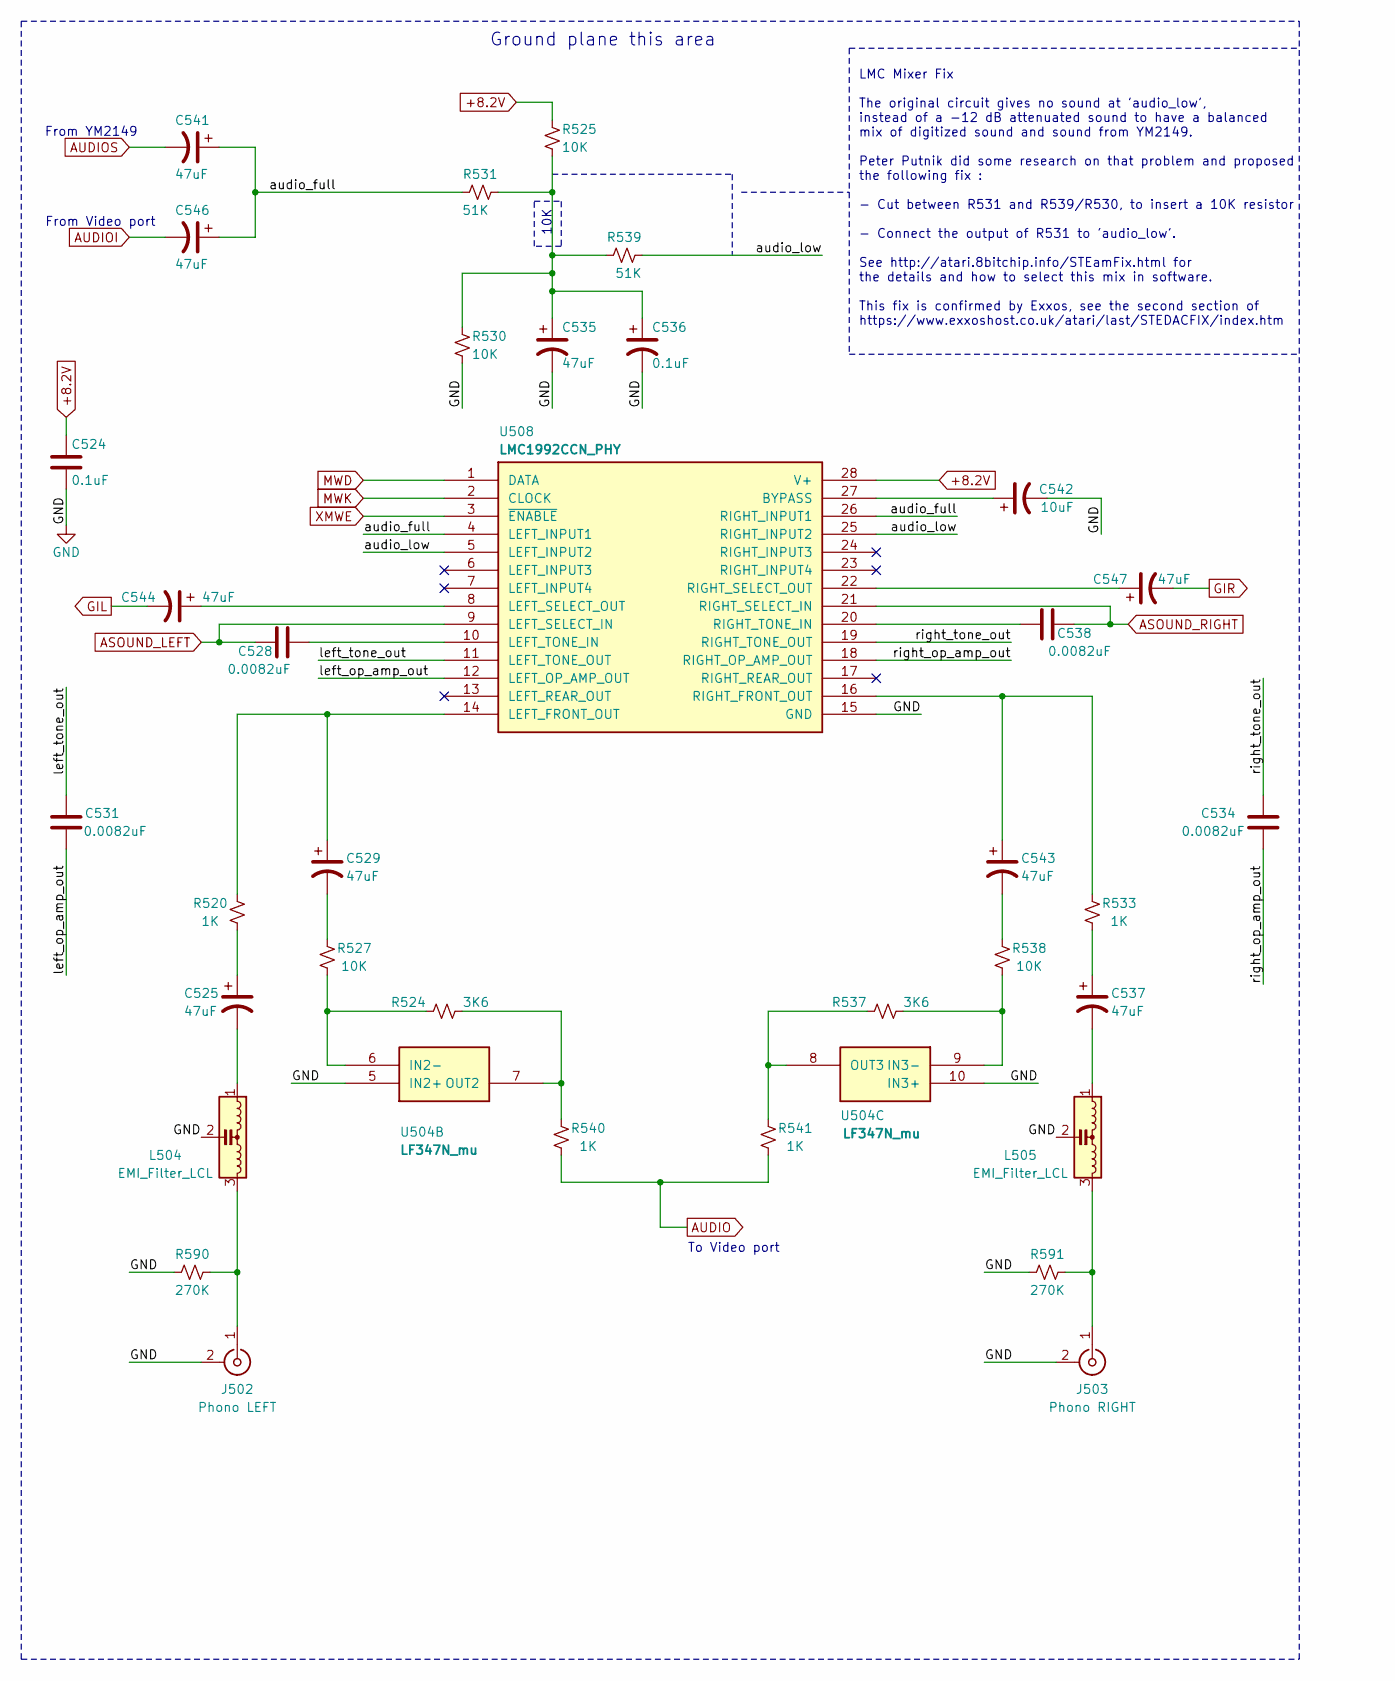
[picture p33: schematic subsheet_504.kicad_sch]

Parts:
C524, C536: 0.1uF; Passive_THT_capacitor_mlcc_W2.54mm_L7.62mm
C525, C529, C535, C537, C541, C543, C544, C546, C547: 47uF; Passive_THT_capacitor_polarized_W6.35mm_L20.32mm
C528, C531, C534, C538: 0.0082uF; Passive_THT_capacitor_mlcc_W2.54mm_L10.16mm
C542: 10uF; Passive_THT_capacitor_polarized_W5.08mm_L17.78mm
J502: Phono LEFT; socket-rca-5-pins
J503: Phono RIGHT; socket-rca-5-pins
L504, L505: EMI_Filter_LCL; Passive_THT_EMI_filter_W5.08mm_L7.62mm
R520, R533, R540, R541: 1K; Passive_THT_resistor_W2.54mm_L12.70mm
R524, R537: 3K6; Passive_THT_resistor_W2.54mm_L12.70mm
R525, R527, R530, R538: 10K; Passive_THT_resistor_W2.54mm_L12.70mm
R531, R539: 51K; Passive_THT_resistor_W2.54mm_L12.70mm
R590, R591: 270K; Passive_THT_resistor_W2.54mm_L12.70mm
U504: LF347N_mu; DIP-14_W7.62mm_LongPads
U508: LMC1992CCN_PHY; DIP-28_W15.24mm_LongPads

Connections:
+8.2V: C524.1, R525.1, U508.28 (V+)
ASOUND_LEFT: C528.1, U508.9 (LEFT_SELECT_IN)
ASOUND_RIGHT: C538.1, U508.21 (RIGHT_SELECT_IN)
AUDIO: R540.1, R541.1
AUDIOI: C546.2
AUDIOS: C541.2
GIL: C544.2
GIR: C547.2
GND: C524.2, C535.2, C536.2, C542.2, J502.2 (Ext), J503.2 (Ext), L504.2, L505.2, R530.2, R590.2, R591.2, U504.5 (IN2+), U504.10 (IN3+), U508.15 (GND)
MWD: U508.1 (DATA)
MWK: U508.2 (CLOCK)
unnamed: C525.1, R520.1
unnamed: C525.2, L504.1
unnamed: C528.2, U508.10 (LEFT_TONE_IN)
unnamed: C529.1, R520.2, U508.14 (LEFT_FRONT_OUT)
unnamed: C529.2, R527.2
unnamed: C535.1, C536.1, R525.2, R530.1, R531.2, R539.1
unnamed: C537.1, R533.1
unnamed: C537.2, L505.1
unnamed: C538.2, U508.20 (RIGHT_TONE_IN)
unnamed: C542.1, U508.27 (BYPASS)
unnamed: C543.1, R533.2, U508.16 (RIGHT_FRONT_OUT)
unnamed: C543.2, R538.2
unnamed: C544.1, U508.8 (LEFT_SELECT_OUT)
unnamed: C547.1, U508.22 (RIGHT_SELECT_OUT)
unnamed: J502.1 (In), L504.3, R590.1
unnamed: J503.1 (In), L505.3, R591.1
unnamed: R524.1, R540.2, U504.7 (OUT2)
unnamed: R524.2, R527.1, U504.6 (IN2-)
unnamed: R537.1, R541.2, U504.8 (OUT3)
unnamed: R537.2, R538.1, U504.9 (IN3-)
XMWE: U508.3 (~ENABLE)
audio_full: C541.1, C546.1, R531.1, U508.4 (LEFT_INPUT1), U508.26 (RIGHT_INPUT1)
audio_low: R539.2, U508.5 (LEFT_INPUT2), U508.25 (RIGHT_INPUT2)
left_op_amp_out: C531.1, U508.12 (LEFT_OP_AMP_OUT)
left_tone_out: C531.2, U508.11 (LEFT_TONE_OUT)
right_op_amp_out: C534.1, U508.18 (RIGHT_OP_AMP_OUT)
right_tone_out: C534.2, U508.19 (RIGHT_TONE_OUT)

Notes on the sheet:
LMC Mixer Fix The original circuit gives no sound at 'audio_low', instead of a -12 dB attenuated sound to have a balanced mix of digitized sound and sound from YM2149. Peter Putnik did some research on that problem and proposed the following fix : - Cut between R531 and R539/R530, to insert a 10K r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
From YM2149
To Video port
Ground plane this area
From Video port
10K
