sporniket/kicad-conversions--atari-ste-motherboard--c300780-001/subsheet_600.kicad_sch

## KiCad design subsheet_600.kicad_sch (2025-09-03)

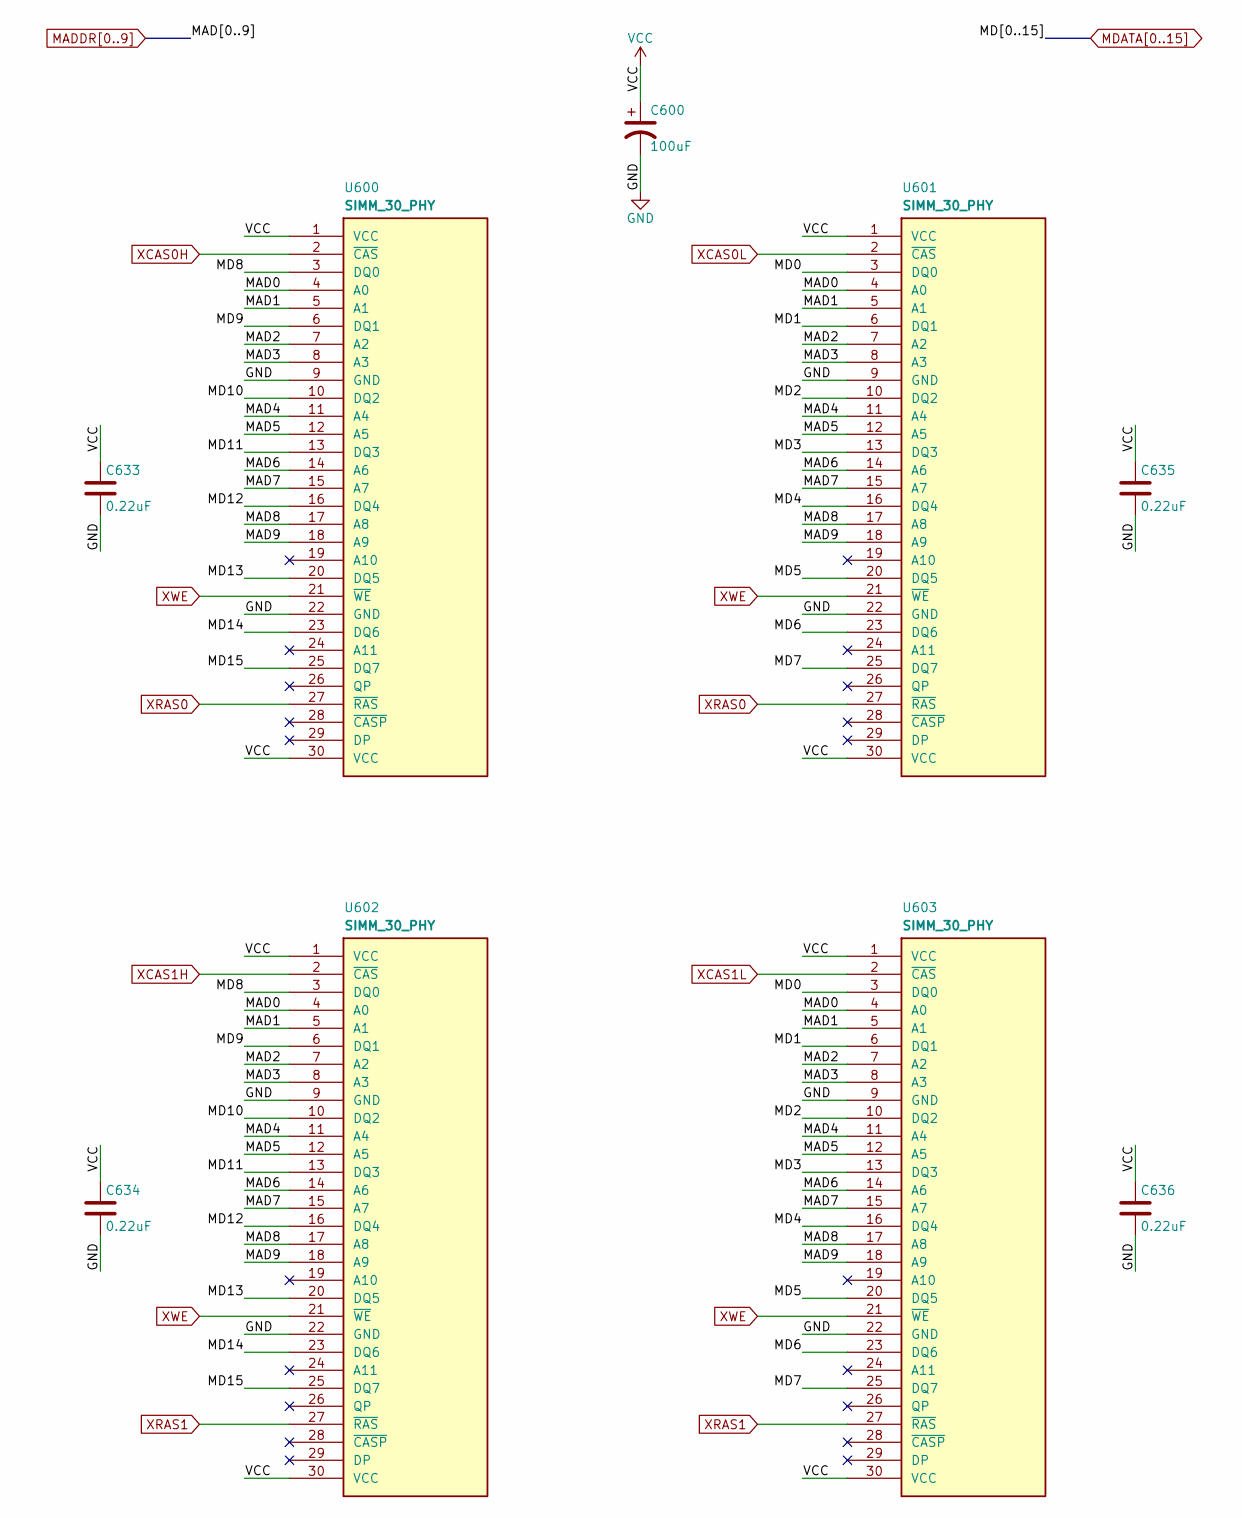
[picture p34: schematic subsheet_600.kicad_sch]

Parts:
C600: 100uF; Passive_THT_capacitor_polarized_W6.35mm_L20.32mm
C633, C634, C635, C636: 0.22uF; Passive_THT_capacitor_mlcc_W2.54mm_L10.16mm
U600, U601, U602, U603: SIMM_30_PHY; socket-simm-30-P2.54mm

Connections:
GND: C600.2, C633.2, C634.2, C635.2, C636.2, U600.9 (GND), U600.22 (GND), U601.9 (GND), U601.22 (GND), U602.9 (GND), U602.22 (GND), U603.9 (GND), U603.22 (GND)
MAD0: U600.4 (A0), U601.4 (A0), U602.4 (A0), U603.4 (A0)
MAD1: U600.5 (A1), U601.5 (A1), U602.5 (A1), U603.5 (A1)
MAD2: U600.7 (A2), U601.7 (A2), U602.7 (A2), U603.7 (A2)
MAD3: U600.8 (A3), U601.8 (A3), U602.8 (A3), U603.8 (A3)
MAD4: U600.11 (A4), U601.11 (A4), U602.11 (A4), U603.11 (A4)
MAD5: U600.12 (A5), U601.12 (A5), U602.12 (A5), U603.12 (A5)
MAD6: U600.14 (A6), U601.14 (A6), U602.14 (A6), U603.14 (A6)
MAD7: U600.15 (A7), U601.15 (A7), U602.15 (A7), U603.15 (A7)
MAD8: U600.17 (A8), U601.17 (A8), U602.17 (A8), U603.17 (A8)
MAD9: U600.18 (A9), U601.18 (A9), U602.18 (A9), U603.18 (A9)
MD0: U601.3 (DQ0), U603.3 (DQ0)
MD1: U601.6 (DQ1), U603.6 (DQ1)
MD2: U601.10 (DQ2), U603.10 (DQ2)
MD3: U601.13 (DQ3), U603.13 (DQ3)
MD4: U601.16 (DQ4), U603.16 (DQ4)
MD5: U601.20 (DQ5), U603.20 (DQ5)
MD6: U601.23 (DQ6), U603.23 (DQ6)
MD7: U601.25 (DQ7), U603.25 (DQ7)
MD8: U600.3 (DQ0), U602.3 (DQ0)
MD9: U600.6 (DQ1), U602.6 (DQ1)
MD10: U600.10 (DQ2), U602.10 (DQ2)
MD11: U600.13 (DQ3), U602.13 (DQ3)
MD12: U600.16 (DQ4), U602.16 (DQ4)
MD13: U600.20 (DQ5), U602.20 (DQ5)
MD14: U600.23 (DQ6), U602.23 (DQ6)
MD15: U600.25 (DQ7), U602.25 (DQ7)
VCC: C600.1, C633.1, C634.1, C635.1, C636.1, U600.1 (VCC), U600.30 (VCC), U601.1 (VCC), U601.30 (VCC), U602.1 (VCC), U602.30 (VCC), U603.1 (VCC), U603.30 (VCC)
XCAS0H: U600.2 (~CAS)
XCAS0L: U601.2 (~CAS)
XCAS1H: U602.2 (~CAS)
XCAS1L: U603.2 (~CAS)
XRAS0: U600.27 (~RAS), U601.27 (~RAS)
XRAS1: U602.27 (~RAS), U603.27 (~RAS)
XWE: U600.21 (~WE), U601.21 (~WE), U602.21 (~WE), U603.21 (~WE)
