sporniket/kicad-conversions--atari-ste-motherboard--c300780-001/subsheet_601.kicad_sch

## KiCad design subsheet_601.kicad_sch (2025-09-03)

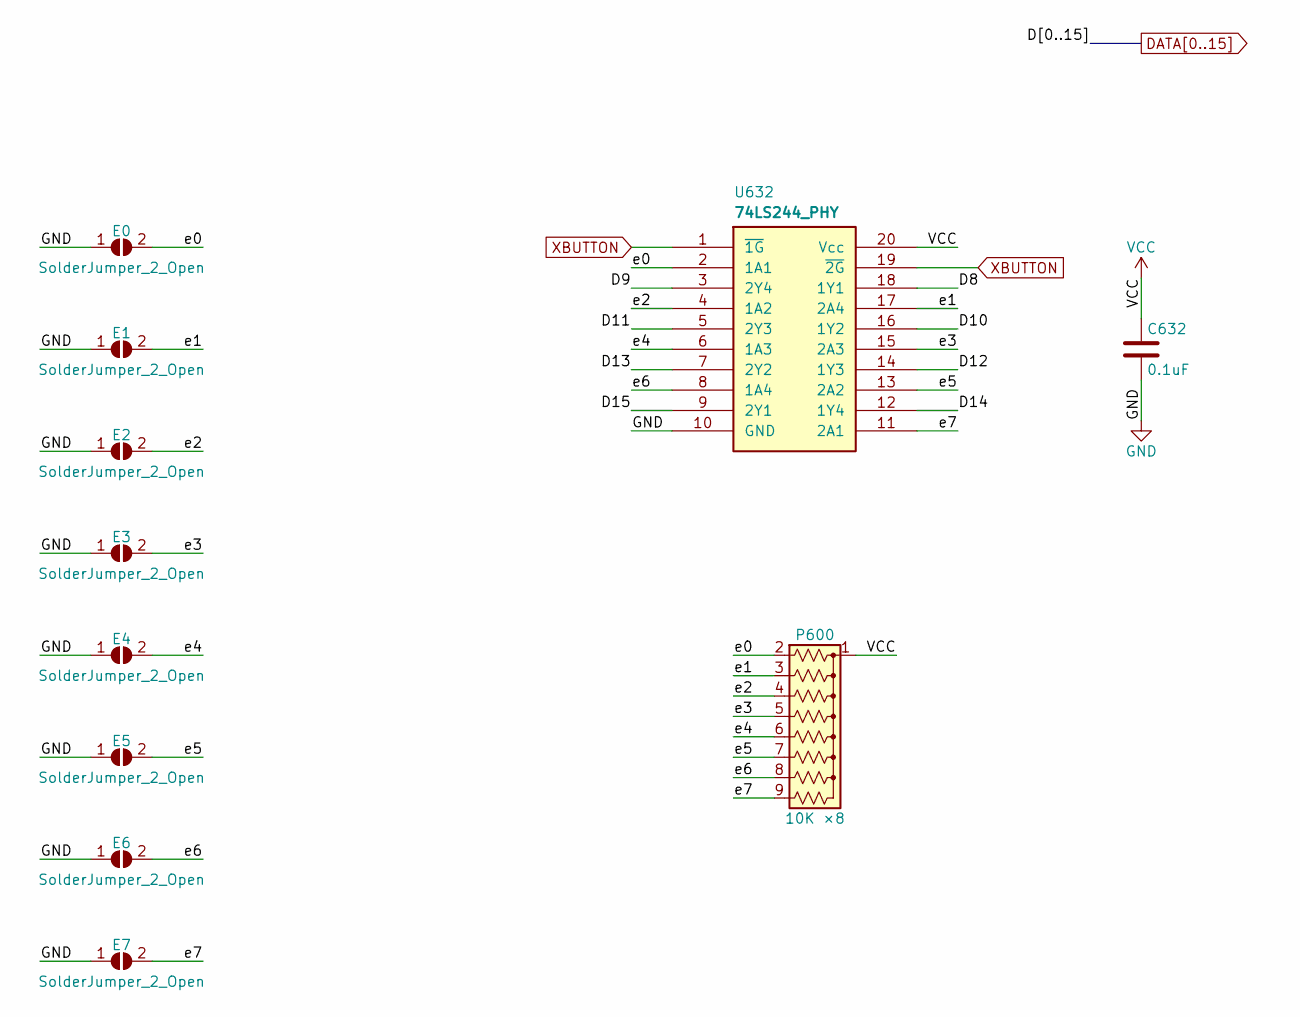
[picture p35: schematic subsheet_601.kicad_sch]

Parts:
C632: 0.1uF; Passive_THT_capacitor_mlcc_W2.54mm_L7.62mm
E0, E1, E2, E3, E4, E5, E6, E7: SolderJumper_2_Open; SolderJumper-2_P1.3mm_Open_Pad1.0x1.5mm
P600: 10K ×8; R_Array_SIP9
U632: 74LS244_PHY; DIP-20_W7.62mm_LongPads

Connections:
D8: U632.18 (1Y1)
D9: U632.3 (2Y4)
D10: U632.16 (1Y2)
D11: U632.5 (2Y3)
D12: U632.14 (1Y3)
D13: U632.7 (2Y2)
D14: U632.12 (1Y4)
D15: U632.9 (2Y1)
GND: C632.2, E0.1 (A), E1.1 (A), E2.1 (A), E3.1 (A), E4.1 (A), E5.1 (A), E6.1 (A), E7.1 (A), U632.10 (GND)
VCC: C632.1, P600.1 (common), U632.20 (Vcc)
XBUTTON: U632.1 (~1G), U632.19 (~2G)
e0: E0.2 (B), P600.2 (R1), U632.2 (1A1)
e1: E1.2 (B), P600.3 (R2), U632.17 (2A4)
e2: E2.2 (B), P600.4 (R3), U632.4 (1A2)
e3: E3.2 (B), P600.5 (R4), U632.15 (2A3)
e4: E4.2 (B), P600.6 (R5), U632.6 (1A3)
e5: E5.2 (B), P600.7 (R6), U632.13 (2A2)
e6: E6.2 (B), P600.8 (R7), U632.8 (1A4)
e7: E7.2 (B), P600.9 (R8), U632.11 (2A1)
